WA1CYB/SDR_Gen2/AD9361-sheet-2-page7.kicad_sch

## KiCad design AD9361-sheet-2-page7.kicad_sch (2026-04-03)

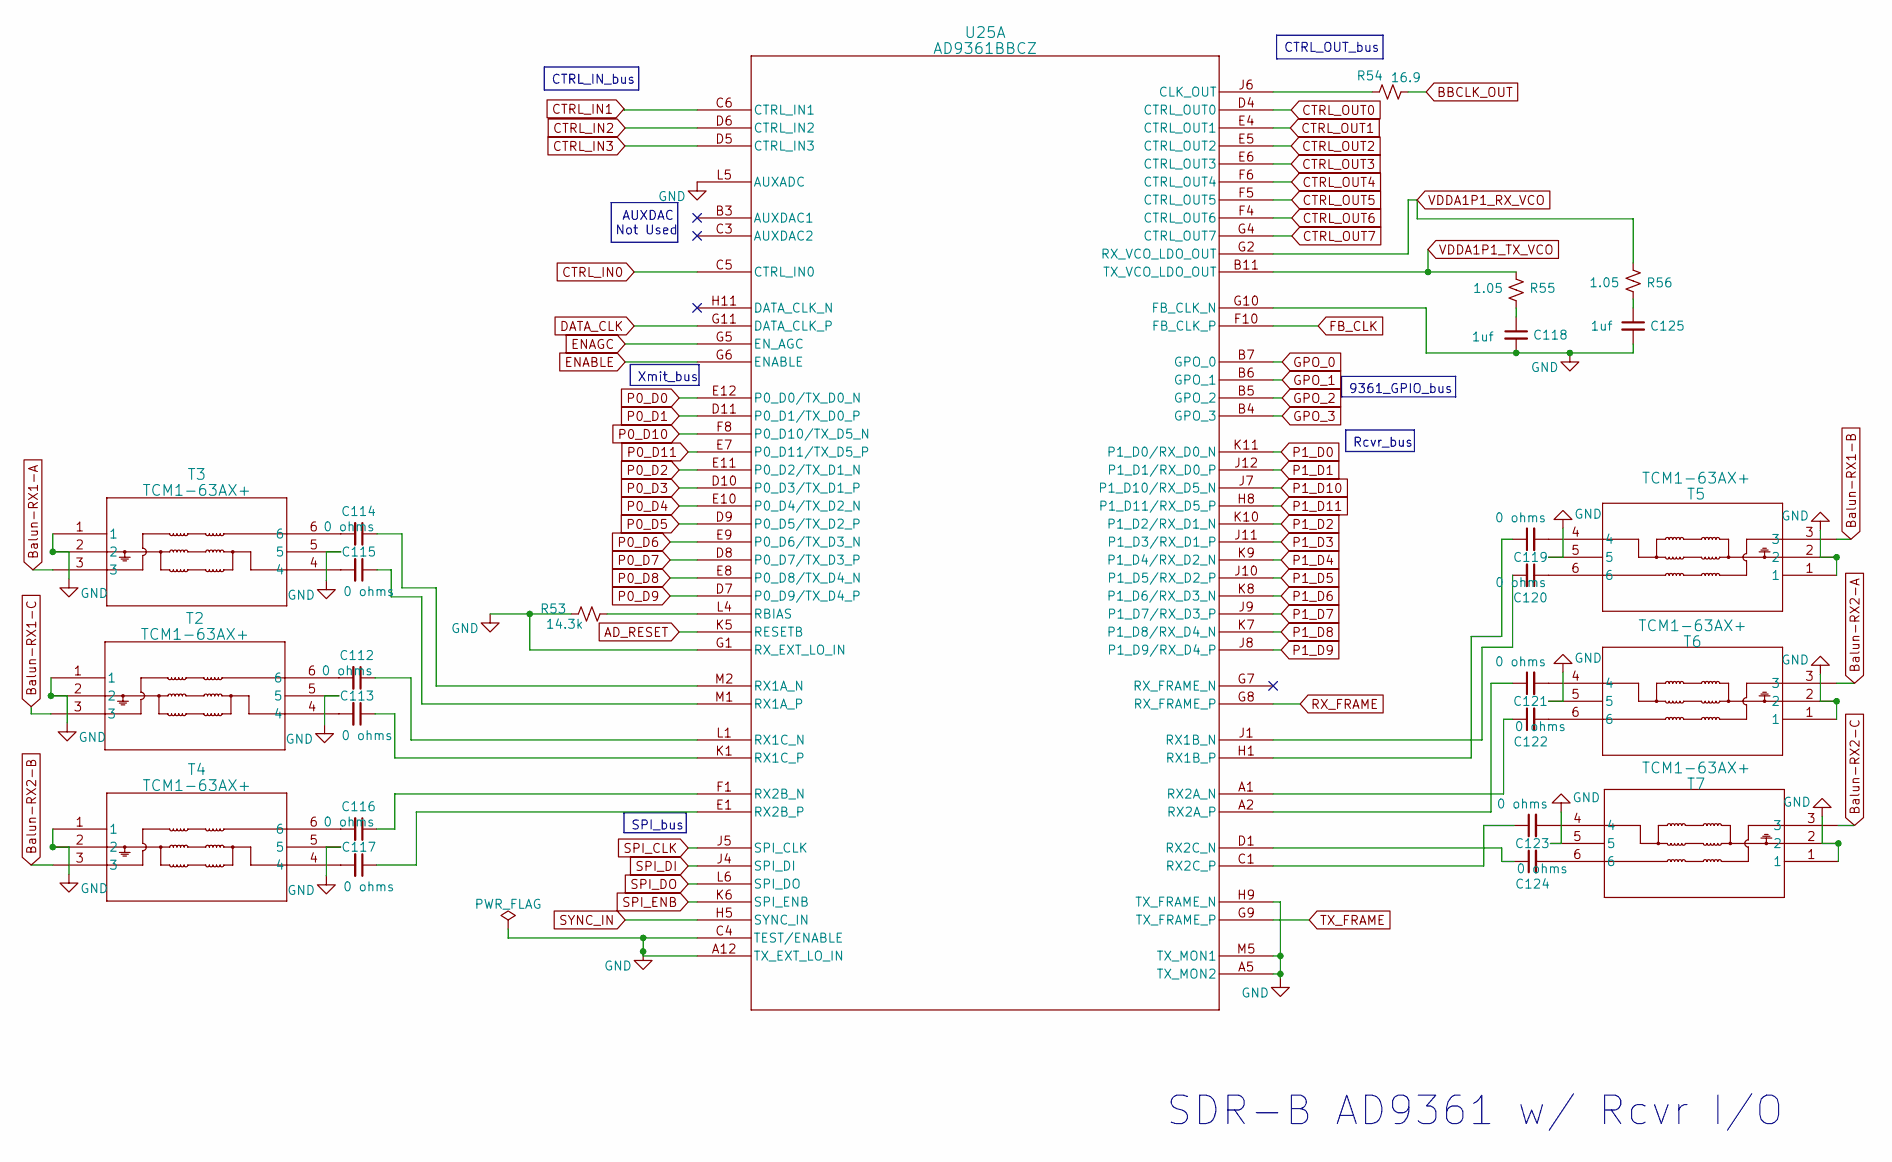
[picture p9: schematic AD9361-sheet-2-page7.kicad_sch]

Parts:
C112, C113, C114, C115, C116, C117, C119, C120, C121, C122, C123, C124: 0 ohms; C_0201_0603Metric
C118, C125: 1uf; C_0402_1005Metric
R53: 14.3k; R_0201_0603Metric
R54: 16.9; R_0201_0603Metric
R55, R56: 1.05; R_0201_0603Metric
T2, T3, T4, T5, T6, T7: TCM1-63AX+; DB1627_MNC
U25: AD9361BBCZ; BC_144_7_ADI

Connections:
AD_RESET: U25.K5 (RESETB)
BBCLK_OUT: R54.2
Balun-RX1-A: T3.3
Balun-RX1-B: T5.3
Balun-RX1-C: T2.3
Balun-RX2-A: T6.3
Balun-RX2-B: T4.3
Balun-RX2-C: T7.3
CTRL_IN0: U25.C5 (CTRL_IN0)
CTRL_IN1: U25.C6 (CTRL_IN1)
CTRL_IN2: U25.D6 (CTRL_IN2)
CTRL_IN3: U25.D5 (CTRL_IN3)
CTRL_OUT0: U25.D4 (CTRL_OUT0)
CTRL_OUT1: U25.E4 (CTRL_OUT1)
CTRL_OUT2: U25.E5 (CTRL_OUT2)
CTRL_OUT3: U25.E6 (CTRL_OUT3)
CTRL_OUT4: U25.F6 (CTRL_OUT4)
CTRL_OUT5: U25.F5 (CTRL_OUT5)
CTRL_OUT6: U25.F4 (CTRL_OUT6)
CTRL_OUT7: U25.G4 (CTRL_OUT7)
DATA_CLK: U25.G11 (DATA_CLK_P)
ENABLE: U25.G6 (ENABLE)
ENAGC: U25.G5 (EN_AGC)
FB_CLK: U25.F10 (FB_CLK_P)
GND: C118.2, C125.2, R53.1, T2.1, T2.2, T2.5, T3.1, T3.2, T3.5, T4.1, T4.2, T4.5, T5.1, T5.2, T5.5, T6.1, T6.2, T6.5, T7.1, T7.2, T7.5, U25.A5 (TX_MON2), U25.A12 (TX_EXT_LO_IN), U25.C4 (TEST/ENABLE), U25.G1 (RX_EXT_LO_IN), U25.G10 (FB_CLK_N), U25.H9 (TX_FRAME_N), U25.L5 (AUXADC), U25.M5 (TX_MON1)
GPO_0: U25.B7 (GPO_0)
GPO_1: U25.B6 (GPO_1)
GPO_2: U25.B5 (GPO_2)
GPO_3: U25.B4 (GPO_3)
unnamed: C112.1, U25.L1 (RX1C_N)
unnamed: C112.2, T2.6
unnamed: C113.1, U25.K1 (RX1C_P)
unnamed: C113.2, T2.4
unnamed: C114.1, U25.M2 (RX1A_N)
unnamed: C114.2, T3.6
unnamed: C115.1, U25.M1 (RX1A_P)
unnamed: C115.2, T3.4
unnamed: C116.1, U25.F1 (RX2B_N)
unnamed: C116.2, T4.6
unnamed: C117.1, U25.E1 (RX2B_P)
unnamed: C117.2, T4.4
unnamed: C118.1, R55.1
unnamed: C119.1, U25.H1 (RX1B_P)
unnamed: C119.2, T5.4
unnamed: C120.1, T5.6
unnamed: C120.2, U25.J1 (RX1B_N)
unnamed: C121.1, U25.A2 (RX2A_P)
unnamed: C121.2, T6.4
unnamed: C122.1, U25.A1 (RX2A_N)
unnamed: C122.2, T6.6
unnamed: C123.1, U25.C1 (RX2C_P)
unnamed: C123.2, T7.4
unnamed: C124.1, U25.D1 (RX2C_N)
unnamed: C124.2, T7.6
unnamed: C125.1, R56.1
unnamed: R53.2, U25.L4 (RBIAS)
unnamed: R54.1, U25.J6 (CLK_OUT)
P0_D0: U25.E12 (P0_D0/TX_D0_N)
P0_D1: U25.D11 (P0_D1/TX_D0_P)
P0_D2: U25.E11 (P0_D2/TX_D1_N)
P0_D3: U25.D10 (P0_D3/TX_D1_P)
P0_D4: U25.E10 (P0_D4/TX_D2_N)
P0_D5: U25.D9 (P0_D5/TX_D2_P)
P0_D6: U25.E9 (P0_D6/TX_D3_N)
P0_D7: U25.D8 (P0_D7/TX_D3_P)
P0_D8: U25.E8 (P0_D8/TX_D4_N)
P0_D9: U25.D7 (P0_D9/TX_D4_P)
P0_D10: U25.F8 (P0_D10/TX_D5_N)
P0_D11: U25.E7 (P0_D11/TX_D5_P)
P1_D0: U25.K11 (P1_D0/RX_D0_N)
P1_D1: U25.J12 (P1_D1/RX_D0_P)
P1_D2: U25.K10 (P1_D2/RX_D1_N)
P1_D3: U25.J11 (P1_D3/RX_D1_P)
P1_D4: U25.K9 (P1_D4/RX_D2_N)
P1_D5: U25.J10 (P1_D5/RX_D2_P)
P1_D6: U25.K8 (P1_D6/RX_D3_N)
P1_D7: U25.J9 (P1_D7/RX_D3_P)
P1_D8: U25.K7 (P1_D8/RX_D4_N)
P1_D9: U25.J8 (P1_D9/RX_D4_P)
P1_D10: U25.J7 (P1_D10/RX_D5_N)
P1_D11: U25.H8 (P1_D11/RX_D5_P)
RX_FRAME: U25.G8 (RX_FRAME_P)
SPI_CLK: U25.J5 (SPI_CLK)
SPI_DI: U25.J4 (SPI_DI)
SPI_DO: U25.L6 (SPI_DO)
SPI_ENB: U25.K6 (SPI_ENB)
SYNC_IN: U25.H5 (SYNC_IN)
TX_FRAME: U25.G9 (TX_FRAME_P)
VDDA1P1_RX_VCO: R56.2, U25.G2 (RX_VCO_LDO_OUT)
VDDA1P1_TX_VCO: R55.2, U25.B11 (TX_VCO_LDO_OUT)

Notes on the sheet:
AUXDAC Not Used
SDR-B AD9361 w/ Rcvr I/O
Rcvr_bus
9361_GPIO_bus
Xmit_bus
CTRL_OUT_bus
SPI_bus
CTRL_IN_bus
