WA1CYB/SDR_Gen2/AD9361-sheet-3-page8.kicad_sch

## KiCad design AD9361-sheet-3-page8.kicad_sch (2026-04-03)

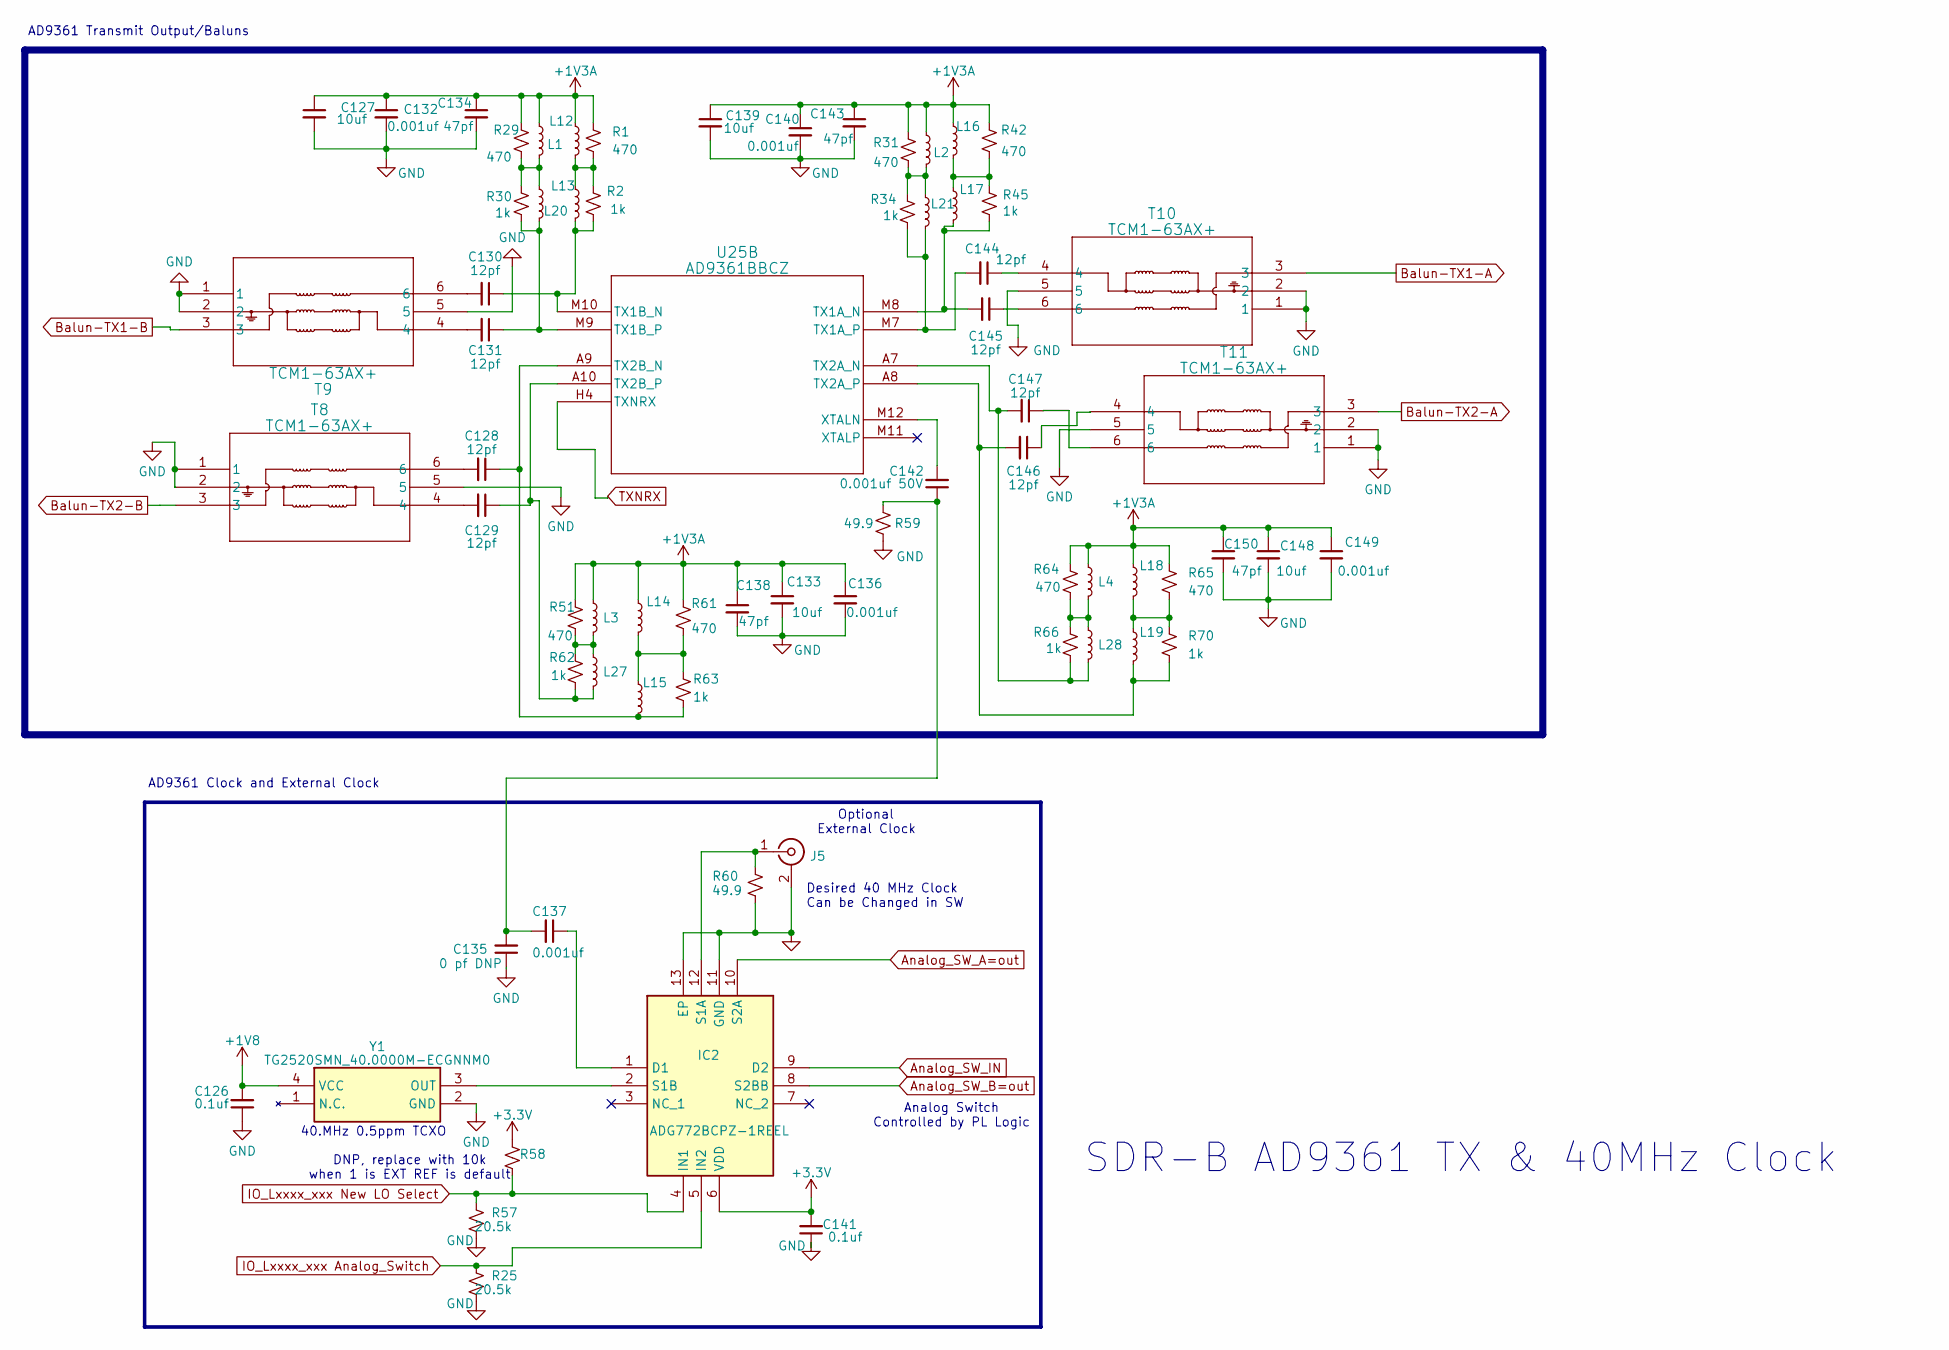
[picture p10: schematic AD9361-sheet-3-page8.kicad_sch]

Parts:
C126, C141: 0.1uf; C_0201_0603Metric
C127, C133, C139, C148: 10uf; C_0805_2012Metric
C128, C129, C130, C131, C144, C145, C146, C147: 12pf; C_0201_0603Metric
C132, C136, C137, C140, C149: 0.001uf; C_0201_0603Metric
C134, C138, C143, C150: 47pf; C_0603_1608Metric
C135: 0 pf DNP; C_0603_1608Metric
C142: 0.001uf 50V; C_0805_2012Metric
IC2: ADG772BCPZ-1REEL; QFN50P300X300X80-13N-D; Manufacturer_Part_Number ADG772BCPZ-1REEL; Mouser Part Number 584-ADG772BCPZ-1R
J5: Ext Clock; MMCX_Molex_73415-1471_Vertical
L1, L2, L3, L4, L12, L14, L16, L18: 330nh MLJ1005WR33JT000; INDC1005X55N
L13, L15, L17, L19, L20, L21, L27, L28: 33nh LQW15AN33NJ00D; LQW15CNR20J00B
R1, R29, R31, R42, R51, R61, R64, R65: 470; R_0402_1005Metric
R2, R30, R34, R45, R62, R63, R66, R70: 1k; R_0402_1005Metric
R25, R57: 20.5k; R_0201_0603Metric
R58: DNP; R_0603_1608Metric
R59, R60: 49.9; R_0201_0603Metric
T8, T9, T10, T11: TCM1-63AX+; DB1627_MNC
U25: AD9361BBCZ; BC_144_7_ADI
Y1: TG2520SMN_40.0000M-ECGNNM0; TG2520SMN400000MECGNNM0; Manufacturer_Part_Number TG2520SMN 40.0000M-ECGNNM0; Mouser Part Number 732-2520SMN40ECGNNM0

Connections:
+1V3A: C127.1, C132.1, C133.1, C134.1, C136.1, C138.1, C139.1, C140.1, C143.1, C148.1, C149.1, C150.1, L1.1, L2.1, L3.1, L4.1, L12.1, L14.1, L16.1, L18.1, R1.1, R29.1, R31.1, R42.1, R51.1, R61.1, R64.1, R65.1
+1V8: C126.2, Y1.4 (VCC)
+3.3V: C141.2, IC2.6 (VDD), R58.1
Analog_SW_A=out: IC2.10 (S2A)
Analog_SW_B=out: IC2.8 (S2BB)
Analog_SW_IN: IC2.9 (D2)
Balun-TX1-A: T10.3
Balun-TX1-B: T9.3
Balun-TX2-A: T11.3
Balun-TX2-B: T8.3
GND: C126.1, C127.2, C132.2, C133.2, C134.2, C135.1, C136.2, C138.2, C139.2, C140.2, C141.1, C143.2, C148.2, C149.2, C150.2, IC2.11 (GND), IC2.13 (EP), J5.2 (Ext), R25.2, R57.2, R59.2, R60.2, T8.1, T8.2, T8.5, T9.1, T9.2, T9.5, T10.1, T10.2, T10.5, T11.1, T11.2, T11.5, Y1.2 (GND)
IO_Lxxxx_xxx Analog_Switch: IC2.5 (IN2), R25.1
IO_Lxxxx_xxx New LO Select: IC2.4 (IN1), R57.1, R58.2
unnamed: C128.1, L15.2, R63.2, U25.A9 (TX2B_N)
unnamed: C128.2, T8.6
unnamed: C129.1, L27.2, R62.2, U25.A10 (TX2B_P)
unnamed: C129.2, T8.4
unnamed: C130.1, L13.2, R2.2, U25.M10 (TX1B_N)
unnamed: C130.2, T9.6
unnamed: C131.1, L20.2, R30.2, U25.M9 (TX1B_P)
unnamed: C131.2, T9.4
unnamed: C135.2, C137.2, C142.1, R59.1
unnamed: C137.1, IC2.1 (D1)
unnamed: C142.2, U25.M12 (XTALN)
unnamed: C144.1, T10.4
unnamed: C144.2, L21.2, R34.2, U25.M7 (TX1A_P)
unnamed: C145.1, T10.6
unnamed: C145.2, L17.2, R45.2, U25.M8 (TX1A_N)
unnamed: C146.1, T11.4
unnamed: C146.2, L19.2, R70.2, U25.A8 (TX2A_P)
unnamed: C147.1, T11.6
unnamed: C147.2, L28.2, R66.2, U25.A7 (TX2A_N)
unnamed: IC2.2 (S1B), Y1.3 (OUT)
unnamed: IC2.12 (S1A), J5.1 (In), R60.1
unnamed: L1.2, L20.1, R29.2, R30.1
unnamed: L2.2, L21.1, R31.2, R34.1
unnamed: L12.2, L13.1, R1.2, R2.1
unnamed: L14.2, L15.1, R61.2, R63.1
unnamed: L16.2, L17.1, R42.2, R45.1
unnamed: L18.2, L19.1, R65.2, R70.1
unnamed: L3.2, L27.1, R51.2, R62.1
unnamed: L4.2, L28.1, R64.2, R66.1
TXNRX: U25.H4 (TXNRX)

Notes on the sheet:
Analog Switch Controlled by PL Logic
Desired 40 MHz Clock Can be Changed in SW
SDR-B AD9361 TX & 40MHz Clock
Optional External Clock
AD9361 Clock and External Clock
40.MHz 0.5ppm TCXO
DNP, replace with 10k when 1 is EXT REF is default
AD9361 Transmit Output/Baluns
