WA1CYB/SDR_Gen2/AD9361-sheet-4-page8.kicad_sch

## KiCad design AD9361-sheet-4-page8.kicad_sch (2026-04-03)

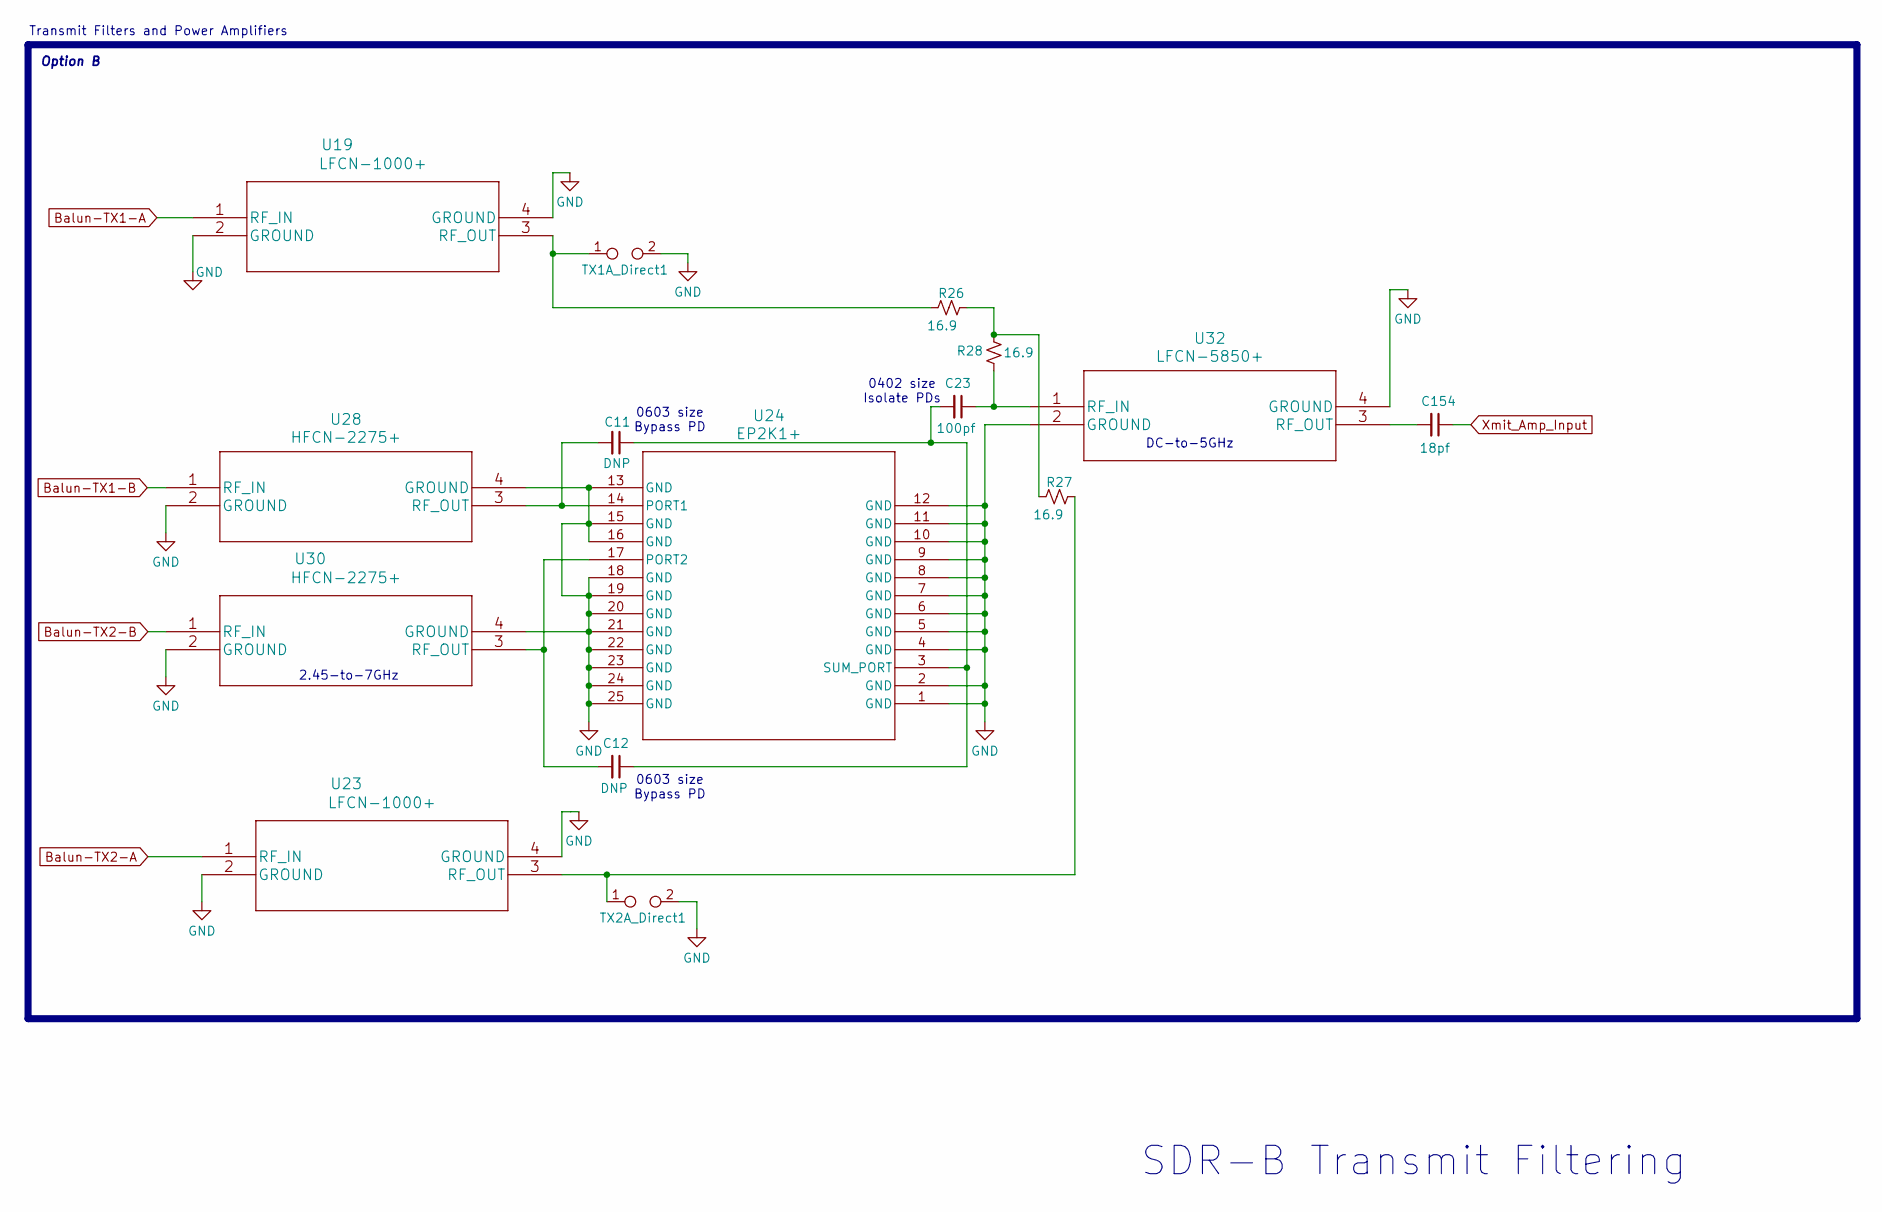
[picture p11: schematic AD9361-sheet-4-page8.kicad_sch]

Parts:
C11, C12: DNP; C_0603_1608Metric
C23: 100pf; C_0402_1005Metric
C154: 18pf; C_0201_0603Metric
R26, R27, R28: 16.9; R_0201_0603Metric
TX1A_Direct1, TX2A_Direct1: TestPoint_2Pads_Pitch2.54mm_Drill0.8mm
U19, U23: LFCN-1000+; Filter_Mini-Circuits_FV1206
U24: EP2K1+; DG1847_MNC-L
U28, U30: HFCN-2275+; Filter_Mini-Circuits_FV1206
U32: LFCN-5850+; Filter_Mini-Circuits_FV1206

Connections:
Balun-TX1-A: U19.1 (RF_IN)
Balun-TX1-B: U28.1 (RF_IN)
Balun-TX2-A: U23.1 (RF_IN)
Balun-TX2-B: U30.1 (RF_IN)
GND: TX1A_Direct1.2, TX2A_Direct1.2, U19.2 (GROUND), U19.4 (GROUND), U23.2 (GROUND), U23.4 (GROUND), U24.1 (GND), U24.2 (GND), U24.4 (GND), U24.5 (GND), U24.6 (GND), U24.7 (GND), U24.8 (GND), U24.9 (GND), U24.10 (GND), U24.11 (GND), U24.12 (GND), U24.13 (GND), U24.15 (GND), U24.16 (GND), U24.18 (GND), U24.19 (GND), U24.20 (GND), U24.21 (GND), U24.22 (GND), U24.23 (GND), U24.24 (GND), U24.25 (GND), U28.2 (GROUND), U28.4 (GROUND), U30.2 (GROUND), U30.4 (GROUND), U32.2 (GROUND), U32.4 (GROUND)
unnamed: C11.1, C12.1, C23.2, U24.3 (SUM_PORT)
unnamed: C11.2, U24.14 (PORT1), U28.3 (RF_OUT)
unnamed: C12.2, U24.17 (PORT2), U30.3 (RF_OUT)
unnamed: C23.1, R28.1, U32.1 (RF_IN)
unnamed: C154.2, U32.3 (RF_OUT)
unnamed: R26.1, R27.2, R28.2
unnamed: R26.2, TX1A_Direct1.1, U19.3 (RF_OUT)
unnamed: R27.1, TX2A_Direct1.1, U23.3 (RF_OUT)
Xmit_Amp_Input: C154.1

Notes on the sheet:
0603 size Bypass PD
0402 size Isolate PDs
SDR-B Transmit Filtering
DC-to-5GHz
2.45-to-7GHz
Transmit Filters and Power Amplifiers
Option B
