WA1CYB/SDR_Gen2/Filters-page2.kicad_sch

## KiCad design Filters-page2.kicad_sch (2026-04-03)

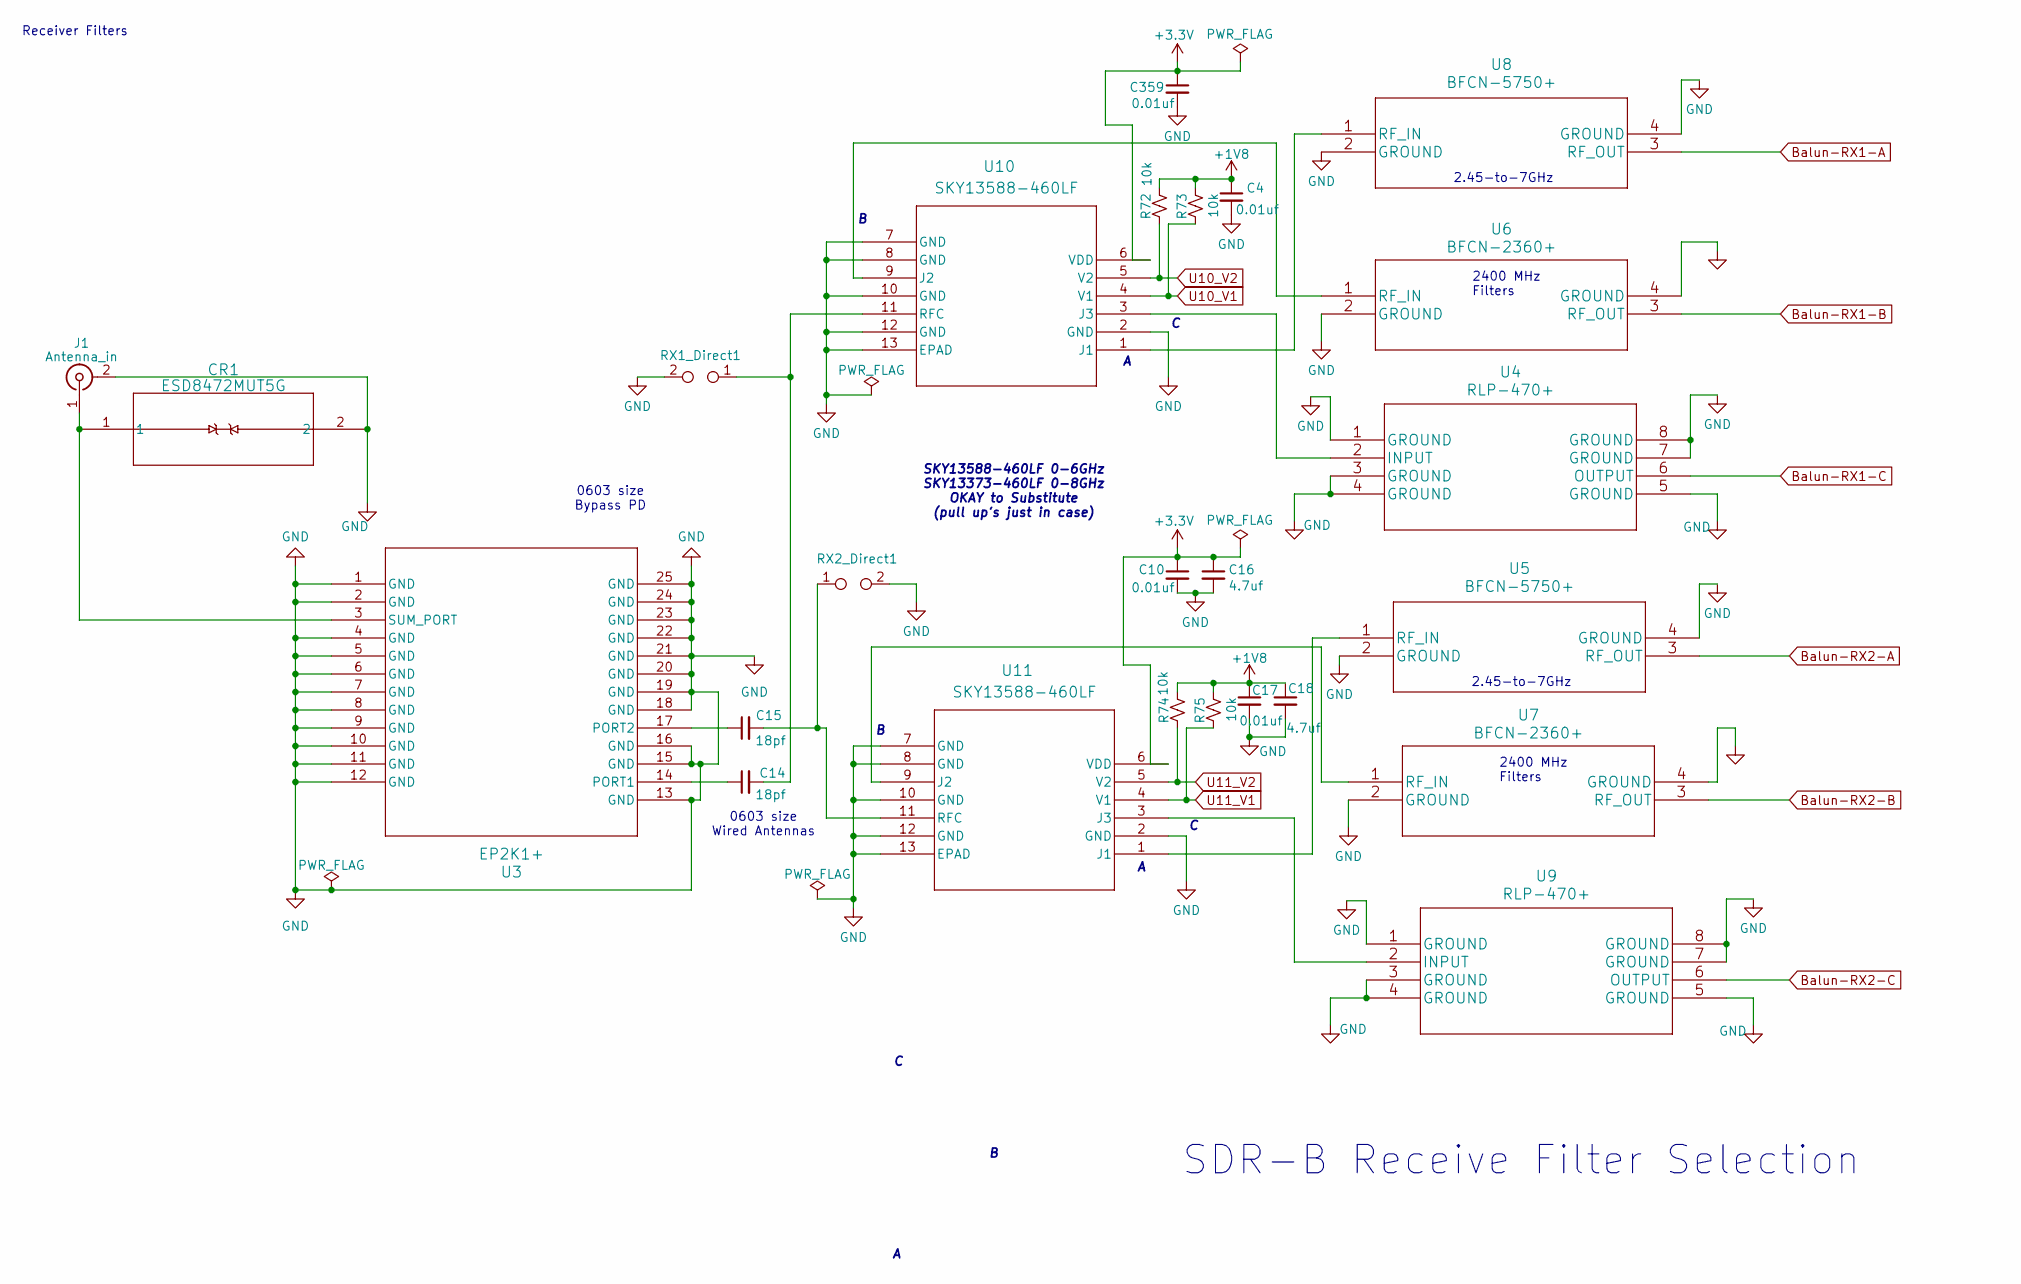
[picture p12: schematic Filters-page2.kicad_sch]

Parts:
C4, C10, C17, C359: 0.01uf; C_0201_0603Metric
C14, C15: 18pf; C_0402_1005Metric
C16, C18: 4.7uf; C_0402_1005Metric
CR1: ESD8472MUT5G; X3DFN2_ONS
J1: Antenna_in; MMCX_Molex_73415-1471_Vertical
R72, R73, R74, R75: 10k; R_0201_0603Metric
RX1_Direct1, RX2_Direct1: TestPoint_2Pads_Pitch2.54mm_Drill0.8mm
U3: EP2K1+; DG1847_MNC-L
U4, U9: RLP-470+; Mini-Circuits_GP731
U5, U8: BFCN-5750+; Filter_Mini-Circuits_FV1206-4
U6, U7: BFCN-2360+; Filter_Mini-Circuits_FV1206
U10, U11: SKY13588-460LF; QFN12_SKY-L

Connections:
+1V8: C4.1, C17.1, C18.1, R72.2, R73.2, R74.2, R75.2
+3.3V: C10.1, C16.1, C359.1, U10.6 (VDD), U11.6 (VDD)
Balun-RX1-A: U8.3 (RF_OUT)
Balun-RX1-B: U6.3 (RF_OUT)
Balun-RX1-C: U4.6 (OUTPUT)
Balun-RX2-A: U5.3 (RF_OUT)
Balun-RX2-B: U7.3 (RF_OUT)
Balun-RX2-C: U9.6 (OUTPUT)
GND: C4.2, C10.2, C16.2, C17.2, C18.2, C359.2, CR1.2, J1.2 (Ext), RX1_Direct1.2, RX2_Direct1.2, U3.1 (GND), U3.2 (GND), U3.4 (GND), U3.5 (GND), U3.6 (GND), U3.7 (GND), U3.8 (GND), U3.9 (GND), U3.10 (GND), U3.11 (GND), U3.12 (GND), U3.13 (GND), U3.15 (GND), U3.16 (GND), U3.18 (GND), U3.19 (GND), U3.20 (GND), U3.21 (GND), U3.22 (GND), U3.23 (GND), U3.24 (GND), U3.25 (GND), U4.1 (GROUND), U4.3 (GROUND), U4.4 (GROUND), U4.5 (GROUND), U4.7 (GROUND), U4.8 (GROUND), U5.2 (GROUND), U5.4 (GROUND), U6.2 (GROUND), U6.4 (GROUND), U7.2 (GROUND), U7.4 (GROUND), U8.2 (GROUND), U8.4 (GROUND), U9.1 (GROUND), U9.3 (GROUND), U9.4 (GROUND), U9.5 (GROUND), U9.7 (GROUND), U9.8 (GROUND), U10.2 (GND), U10.7 (GND), U10.8 (GND), U10.10 (GND), U10.12 (GND), U10.13 (EPAD), U11.2 (GND), U11.7 (GND), U11.8 (GND), U11.10 (GND), U11.12 (GND), U11.13 (EPAD)
unnamed: C14.1, U3.14 (PORT1)
unnamed: C14.2, RX1_Direct1.1, U10.11 (RFC)
unnamed: C15.1, U3.17 (PORT2)
unnamed: C15.2, RX2_Direct1.1, U11.11 (RFC)
unnamed: CR1.1, J1.1 (In), U3.3 (SUM_PORT)
unnamed: U8.1 (RF_IN), U10.1 (J1)
unnamed: U4.2 (INPUT), U10.3 (J3)
unnamed: U6.1 (RF_IN), U10.9 (J2)
unnamed: U5.1 (RF_IN), U11.1 (J1)
unnamed: U9.2 (INPUT), U11.3 (J3)
unnamed: U7.1 (RF_IN), U11.9 (J2)
U10_V1: R73.1, U10.4 (V1)
U10_V2: R72.1, U10.5 (V2)
U11_V1: R75.1, U11.4 (V1)
U11_V2: R74.1, U11.5 (V2)

Notes on the sheet:
0603 size Bypass PD
2400 MHz Filters
SKY13588-460LF 0-6GHz SKY13373-460LF 0-8GHz OKAY to Substitute (pull up's just in case)
SDR-B Receive Filter Selection
2.45-to-7GHz
Receiver Filters
0603 size Wired Antennas
