WA1CYB/SDR_Gen2/Initerface-page13.kicad_sch

## KiCad design Initerface-page13.kicad_sch (2026-04-03)

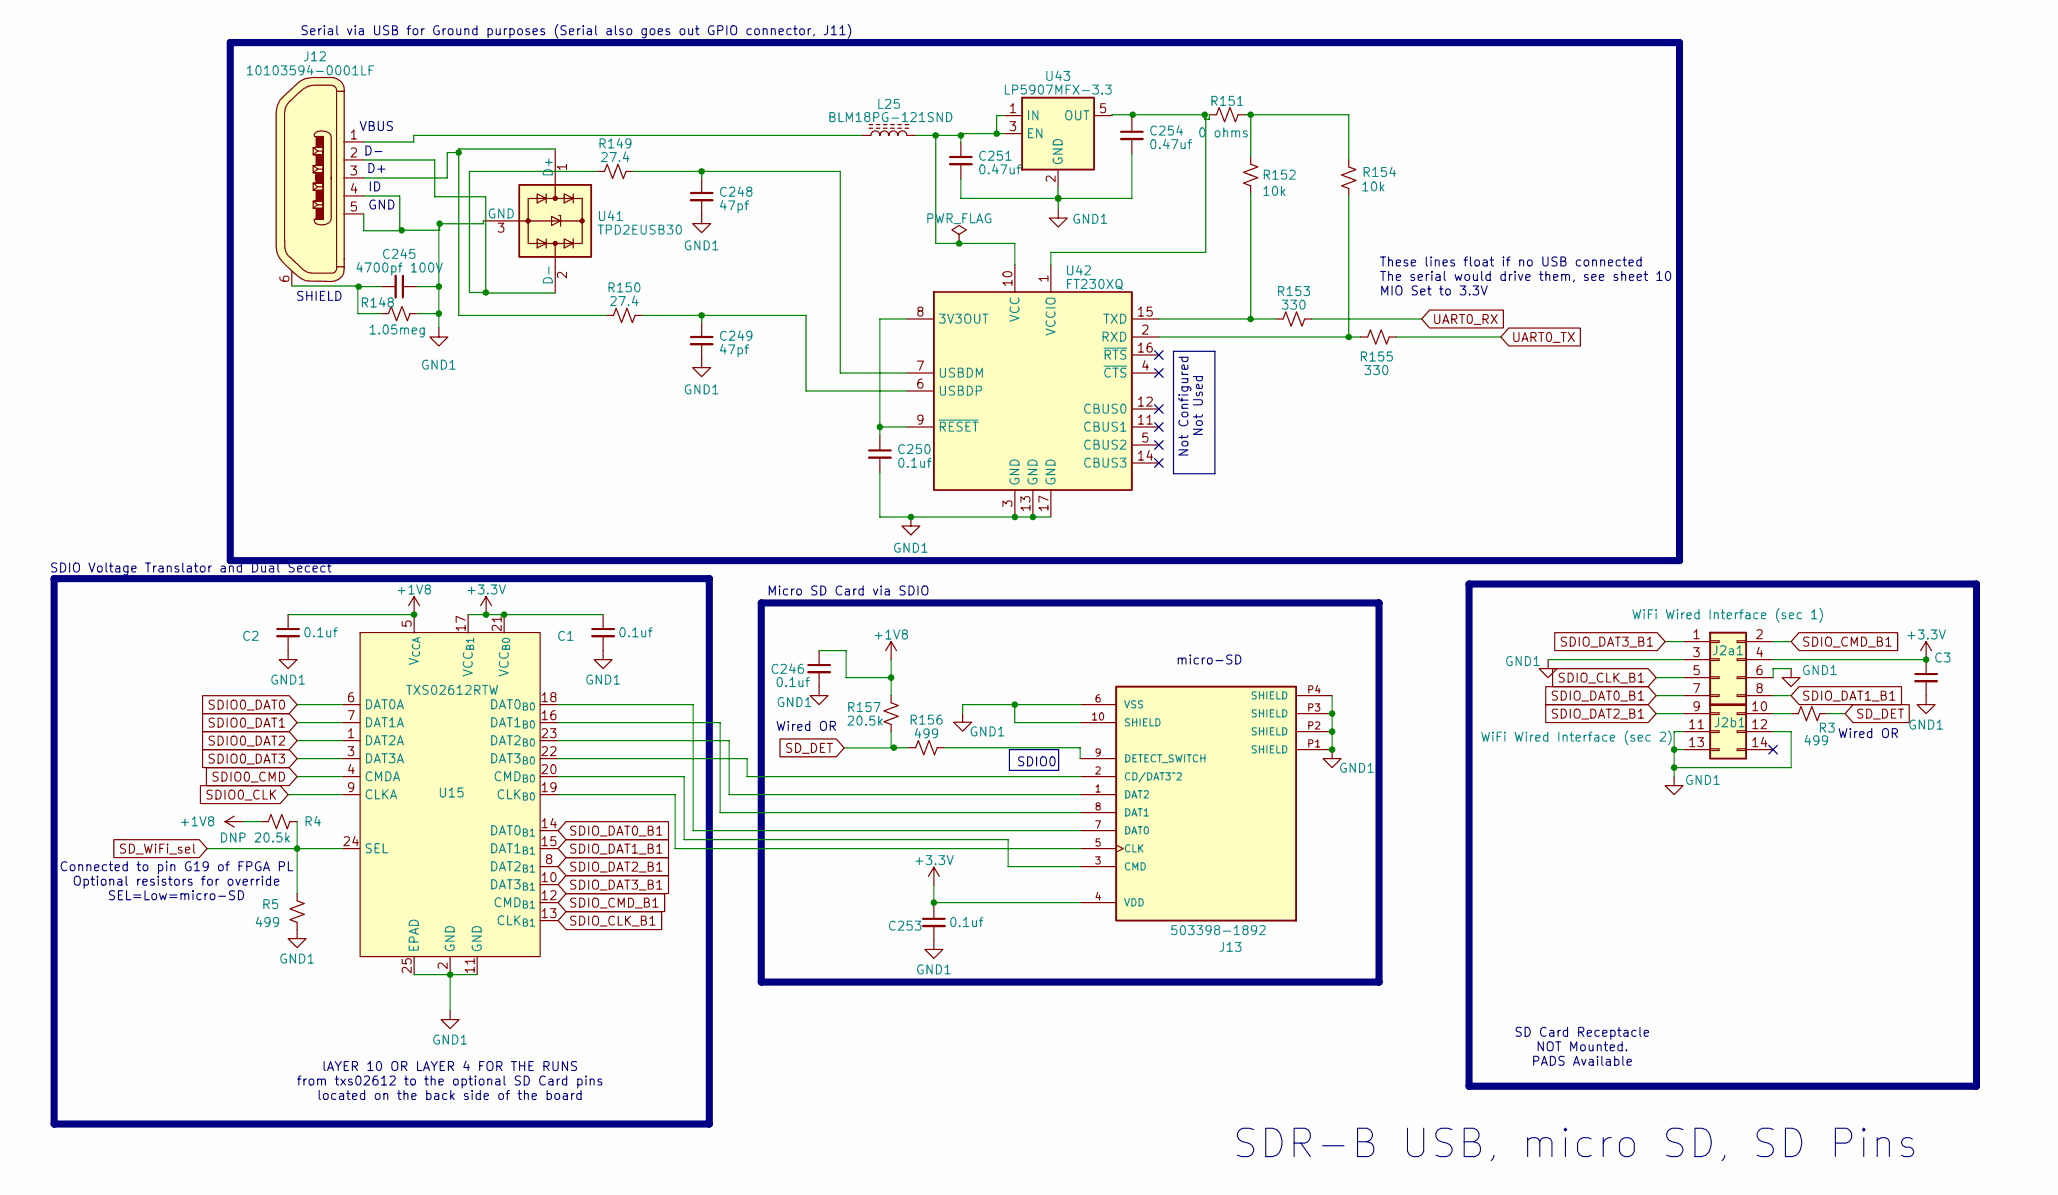
[picture p13: schematic Initerface-page13.kicad_sch]

Parts:
C1, C2, C3, C246, C250, C253: 0.1uf; C_0201_0603Metric
C245: 4700pf 100V; C_1206_3216Metric
C248, C249: 47pf; C_0201_0603Metric
C251, C254: 0.47uf; C_0201_0603Metric
J2a1: WiFi Wired Interface (sec 1); Custom_Wire_2x04_P2.00mm_Vertical
J2b1: WiFi Wired Interface (sec 2); Custom_Wired_2x03_P2.00mm_Vertical
J12: 10103594-0001LF; USB_Micro-B_Amphenol_10103594-0001LF_Horizontal; MPN 10103594-0001LF; Digi-Key_PN 609-4050-1-ND
J13: 503398-1892; MOLEX_503398-1892; PARTREV 0; DigiKey_Part_Number WM11190TR-ND
L25: BLM18PG-121SND; IND_BLM18_0603_MUR
R3, R5, R156: 499; R_0805_2012Metric
R4: DNP 20.5k; R_0805_2012Metric
R148: 1.05meg; R_0201_0603Metric
R149, R150: 27.4; R_0805_2012Metric
R151: 0 ohms; R_0201_0603Metric
R152, R154: 10k; R_0201_0603Metric
R153, R155: 330; R_0201_0603Metric
R157: 20.5k; R_0805_2012Metric
U15: TXS02612RTW; WQFN-24-1EP_4x4mm_P0.5mm_EP2.45x2.45mm_ThermalVias
U41: TPD2EUSB30; Texas_DRT-3
U42: FT230XQ; QFN-16-1EP_4x4mm_P0.65mm_EP2.1x2.1mm
U43: LP5907MFX-3.3; SOT-23-5

Connections:
+1V8: C2.1, C246.1, R4.2, R157.2, U15.5 (V_{CCA})
+3.3V: C1.1, C3.1, C253.1, J2a1.4, J13.4 (VDD), U15.17 (VCC_{B1}), U15.21 (VCC_{B0})
GND1: C1.2, C2.2, C3.2, C245.1, C246.2, C248.2, C249.2, C250.2, C251.2, C253.2, C254.2, J2a1.3, J2a1.6, J2b1.11, J2b1.12, J2b1.13, J12.4, J12.5, J13.6 (VSS), J13.10 (SHIELD), J13.P1 (SHIELD), J13.P2 (SHIELD), J13.P3 (SHIELD), J13.P4 (SHIELD), R5.2, R148.1, U15.2 (GND), U15.11 (GND), U15.25 (EPAD), U41.3 (GND), U42.3 (GND), U42.13 (GND), U42.17 (GND), U43.2 (GND)
unnamed: C245.2, J12.6, R148.2
unnamed: C248.1, R149.1, U42.7 (USBDM)
unnamed: C249.1, R150.1, U42.6 (USBDP)
unnamed: C250.1, U42.8 (3V3OUT), U42.9 (~RESET)
unnamed: C251.1, L25.2, U42.10 (VCC), U43.1 (IN), U43.3 (EN)
unnamed: C254.1, R151.1, U42.1 (VCCIO), U43.5 (OUT)
unnamed: J2b1.10, R3.1
unnamed: J12.1, L25.1
unnamed: J12.2, R149.2, U41.2 (D-)
unnamed: J12.3, R150.2, U41.1 (D+)
unnamed: J13.1 (DAT2), U15.23 (DAT2_{B0})
unnamed: J13.2 (CD/DAT3^2), U15.22 (DAT3_{B0})
unnamed: J13.3 (CMD), U15.20 (CMD_{B0})
unnamed: J13.5 (CLK), U15.19 (CLK_{B0})
unnamed: J13.7 (DAT0), U15.18 (DAT0_{B0})
unnamed: J13.8 (DAT1), U15.16 (DAT1_{B0})
unnamed: J13.9 (DETECT_SWITCH), R156.1
unnamed: R151.2, R152.1, R154.1
unnamed: R152.2, R153.2, U42.15 (TXD)
unnamed: R154.2, R155.2, U42.2 (RXD)
SDIO0_CLK: U15.9 (CLKA)
SDIO0_CMD: U15.4 (CMDA)
SDIO0_DAT0: U15.6 (DAT0A)
SDIO0_DAT1: U15.7 (DAT1A)
SDIO0_DAT2: U15.1 (DAT2A)
SDIO0_DAT3: U15.3 (DAT3A)
SDIO_CLK_B1: J2a1.5, U15.13 (CLK_{B1})
SDIO_CMD_B1: J2a1.2, U15.12 (CMD_{B1})
SDIO_DAT0_B1: J2a1.7, U15.14 (DAT0_{B1})
SDIO_DAT1_B1: J2a1.8, U15.15 (DAT1_{B1})
SDIO_DAT2_B1: J2b1.9, U15.8 (DAT2_{B1})
SDIO_DAT3_B1: J2a1.1, U15.10 (DAT3_{B1})
SD_DET: R3.2, R156.2, R157.1
SD_WiFi_sel: R4.1, R5.1, U15.24 (SEL)
UART0_RX: R153.1
UART0_TX: R155.1

Notes on the sheet:
micro-SD
SDIO Voltage Translator and Dual Secect
These lines float if no USB connected The serial would drive them, see sheet 10 MIO Set to 3.3V
Wired OR
SDR-B USB, micro SD, SD Pins
VBUS
SD Card Receptacle NOT Mounted. PADS Available
SHIELD
Not Configured Not Used
Micro SD Card via SDIO
Serial via USB for Ground purposes (Serial also goes out GPIO connector, J11)
lAYER 10 OR LAYER 4 FOR THE RUNS from txs02612 to the optional SD Card pins located on the back side of the board
Connected to pin G19 of FPGA PL Optional resistors for override SEL=Low=micro-SD
GND
SDIO0
