WA1CYB/SDR_Gen2/Misc.kicad_sch

## KiCad design Misc.kicad_sch (2026-04-03)

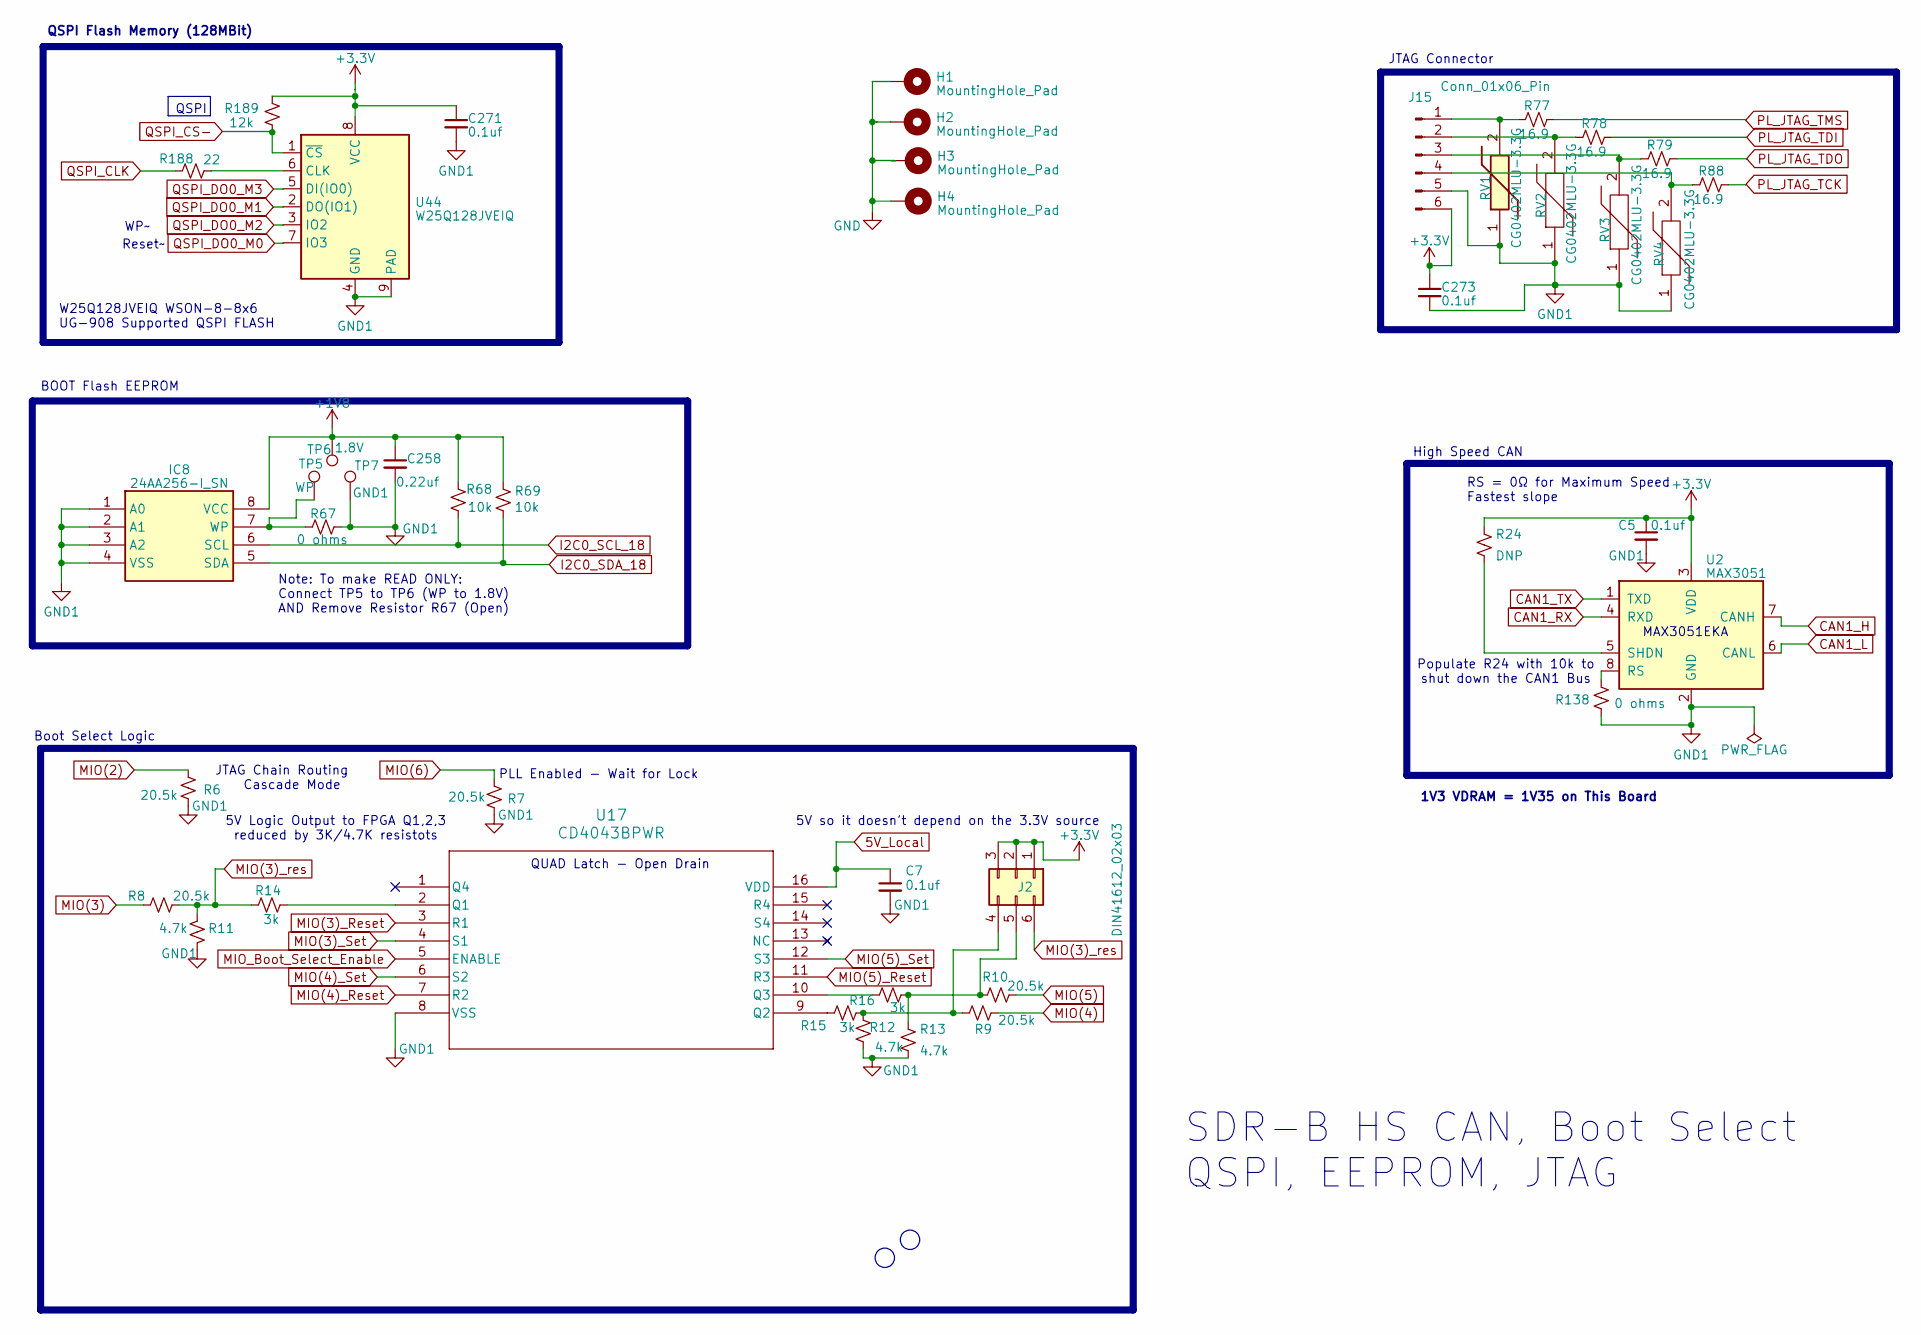
[picture p14: schematic Misc.kicad_sch]

Parts:
C5, C7, C271, C273: 0.1uf; C_0201_0603Metric
C258: 0.22uf; C_0201_0603Metric
H1, H2, H3, H4: MountingHole_Pad; MountingHole_3.2mm_M3_Pad_Via
IC8: 24AA256-I_SN; SOIC127P600X175-8N; Manufacturer_Part_Number 24AA256-I/SN; Mouser Part Number 579-24AA256-I/SN
J2: DIN41612_02x03; Hirose_DF11-6DP-2DSA_2x03_P2.00mm_Vertical
J15: Conn_01x06_Pin; PinSocket_1x06_P2.54mm_Vertical
R6, R7, R8, R9, R10: 20.5k; R_0201_0603Metric
R11, R12, R13: 4.7k; R_0201_0603Metric
R14, R15, R16: 3k; R_0201_0603Metric
R24: DNP; R_0201_0603Metric
R67, R138: 0 ohms; R_0201_0603Metric
R68, R69: 10k; R_0201_0603Metric
R77, R78, R79, R88: 16.9; R_0201_0603Metric
R188: 22; R_0201_0603Metric
R189: 12k; R_0201_0603Metric
RV1, RV2, RV3, RV4: CG0402MLU-3.3G; VARC1005X41N; Manufacturer_Part_Number CG0402MLU-3.3G; Mouser Part Number 652-CG0402MLU-3.3G
TP5: WP; TestPoint_THTPad_1.5x1.5mm_Drill0.7mm
TP6: 1.8V; TestPoint_THTPad_1.5x1.5mm_Drill0.7mm
TP7: GND1; TestPoint_THTPad_1.5x1.5mm_Drill0.7mm
U2: MAX3051; MAX3051EKA
U17: CD4043BPWR; CD4043_SOP65P640X120-16N
U44: W25Q128JVEIQ; WSON_128JVEIQ_WIN

Connections:
5V_Local: C7.1, U17.16 (VDD)
+1V8: C258.1, IC8.8 (VCC), R68.1, R69.1, TP6.1
+3.3V: C5.1, C271.1, C273.1, J2.1, J2.2, J2.3, J15.6, R24.2, R189.2, U2.3 (VDD), U44.8 (VCC)
CAN1_H: U2.7 (CANH)
CAN1_L: U2.6 (CANL)
CAN1_RX: U2.4 (RXD)
CAN1_TX: U2.1 (TXD)
GND: H1.1, H2.1, H3.1, H4.1
GND1: C5.2, C7.2, C258.2, C271.2, C273.2, IC8.1 (A0), IC8.2 (A1), IC8.3 (A2), IC8.4 (VSS), J15.5, R6.1, R7.1, R11.1, R12.1, R13.1, R67.2, R138.1, RV1.1, RV2.1, RV3.1, RV4.1, TP7.1, U2.2 (GND), U17.8 (VSS), U44.4 (GND), U44.9 (PAD)
I2C0_SCL_18: IC8.6 (SCL), R68.2
I2C0_SDA_18: IC8.5 (SDA), R69.2
MIO(2): R6.2
MIO(3): R8.1
MIO(3)_Reset: U17.3 (R1)
MIO(3)_Set: U17.4 (S1)
MIO(3)_res: J2.6, R8.2, R11.2, R14.2
MIO(4): R9.1
MIO(4)_Reset: U17.7 (R2)
MIO(4)_Set: U17.6 (S2)
MIO(5): R10.1
MIO(5)_Reset: U17.11 (R3)
MIO(5)_Set: U17.12 (S3)
MIO(6): R7.2
MIO_Boot_Select_Enable: U17.5 (ENABLE)
unnamed: IC8.7 (WP), R67.1, TP5.1
unnamed: J2.4, R9.2, R12.2, R15.1
unnamed: J2.5, R10.2, R13.2, R16.1
unnamed: J15.1, R77.1, RV1.2
unnamed: J15.2, R78.1, RV2.2
unnamed: J15.3, R79.1, RV3.2
unnamed: J15.4, R88.1, RV4.2
unnamed: R14.1, U17.2 (Q1)
unnamed: R15.2, U17.9 (Q2)
unnamed: R16.2, U17.10 (Q3)
unnamed: R24.1, U2.5 (SHDN)
unnamed: R138.2, U2.8 (RS)
unnamed: R188.2, U44.6 (CLK)
PL_JTAG_TCK: R88.2
PL_JTAG_TDI: R78.2
PL_JTAG_TDO: R79.2
PL_JTAG_TMS: R77.2
QSPI_CLK: R188.1
QSPI_CS-: R189.1, U44.1 (~CS)
QSPI_DO0_M0: U44.7 (IO3)
QSPI_DO0_M1: U44.2 (DO(IO1))
QSPI_DO0_M2: U44.3 (IO2)
QSPI_DO0_M3: U44.5 (DI(IO0))

Notes on the sheet:
SDR-B HS CAN, Boot Select QSPI, EEPROM, JTAG
Populate R24 with 10k to shut down the CAN1 Bus
RS = 0Ω for Maximum Speed Fastest slope
1V3 VDRAM = 1V35 on This Board
Boot Select Logic
WP~
High Speed CAN
5V Logic Output to FPGA Q1,2,3 reduced by 3K/4.7K resistots
5V so it doesn't depend on the 3.3V source
JTAG Chain Routing Cascade Mode
QSPI Flash Memory (128MBit)
W25Q128JVEIQ WSON-8-8x6 UG-908 Supported QSPI FLASH
JTAG Connector
BOOT Flash EEPROM
MAX3051EKA
PLL Enabled - Wait for Lock
Note: To make READ ONLY: Connect TP5 to TP6 (WP to 1.8V) AND Remove Resistor R67 (Open)
QUAD Latch - Open Drain
Reset~
QSPI
