WA1CYB/SDR_Gen2/Transmit Amplifier.kicad_sch

## KiCad design Transmit Amplifier.kicad_sch (2026-04-03)

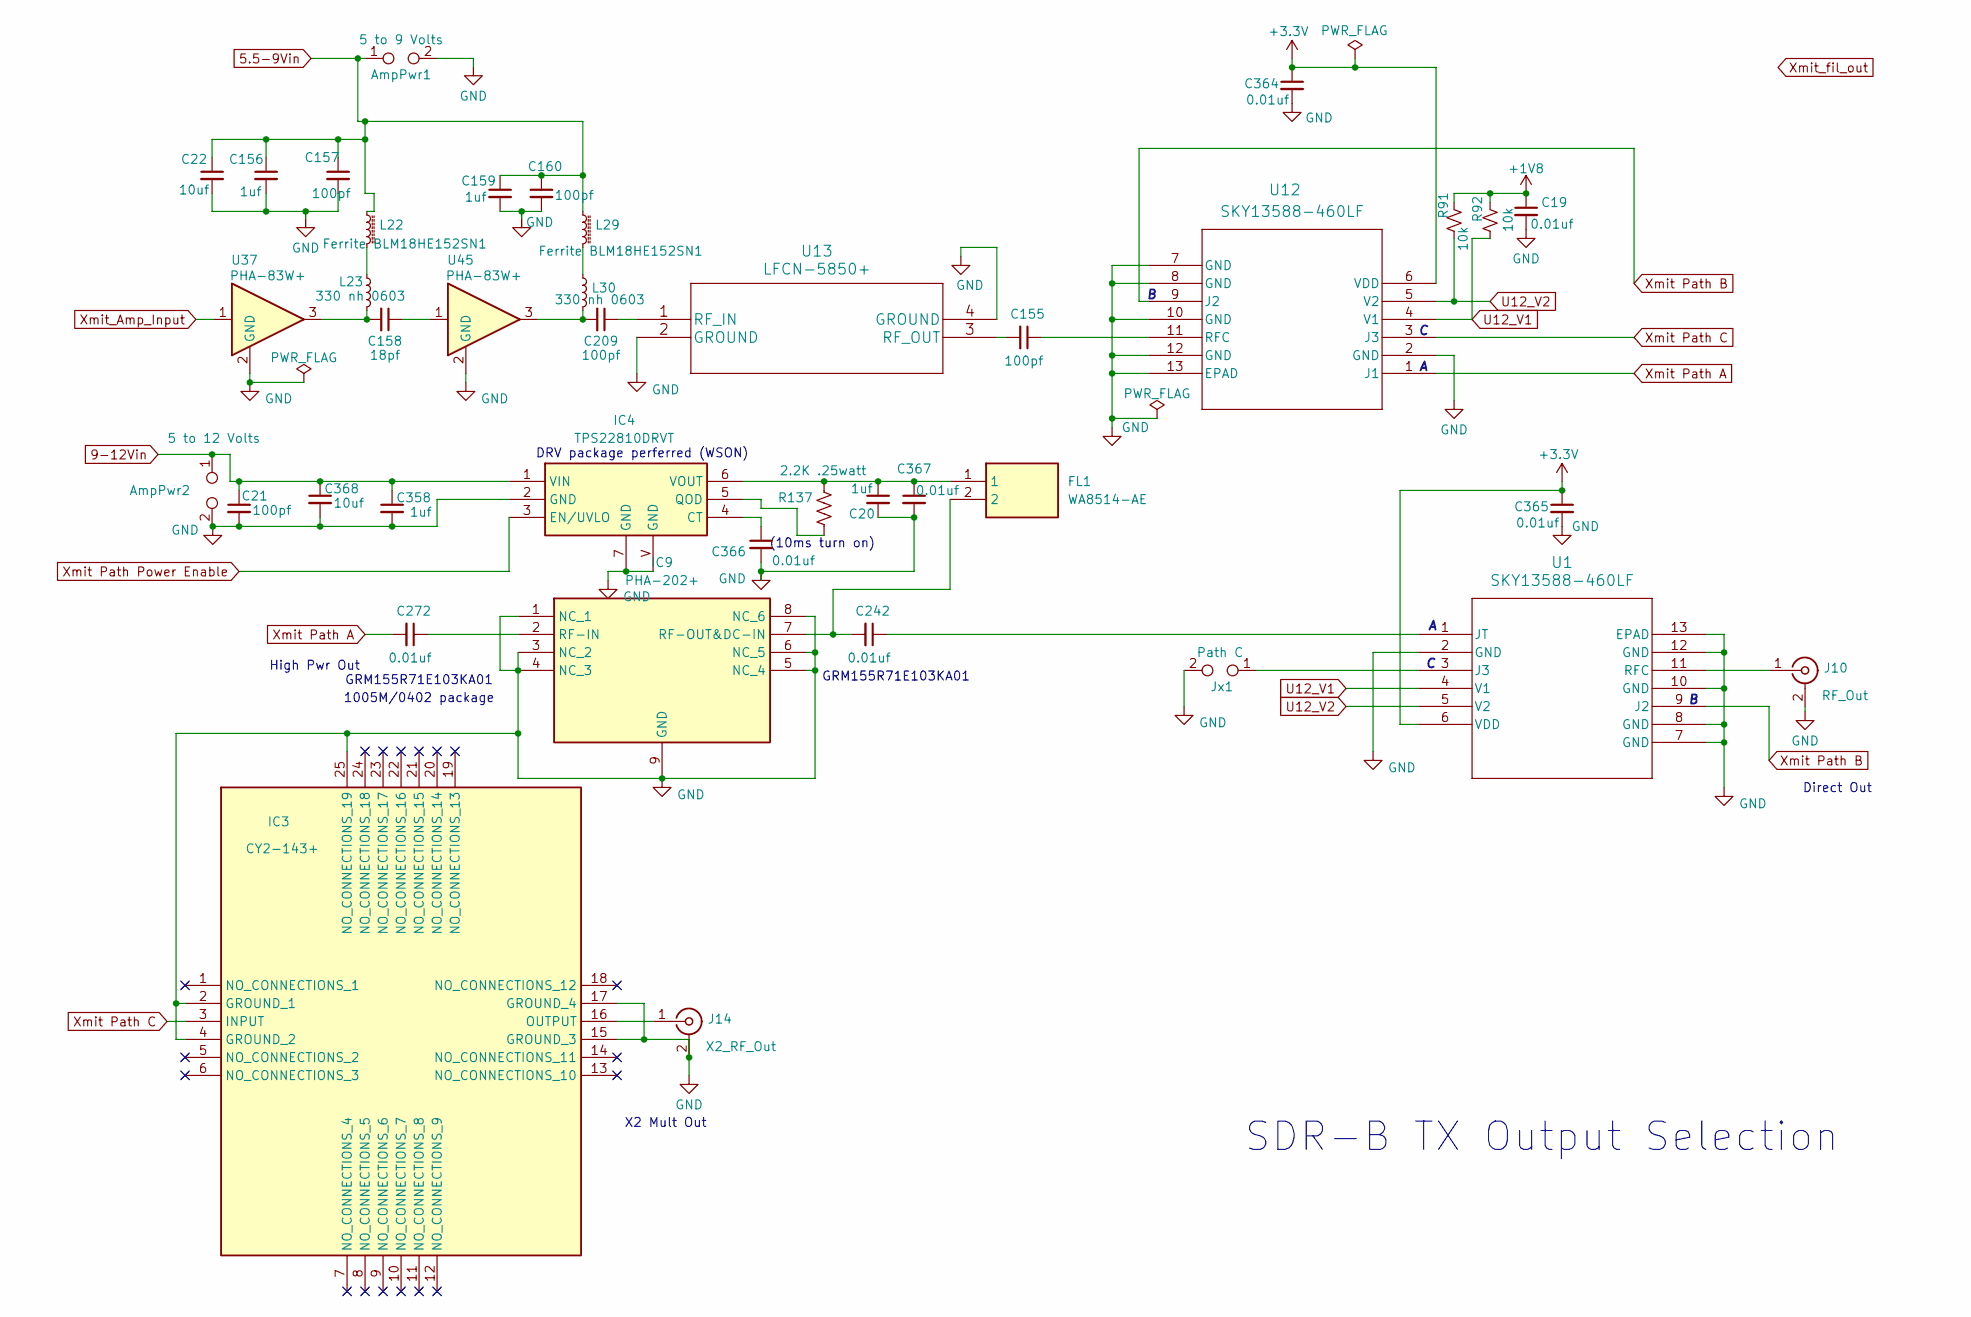
[picture p15: schematic Transmit Amplifier.kicad_sch]

Parts:
AmpPwr1: 5 to 9 Volts; TestPoint_2Pads_Pitch2.54mm_Drill0.8mm
AmpPwr2: 5 to 12 Volts; TestPoint_2Pads_Pitch2.54mm_Drill0.8mm
C19, C364, C365, C366, C367: 0.01uf; C_0201_0603Metric
C20, C156, C159, C358: 1uf; C_0402_1005Metric
C21, C157, C160, C209: 100pf; C_0201_0603Metric
C22, C368: 10uf; C_0805_2012Metric
C155: 100pf; C_0402_1005Metric
C158: 18pf; C_0201_0603Metric
C242, C272: 0.01uf; C_0402_1005Metric
FL1: WA8514-AE; WA8514AE; Manufacturer_Part_Number WA8514-AE
IC3: CY2-143+; QFN50P400X400X100-25N; Mouser Part Number 139-CY2-143+
IC4: TPS22810DRVT; DRV0006A; Manufacturer_Part_Number TPS22810TDBVRQ1; Mouser Part Number 595-TPS22810TDBVRQ1
IC9: PHA-202+; SON127P600X490X100-9N-D; Manufacturer_Part_Number PHA-202+; Mouser Part Number 139-PHA-202
J10: RF_Out; MMCX_Molex_73415-1471_Vertical
J14: X2_RF_Out; MMCX_Molex_73415-1471_Vertical
Jx1: Path C; TestPoint_2Pads_Pitch2.54mm_Drill0.8mm
L22, L29: Ferrite BLM18HE152SN1; IND_BLM18_0603_MUR
L23, L30: 330 nh 0603; LQM18PH1R0MFRL
R91, R92: 10k; R_0201_0603Metric
R137: 2.2K .25watt; R_1206_3216Metric
U1: SKY13588-460LF; QFN12_SKY
U12: SKY13588-460LF; QFN12_SKY-L
U13: LFCN-5850+; Filter_Mini-Circuits_FV1206
U37, U45: PHA-83W+; SOT-89-3

Connections:
5.5-9Vin: AmpPwr1.1, C22.1, C156.1, C157.1, C159.1, C160.1, L22.1, L29.1
9-12Vin: AmpPwr2.1, C21.1, C358.1, C368.1, IC4.1 (VIN)
+1V8: C19.1, R91.2, R92.2
+3.3V: C364.1, C365.1, U1.6 (VDD), U12.6 (VDD)
GND: AmpPwr1.2, AmpPwr2.2, C19.2, C20.2, C21.2, C22.2, C156.2, C157.2, C159.2, C160.2, C358.2, C364.2, C365.2, C366.2, C367.2, C368.2, IC3.2 (GROUND_1), IC3.4 (GROUND_2), IC3.15 (GROUND_3), IC3.17 (GROUND_4), IC3.25 (NO_CONNECTIONS_19), IC4.2 (GND), IC4.7 (GND), IC4.V (GND), IC9.1 (NC_1), IC9.3 (NC_2), IC9.4 (NC_3), IC9.5 (NC_4), IC9.6 (NC_5), IC9.8 (NC_6), IC9.9 (GND), J10.2 (Ext), J14.2 (Ext), Jx1.2, U1.2 (GND), U1.7 (GND), U1.8 (GND), U1.10 (GND), U1.12 (GND), U1.13 (EPAD), U12.2 (GND), U12.7 (GND), U12.8 (GND), U12.10 (GND), U12.12 (GND), U12.13 (EPAD), U13.2 (GROUND), U13.4 (GROUND), U37.2 (GND), U45.2 (GND)
unnamed: C20.1, C367.1, FL1.1, IC4.6 (VOUT), R137.1
unnamed: C155.1, U12.11 (RFC)
unnamed: C155.2, U13.3 (RF_OUT)
unnamed: C158.1, U45.1
unnamed: C158.2, L23.2, U37.3
unnamed: C209.1, U13.1 (RF_IN)
unnamed: C209.2, L30.2, U45.3
unnamed: C242.1, U1.1 (JT)
unnamed: C242.2, FL1.2, IC9.7 (RF-OUT&DC-IN)
unnamed: C272.1, IC9.2 (RF-IN)
unnamed: C366.1, IC4.4 (CT)
unnamed: IC3.16 (OUTPUT), J14.1 (In)
unnamed: IC4.5 (QOD), R137.2
unnamed: J10.1 (In), U1.11 (RFC)
unnamed: Jx1.1, U1.3 (J3)
unnamed: L22.2, L23.1
unnamed: L29.2, L30.1
U12_V1: R92.1, U1.4 (V1), U12.4 (V1)
U12_V2: R91.1, U1.5 (V2), U12.5 (V2)
Xmit Path A: C272.2, U12.1 (J1)
Xmit Path B: U1.9 (J2), U12.9 (J2)
Xmit Path C: IC3.3 (INPUT), U12.3 (J3)
Xmit Path Power Enable: IC4.3 (EN/UVLO)
Xmit_Amp_Input: U37.1

Notes on the sheet:
DRV package perferred (WSON)
X2 Mult Out
GRM155R71E103KA01
High Pwr Out
SDR-B TX Output Selection
Direct Out
(10ms turn on)
1005M/0402 package
