WA1CYB/SDR_Gen2/Zynq-XC7Z020-sheet-1-page 9.kicad_sch

## KiCad design Zynq-XC7Z020-sheet-1-page 9.kicad_sch (2026-04-03)

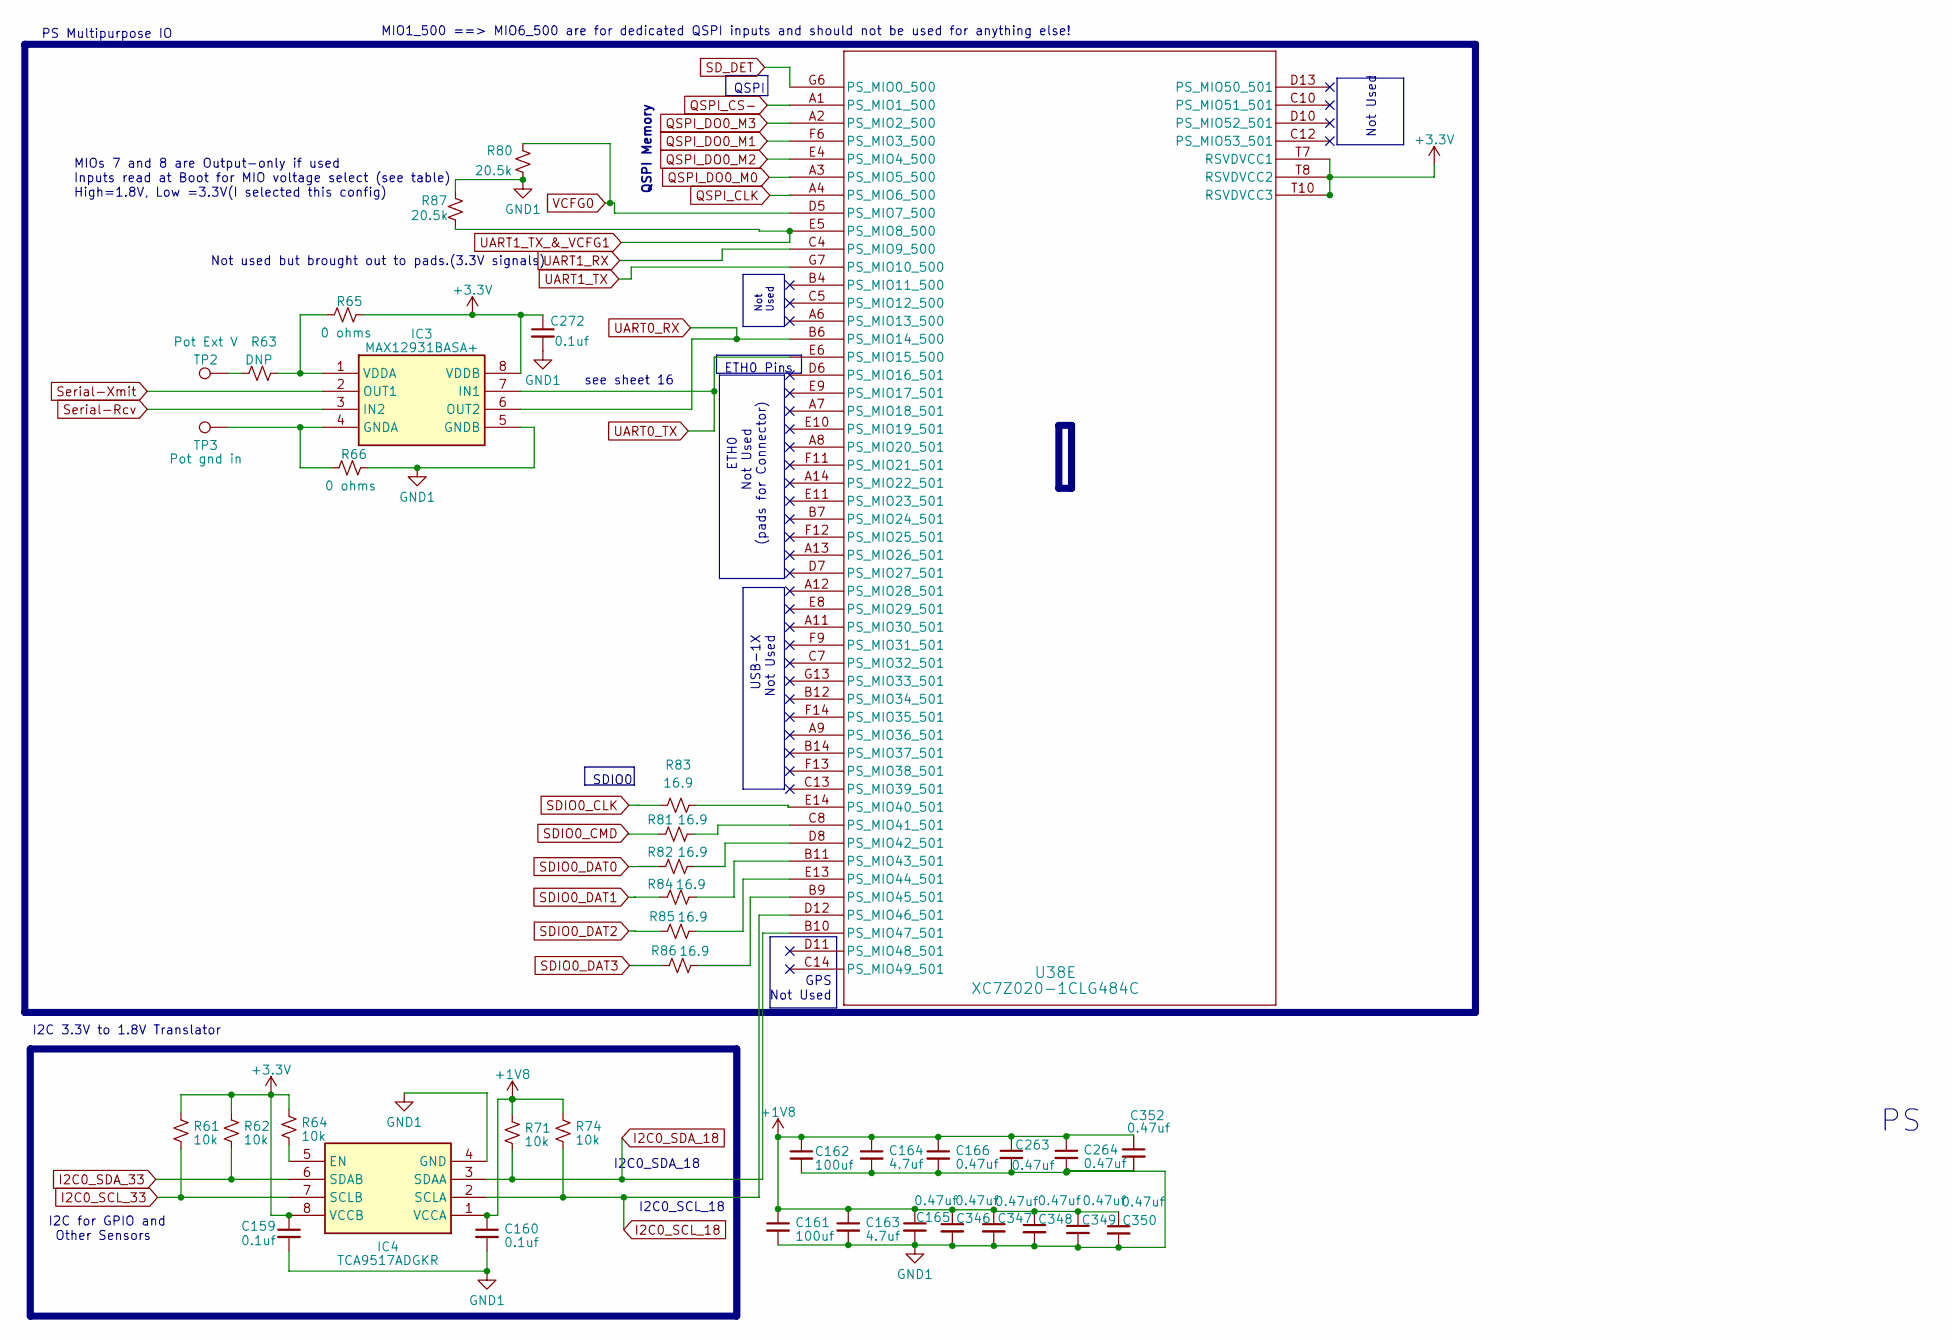
[picture p16: schematic Zynq-XC7Z020-sheet-1-page 9.kicad_sch]

Parts:
C159, C160, C272: 0.1uf; C_0201_0603Metric
C161, C162: 100uf; C_1206_3216Metric
C163, C164: 4.7uf; C_0402_1005Metric
C165, C166: 0.47uf; C_0402_1005Metric
C263, C264, C346, C347, C348, C349, C350, C352: 0.47uf; C_0201_0603Metric
IC3: MAX12931BASA+; SOIC127P600X175-8N; Manufacturer_Part_Number MAX12931BASA+; Mouser Part Number 700-MAX12931BASA+
IC4: TCA9517ADGKR; SOP65P490X110-8N; Manufacturer_Part_Number TCA9517ADGKR; Mouser Part Number 595-TCA9517ADGKR
R61, R62, R64, R71, R74: 10k; R_0201_0603Metric
R63: DNP; R_0201_0603Metric
R65, R66: 0 ohms; R_0201_0603Metric
R80, R87: 20.5k; R_0201_0603Metric
R81, R82, R83, R84, R85, R86: 16.9; R_0201_0603Metric
TP2: Pot Ext V; TestPoint_Loop_D2.50mm_Drill1.0mm
TP3: Pot gnd in; TestPoint_Loop_D2.50mm_Drill1.0mm
U38: XC7Z020-1CLG484C; Xilinx_CLG484_CLG485

Connections:
+1V8: C160.1, C161.1, C162.1, C163.1, C164.1, C165.1, C166.1, C263.1, C264.1, C346.1, C347.1, C348.1, C349.1, C350.1, C352.1, IC4.1 (VCCA), R71.1, R74.1
+3.3V: C159.1, C272.1, IC3.8 (VDDB), IC4.8 (VCCB), R61.1, R62.1, R64.1, R65.2, U38.T7 (RSVDVCC1), U38.T8 (RSVDVCC2), U38.T10 (RSVDVCC3)
GND1: C159.2, C160.2, C161.2, C162.2, C163.2, C164.2, C165.2, C166.2, C263.2, C264.2, C272.2, C346.2, C347.2, C348.2, C349.2, C350.2, C352.2, IC3.5 (GNDB), IC4.4 (GND), R66.2, R80.1, R87.2
I2C0_SCL_18: IC4.2 (SCLA), R74.2, U38.D12 (PS_MIO46_501)
I2C0_SCL_33: IC4.7 (SCLB), R61.2
I2C0_SDA_18: IC4.3 (SDAA), R71.2, U38.B10 (PS_MIO47_501)
I2C0_SDA_33: IC4.6 (SDAB), R62.2
unnamed: IC3.1 (VDDA), R63.2, R65.1
unnamed: IC3.4 (GNDA), R66.1, TP3.1
unnamed: IC4.5 (EN), R64.2
unnamed: R63.1, TP2.1
unnamed: R81.1, U38.C8 (PS_MIO41_501)
unnamed: R82.1, U38.D8 (PS_MIO42_501)
unnamed: R83.1, U38.E14 (PS_MIO40_501)
unnamed: R84.1, U38.B11 (PS_MIO43_501)
unnamed: R85.1, U38.E13 (PS_MIO44_501)
unnamed: R86.1, U38.B9 (PS_MIO45_501)
QSPI_CLK: U38.A4 (PS_MIO6_500)
QSPI_CS-: U38.A1 (PS_MIO1_500)
QSPI_DO0_M0: U38.A3 (PS_MIO5_500)
QSPI_DO0_M1: U38.F6 (PS_MIO3_500)
QSPI_DO0_M2: U38.E4 (PS_MIO4_500)
QSPI_DO0_M3: U38.A2 (PS_MIO2_500)
SDIO0_CLK: R83.2
SDIO0_CMD: R81.2
SDIO0_DAT0: R82.2
SDIO0_DAT1: R84.2
SDIO0_DAT2: R85.2
SDIO0_DAT3: R86.2
SD_DET: U38.G6 (PS_MIO0_500)
Serial-Rcv: IC3.3 (IN2)
Serial-Xmit: IC3.2 (OUT1)
UART0_RX: IC3.6 (OUT2), U38.B6 (PS_MIO14_500)
UART0_TX: IC3.7 (IN1), U38.E6 (PS_MIO15_500)
UART1_RX: U38.C4 (PS_MIO9_500)
UART1_TX: U38.G7 (PS_MIO10_500)
UART1_TX_&_VCFG1: R87.1, U38.E5 (PS_MIO8_500)
VCFG0: R80.2, U38.D5 (PS_MIO7_500)

Notes on the sheet:
ETH0 Pins
QSPI
SDIO0
see sheet 16
Not Used
MIO1_500 ==> MIO6_500 are for dedicated QSPI inputs and should not be used for anything else!
QSPI Memory
ETH0 Not Used (pads for Connector)
USB-1X Not Used
Not Used
MIOs 7 and 8 are Output-only if used Inputs read at Boot for MIO voltage select (see table) High=1.8V, Low =3.3V(I selected this config)
I2C0_SDA_18
Not used but brought out to pads.(3.3V signals)
I2C 3.3V to 1.8V Translator
PS Multipurpose IO
I2C for GPIO and Other Sensors
GPS Not Used
I2C0_SCL_18
