WA1CYB/SDR_Gen2/Zynq-XC7Z020-sheet-1-page 10.kicad_sch

## KiCad design Zynq-XC7Z020-sheet-1-page 10.kicad_sch (2026-04-03)

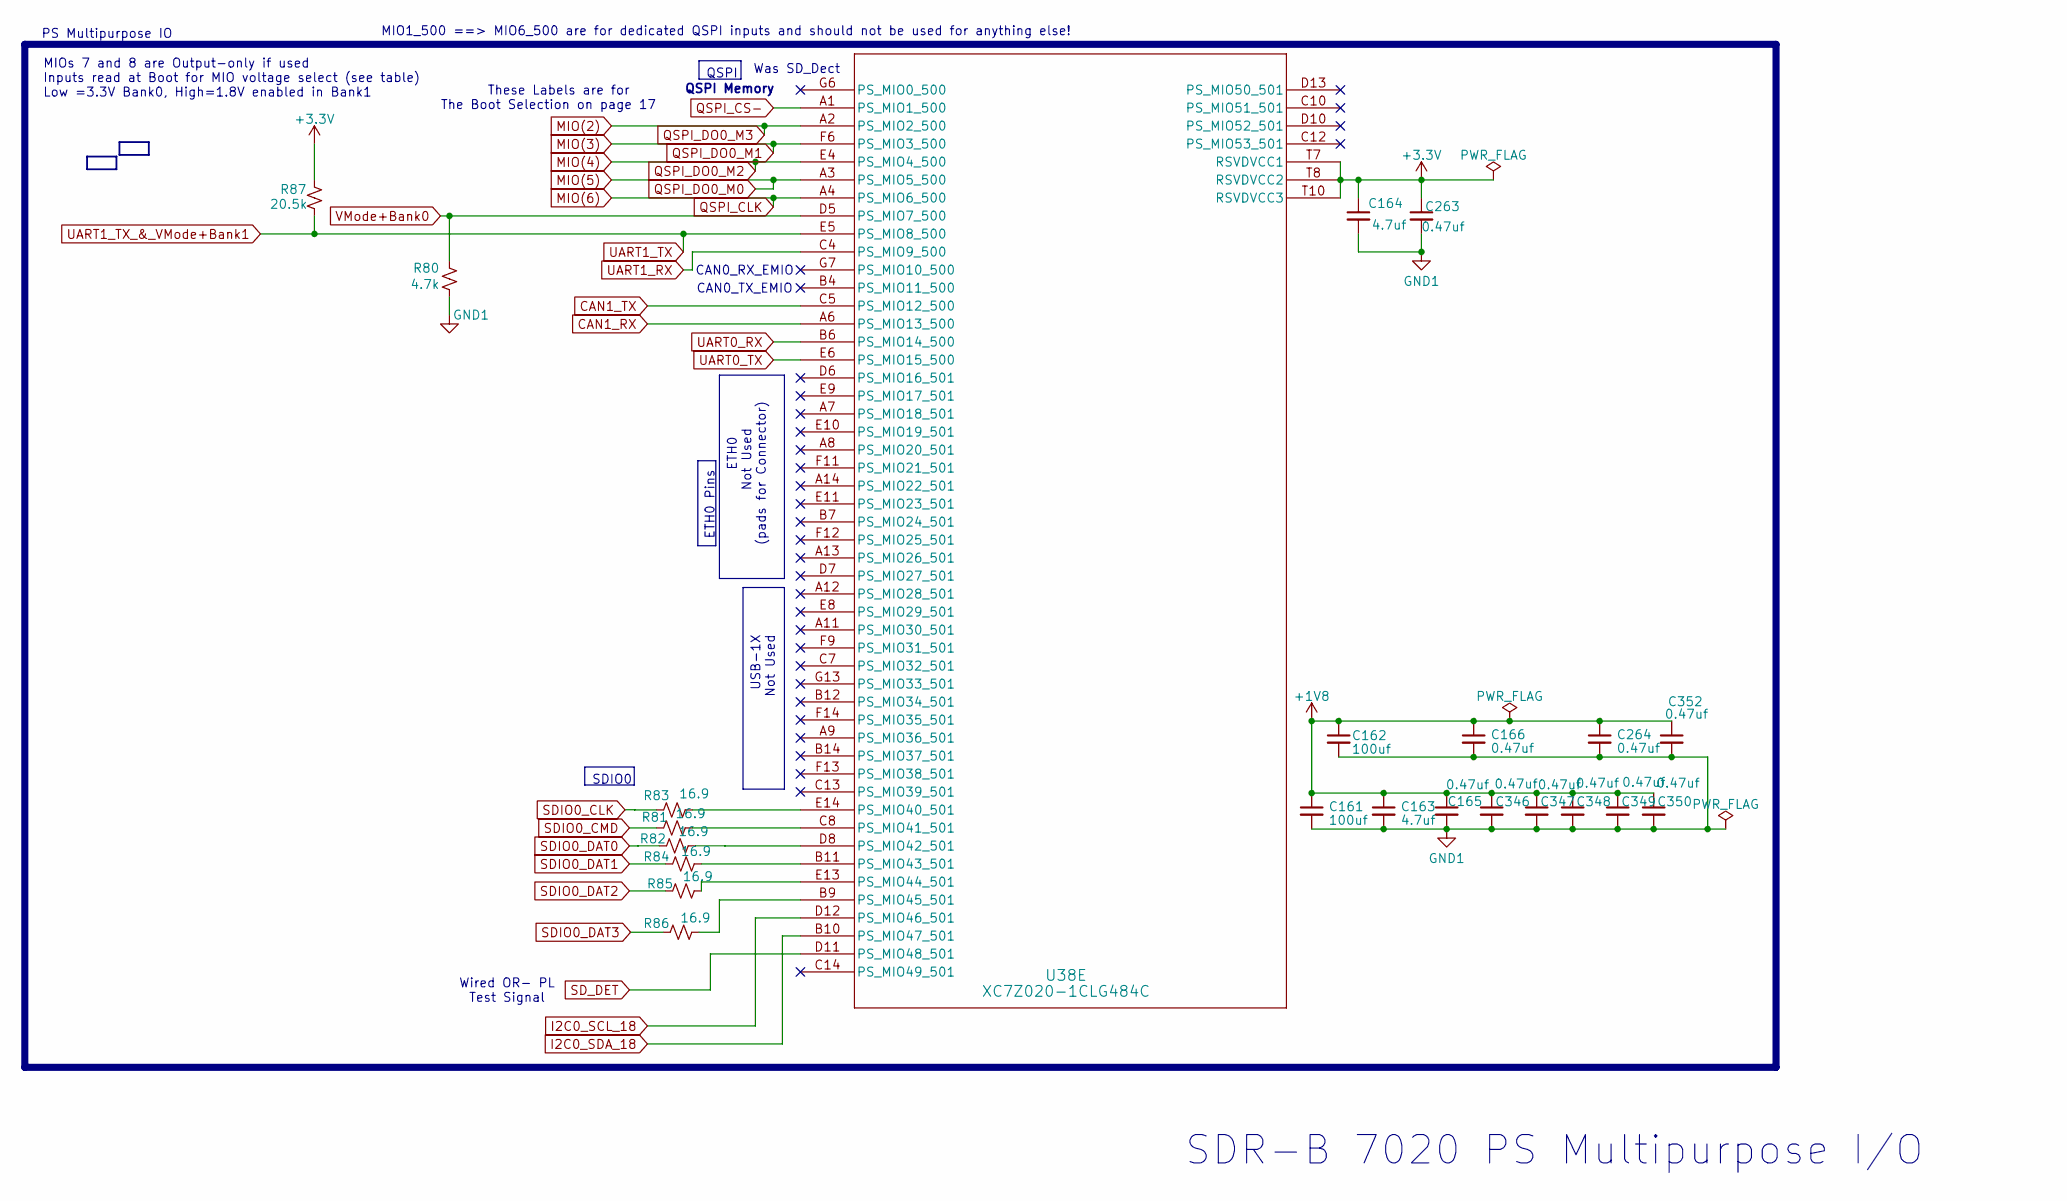
[picture p17: schematic Zynq-XC7Z020-sheet-1-page 10.kicad_sch]

Parts:
C161, C162: 100uf; C_1206_3216Metric
C163, C164: 4.7uf; C_0402_1005Metric
C165, C166: 0.47uf; C_0402_1005Metric
C263, C264, C346, C347, C348, C349, C350, C352: 0.47uf; C_0201_0603Metric
R80: 4.7k; R_0201_0603Metric
R81, R82, R83, R84, R85, R86: 16.9; R_0201_0603Metric
R87: 20.5k; R_0201_0603Metric
U38: XC7Z020-1CLG484C; Xilinx_CLG484_CLG485

Connections:
+1V8: C161.1, C162.1, C163.1, C165.1, C166.1, C264.1, C346.1, C347.1, C348.1, C349.1, C350.1, C352.1
+3.3V: C164.1, C263.1, R87.2, U38.T7 (RSVDVCC1), U38.T8 (RSVDVCC2), U38.T10 (RSVDVCC3)
CAN1_RX: U38.A6 (PS_MIO13_500)
CAN1_TX: U38.C5 (PS_MIO12_500)
GND1: C161.2, C162.2, C163.2, C164.2, C165.2, C166.2, C263.2, C264.2, C346.2, C347.2, C348.2, C349.2, C350.2, C352.2, R80.1
I2C0_SCL_18: U38.D12 (PS_MIO46_501)
I2C0_SDA_18: U38.B10 (PS_MIO47_501)
MIO(2): U38.A2 (PS_MIO2_500)
MIO(3): U38.F6 (PS_MIO3_500)
MIO(4): U38.E4 (PS_MIO4_500)
MIO(5): U38.A3 (PS_MIO5_500)
MIO(6): U38.A4 (PS_MIO6_500)
unnamed: R81.1, U38.C8 (PS_MIO41_501)
unnamed: R82.1, U38.D8 (PS_MIO42_501)
unnamed: R83.1, U38.E14 (PS_MIO40_501)
unnamed: R84.1, U38.B11 (PS_MIO43_501)
unnamed: R85.1, U38.E13 (PS_MIO44_501)
unnamed: R86.1, U38.B9 (PS_MIO45_501)
QSPI_CS-: U38.A1 (PS_MIO1_500)
SDIO0_CLK: R83.2
SDIO0_CMD: R81.2
SDIO0_DAT0: R82.2
SDIO0_DAT1: R84.2
SDIO0_DAT2: R85.2
SDIO0_DAT3: R86.2
SD_DET: U38.D11 (PS_MIO48_501)
UART0_RX: U38.B6 (PS_MIO14_500)
UART0_TX: U38.E6 (PS_MIO15_500)
UART1_RX: U38.C4 (PS_MIO9_500)
UART1_TX: R87.1, U38.E5 (PS_MIO8_500)
VMode+Bank0: R80.2, U38.D5 (PS_MIO7_500)

Notes on the sheet:
Was SD_Dect
SDR-B 7020 PS Multipurpose I/O
MIO1_500 ==> MIO6_500 are for dedicated QSPI inputs and should not be used for anything else!
Wired OR- PL Test Signal
QSPI Memory
ETH0 Not Used (pads for Connector)
USB-1X Not Used
MIOs 7 and 8 are Output-only if used Inputs read at Boot for MIO voltage select (see table) Low =3.3V Bank0, High=1.8V enabled in Bank1
These Labels are for The Boot Selection on page 17
CAN0_TX_EMIO
PS Multipurpose IO
CAN0_RX_EMIO
ETH0 Pins
QSPI
SDIO0
