WA1CYB/SDR_Gen2/Zynq-XC7Z020-sheet-2-page10.kicad_sch

## KiCad design Zynq-XC7Z020-sheet-2-page10.kicad_sch (2026-04-03)

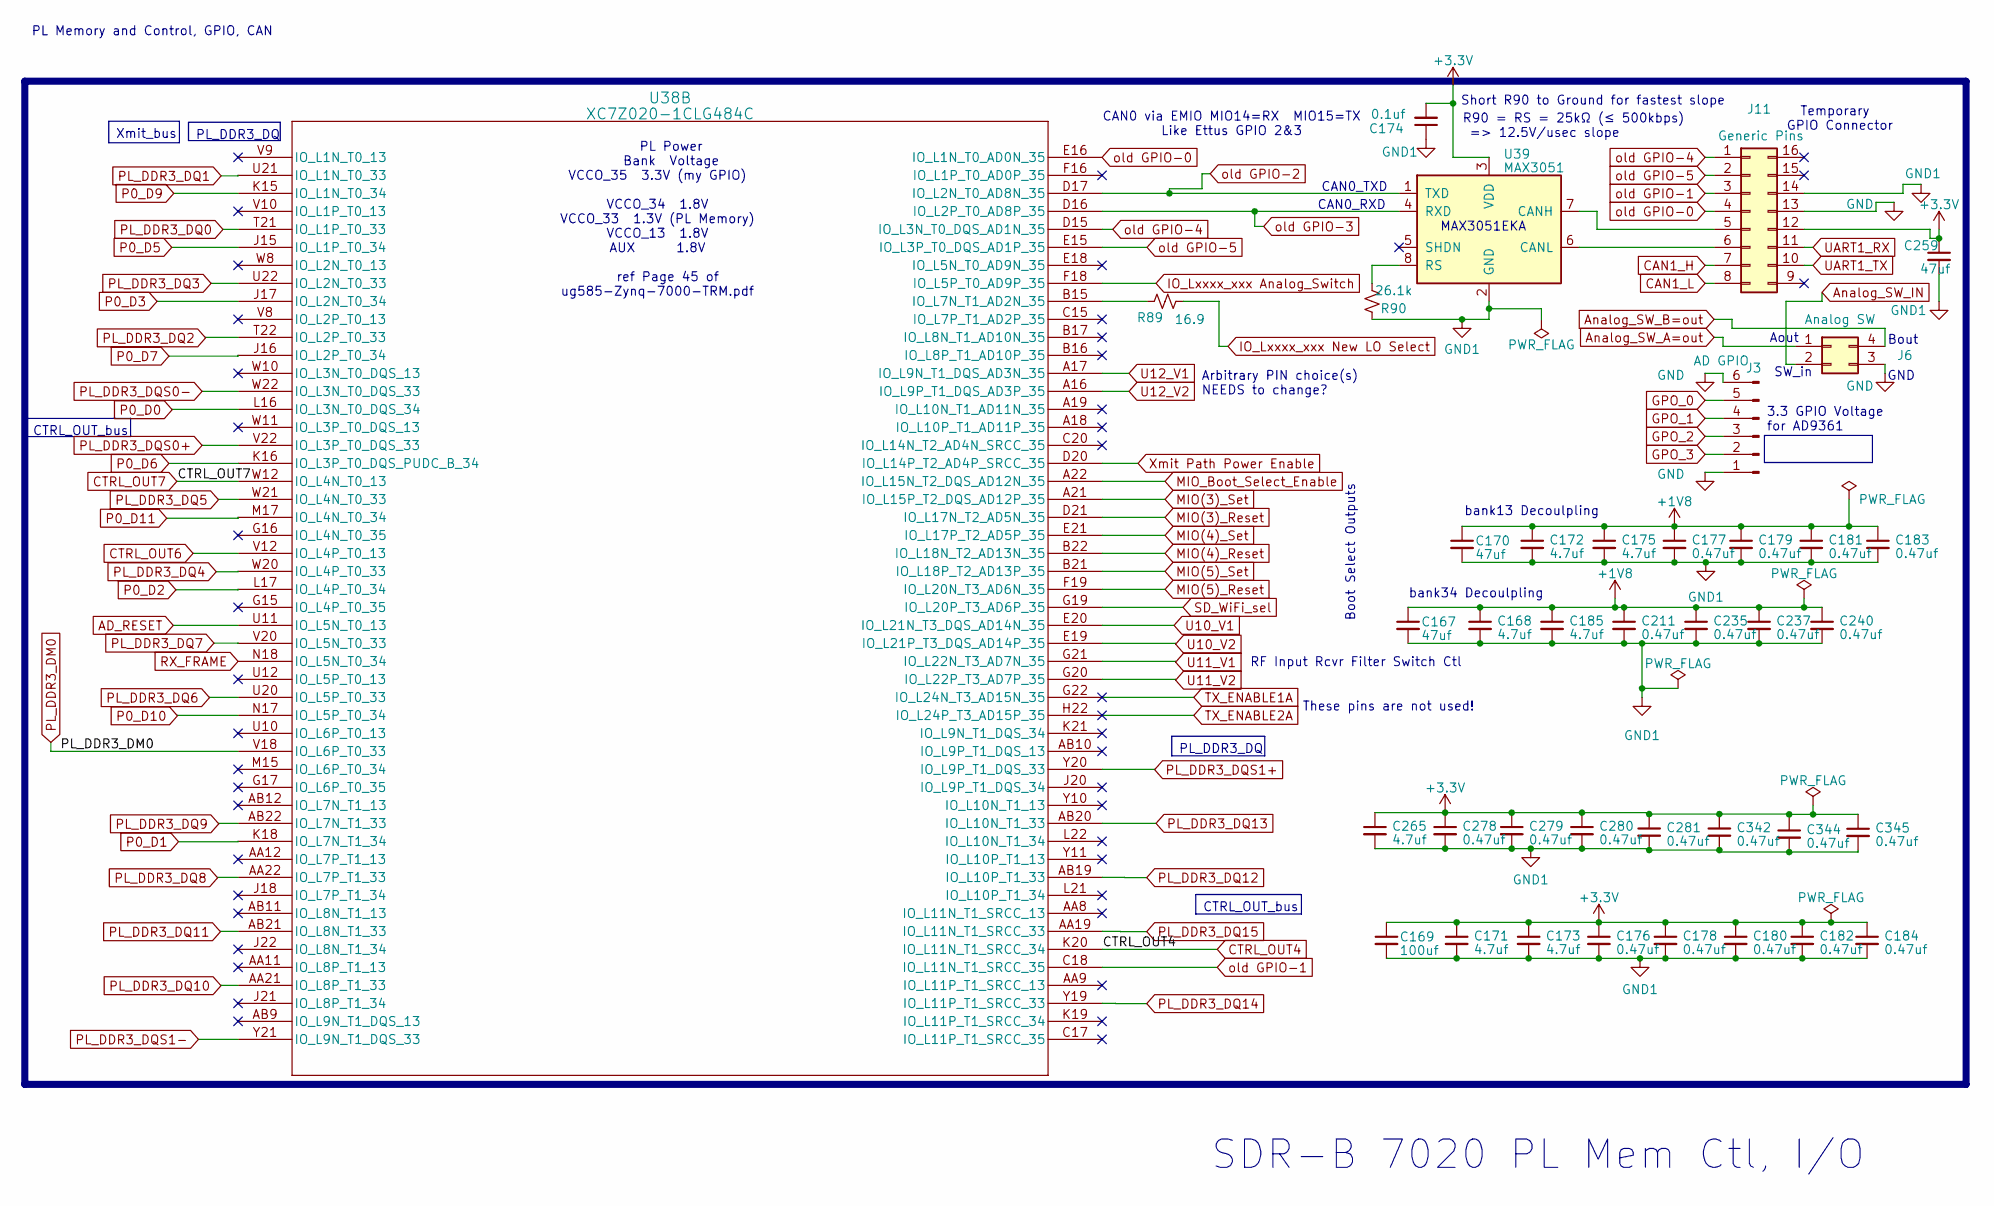
[picture p18: schematic Zynq-XC7Z020-sheet-2-page10.kicad_sch]

Parts:
C167, C170, C259: 47uf; C_1206_3216Metric
C168, C171, C172, C173, C175, C185, C265: 4.7uf; C_0402_1005Metric
C169: 100uf; C_1206_3216Metric
C174: 0.1uf; C_0201_0603Metric
C176, C177, C178, C179, C180, C181, C182, C183, C184, C211, C235, C237, C240, C278, C279, C280, C281, C342, C344, C345: 0.47uf; C_0201_0603Metric
J3: AD GPIO; PinSocket_1x06_P1.27mm_Vertical
J6: Analog SW; PinSocket_2x02_P1.27mm_Vertical
J11: Generic Pins; Hirose_DF11-16DP-2DSA_2x08_P2.00mm_Vertical
R89: 16.9; R_0201_0603Metric
R90: 26.1k; R_0603_1608Metric
U38: XC7Z020-1CLG484C; Xilinx_CLG484_CLG485
U39: MAX3051; MAX3051EKA

Connections:
+1V8: C167.1, C168.1, C170.1, C172.1, C175.1, C177.1, C179.1, C181.1, C183.1, C185.1, C211.1, C235.1, C237.1, C240.1
+3.3V: C169.1, C171.1, C173.1, C174.2, C176.1, C178.1, C180.1, C182.1, C184.1, C259.1, C265.1, C278.1, C279.1, C280.1, C281.1, C342.1, C344.1, C345.1, J11.12, U39.3 (VDD)
AD_RESET: U38.U11 (IO_L5N_T0_13)
Analog_SW_A=out: J6.1
Analog_SW_B=out: J6.4
Analog_SW_IN: J6.2
CAN1_H: J11.7
CAN1_L: J11.8
CTRL_OUT4: U38.K20 (IO_L11N_T1_SRCC_34)
CTRL_OUT6: U38.V12 (IO_L4P_T0_13)
CTRL_OUT7: U38.W12 (IO_L4N_T0_13)
GND: J3.1, J3.6, J6.3, J11.13
GND1: C167.2, C168.2, C169.2, C170.2, C171.2, C172.2, C173.2, C174.1, C175.2, C176.2, C177.2, C178.2, C179.2, C180.2, C181.2, C182.2, C183.2, C184.2, C185.2, C211.2, C235.2, C237.2, C240.2, C259.2, C265.2, C278.2, C279.2, C280.2, C281.2, C342.2, C344.2, C345.2, J11.14, R90.2, U39.2 (GND)
GPO_0: J3.5
GPO_1: J3.4
GPO_2: J3.3
GPO_3: J3.2
IO_Lxxxx_xxx Analog_Switch: U38.F18 (IO_L5P_T0_AD9P_35)
IO_Lxxxx_xxx New LO Select: R89.2
MIO(3)_Reset: U38.D21 (IO_L17N_T2_AD5N_35)
MIO(3)_Set: U38.A21 (IO_L15P_T2_DQS_AD12P_35)
MIO(4)_Reset: U38.B22 (IO_L18N_T2_AD13N_35)
MIO(4)_Set: U38.E21 (IO_L17P_T2_AD5P_35)
MIO(5)_Reset: U38.F19 (IO_L20N_T3_AD6N_35)
MIO(5)_Set: U38.B21 (IO_L18P_T2_AD13P_35)
MIO_Boot_Select_Enable: U38.A22 (IO_L15N_T2_DQS_AD12N_35)
unnamed: J11.5, U39.7 (CANH)
unnamed: J11.6, U39.6 (CANL)
unnamed: R89.1, U38.B15 (IO_L7N_T1_AD2N_35)
unnamed: R90.1, U39.8 (RS)
P0_D0: U38.L16 (IO_L3N_T0_DQS_34)
P0_D1: U38.K18 (IO_L7N_T1_34)
P0_D2: U38.L17 (IO_L4P_T0_34)
P0_D3: U38.J17 (IO_L2N_T0_34)
P0_D5: U38.J15 (IO_L1P_T0_34)
P0_D6: U38.K16 (IO_L3P_T0_DQS_PUDC_B_34)
P0_D7: U38.J16 (IO_L2P_T0_34)
P0_D9: U38.K15 (IO_L1N_T0_34)
P0_D10: U38.N17 (IO_L5P_T0_34)
P0_D11: U38.M17 (IO_L4N_T0_34)
PL_DDR3_DM0: U38.V18 (IO_L6P_T0_33)
PL_DDR3_DQ0: U38.T21 (IO_L1P_T0_33)
PL_DDR3_DQ1: U38.U21 (IO_L1N_T0_33)
PL_DDR3_DQ2: U38.T22 (IO_L2P_T0_33)
PL_DDR3_DQ3: U38.U22 (IO_L2N_T0_33)
PL_DDR3_DQ4: U38.W20 (IO_L4P_T0_33)
PL_DDR3_DQ5: U38.W21 (IO_L4N_T0_33)
PL_DDR3_DQ6: U38.U20 (IO_L5P_T0_33)
PL_DDR3_DQ7: U38.V20 (IO_L5N_T0_33)
PL_DDR3_DQ8: U38.AA22 (IO_L7P_T1_33)
PL_DDR3_DQ9: U38.AB22 (IO_L7N_T1_33)
PL_DDR3_DQ10: U38.AA21 (IO_L8P_T1_33)
PL_DDR3_DQ11: U38.AB21 (IO_L8N_T1_33)
PL_DDR3_DQ12: U38.AB19 (IO_L10P_T1_33)
PL_DDR3_DQ13: U38.AB20 (IO_L10N_T1_33)
PL_DDR3_DQ14: U38.Y19 (IO_L11P_T1_SRCC_33)
PL_DDR3_DQ15: U38.AA19 (IO_L11N_T1_SRCC_33)
PL_DDR3_DQS0+: U38.V22 (IO_L3P_T0_DQS_33)
PL_DDR3_DQS0-: U38.W22 (IO_L3N_T0_DQS_33)
PL_DDR3_DQS1+: U38.Y20 (IO_L9P_T1_DQS_33)
PL_DDR3_DQS1-: U38.Y21 (IO_L9N_T1_DQS_33)
RX_FRAME: U38.N18 (IO_L5N_T0_34)
SD_WiFi_sel: U38.G19 (IO_L20P_T3_AD6P_35)
TX_ENABLE1A: U38.G22 (IO_L24N_T3_AD15N_35)
TX_ENABLE2A: U38.H22 (IO_L24P_T3_AD15P_35)
U10_V1: U38.E20 (IO_L21N_T3_DQS_AD14N_35)
U10_V2: U38.E19 (IO_L21P_T3_DQS_AD14P_35)
U11_V1: U38.G21 (IO_L22N_T3_AD7N_35)
U11_V2: U38.G20 (IO_L22P_T3_AD7P_35)
U12_V1: U38.A17 (IO_L9N_T1_DQS_AD3N_35)
U12_V2: U38.A16 (IO_L9P_T1_DQS_AD3P_35)
UART1_RX: J11.11
UART1_TX: J11.10
Xmit Path Power Enable: U38.D20 (IO_L14P_T2_AD4P_SRCC_35)
old GPIO-0: J11.4, U38.E16 (IO_L1N_T0_AD0N_35)
old GPIO-1: J11.3, U38.C18 (IO_L11N_T1_SRCC_35)
old GPIO-2: U38.D17 (IO_L2N_T0_AD8N_35), U39.1 (TXD)
old GPIO-3: U38.D16 (IO_L2P_T0_AD8P_35), U39.4 (RXD)
old GPIO-4: J11.1, U38.D15 (IO_L3N_T0_DQS_AD1N_35)
old GPIO-5: J11.2, U38.E15 (IO_L3P_T0_DQS_AD1P_35)

Notes on the sheet:
MAX3051EKA
CAN0_RXD
SDR-B 7020 PL Mem Ctl, I/O
Boot Select Outputs
CAN0_TXD
GND
3.3 GPIO Voltage for AD9361
Bout
PL Memory and Control, GPIO, CAN
bank13 Decoulpling
R90 = RS = 25kΩ (≤ 500kbps) => 12.5V/usec slope
These pins are not used!
RF Input Rcvr Filter Switch Ctl
SW_in
bank34 Decoulpling
Arbitrary PIN choice(s) NEEDS to change?
PL Power Bank Voltage VCCO_35 3.3V (my GPIO) VCCO_34 1.8V VCCO_33 1.3V (PL Memory) VCCO_13 1.8V AUX 1.8V ref Page 45 of ug585-Zynq-7000-TRM.pdf
CAN0 via EMIO MIO14=RX MIO15=TX Like Ettus GPIO 2&3
Aout
Temporary GPIO Connector
Short R90 to Ground for fastest slope
PL_DDR3_DQ
CTRL_OUT_bus
Xmit_bus
