WA1CYB/SDR_Gen2/Zynq-XC7Z020-sheet-3-page11.kicad_sch

## KiCad design Zynq-XC7Z020-sheet-3-page11.kicad_sch (2026-04-03)

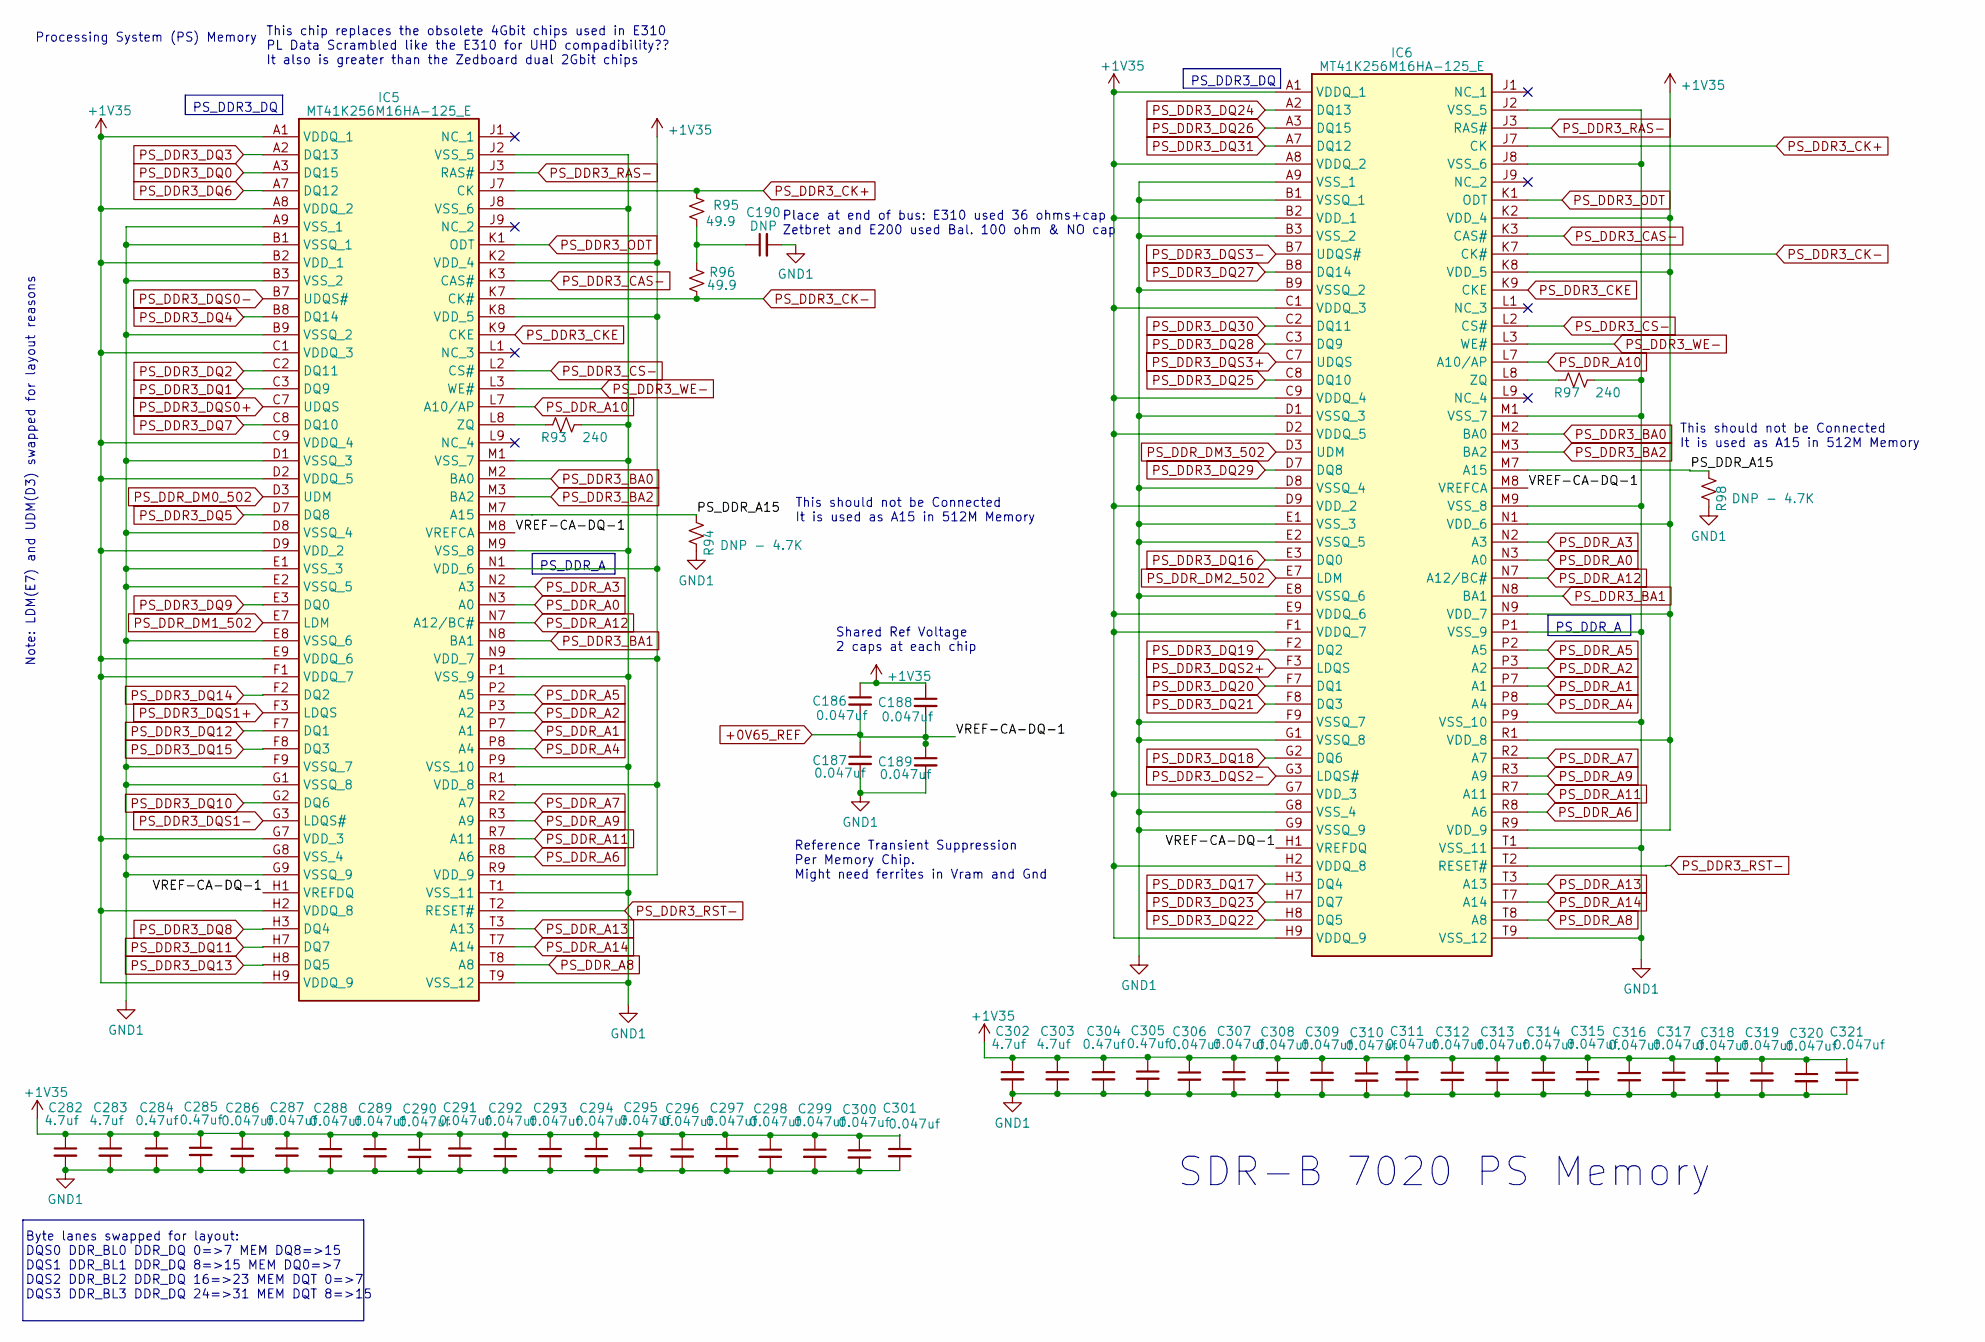
[picture p19: schematic Zynq-XC7Z020-sheet-3-page11.kicad_sch]

Parts:
C186, C187, C188, C189, C286, C287, C288, C289, C290, C291, C292, C293, C294, C295, C296, C297, C298, C299, C300, C301, C306, C307, C308, C309, C310, C311, C312, C313, C314, C315, C316, C317, C318, C319, C320, C321: 0.047uf; C_0201_0603Metric
C190: DNP; C_0201_0603Metric
C282, C283, C302, C303: 4.7uf; C_0402_1005Metric
C284, C285, C304, C305: 0.47uf; C_0201_0603Metric
IC5, IC6: MT41K256M16HA-125_E; BGA96C80P9X16_900X1400X120; Manufacturer_Part_Number MT41K512M16HA-125:A; Mouser Part Number 340-286628-TRAY
R93, R97: 240; R_0201_0603Metric
R94, R98: DNP - 4.7K; R_0201_0603Metric
R95, R96: 49.9; R_0201_0603Metric

Connections:
+0V65_REF: C186.2, C187.1, C188.2, C189.1, IC5.H1 (VREFDQ), IC5.M8 (VREFCA), IC6.H1 (VREFDQ), IC6.M8 (VREFCA)
+1V35: C186.1, C188.1, C282.1, C283.1, C284.1, C285.1, C286.1, C287.1, C288.1, C289.1, C290.1, C291.1, C292.1, C293.1, C294.1, C295.1, C296.1, C297.1, C298.1, C299.1, C300.1, C301.1, C302.1, C303.1, C304.1, C305.1, C306.1, C307.1, C308.1, C309.1, C310.1, C311.1, C312.1, C313.1, C314.1, C315.1, C316.1, C317.1, C318.1, C319.1, C320.1, C321.1, IC5.A1 (VDDQ_1), IC5.A8 (VDDQ_2), IC5.B2 (VDD_1), IC5.C1 (VDDQ_3), IC5.C9 (VDDQ_4), IC5.D2 (VDDQ_5), IC5.D9 (VDD_2), IC5.E9 (VDDQ_6), IC5.F1 (VDDQ_7), IC5.G7 (VDD_3), IC5.H2 (VDDQ_8), IC5.H9 (VDDQ_9), IC5.K2 (VDD_4), IC5.K8 (VDD_5), IC5.N1 (VDD_6), IC5.N9 (VDD_7), IC5.R1 (VDD_8), IC5.R9 (VDD_9), IC6.A1 (VDDQ_1), IC6.A8 (VDDQ_2), IC6.B2 (VDD_1), IC6.C1 (VDDQ_3), IC6.C9 (VDDQ_4), IC6.D2 (VDDQ_5), IC6.D9 (VDD_2), IC6.E9 (VDDQ_6), IC6.F1 (VDDQ_7), IC6.G7 (VDD_3), IC6.H2 (VDDQ_8), IC6.H9 (VDDQ_9), IC6.K2 (VDD_4), IC6.K8 (VDD_5), IC6.N1 (VDD_6), IC6.N9 (VDD_7), IC6.R1 (VDD_8), IC6.R9 (VDD_9)
GND1: C187.2, C189.2, C190.2, C282.2, C283.2, C284.2, C285.2, C286.2, C287.2, C288.2, C289.2, C290.2, C291.2, C292.2, C293.2, C294.2, C295.2, C296.2, C297.2, C298.2, C299.2, C300.2, C301.2, C302.2, C303.2, C304.2, C305.2, C306.2, C307.2, C308.2, C309.2, C310.2, C311.2, C312.2, C313.2, C314.2, C315.2, C316.2, C317.2, C318.2, C319.2, C320.2, C321.2, IC5.A9 (VSS_1), IC5.B1 (VSSQ_1), IC5.B3 (VSS_2), IC5.B9 (VSSQ_2), IC5.D1 (VSSQ_3), IC5.D8 (VSSQ_4), IC5.E1 (VSS_3), IC5.E2 (VSSQ_5), IC5.E8 (VSSQ_6), IC5.F9 (VSSQ_7), IC5.G1 (VSSQ_8), IC5.G8 (VSS_4), IC5.G9 (VSSQ_9), IC5.J2 (VSS_5), IC5.J8 (VSS_6), IC5.M1 (VSS_7), IC5.M9 (VSS_8), IC5.P1 (VSS_9), IC5.P9 (VSS_10), IC5.T1 (VSS_11), IC5.T9 (VSS_12), IC6.A9 (VSS_1), IC6.B1 (VSSQ_1), IC6.B3 (VSS_2), IC6.B9 (VSSQ_2), IC6.D1 (VSSQ_3), IC6.D8 (VSSQ_4), IC6.E1 (VSS_3), IC6.E2 (VSSQ_5), IC6.E8 (VSSQ_6), IC6.F9 (VSSQ_7), IC6.G1 (VSSQ_8), IC6.G8 (VSS_4), IC6.G9 (VSSQ_9), IC6.J2 (VSS_5), IC6.J8 (VSS_6), IC6.M1 (VSS_7), IC6.M9 (VSS_8), IC6.P1 (VSS_9), IC6.P9 (VSS_10), IC6.T1 (VSS_11), IC6.T9 (VSS_12), R93.2, R94.1, R97.2, R98.1
unnamed: C190.1, R95.2, R96.1
unnamed: IC5.L8 (ZQ), R93.1
unnamed: IC6.L8 (ZQ), R97.1
PS_DDR3_BA0: IC5.M2 (BA0), IC6.M2 (BA0)
PS_DDR3_BA1: IC5.N8 (BA1), IC6.N8 (BA1)
PS_DDR3_BA2: IC5.M3 (BA2), IC6.M3 (BA2)
PS_DDR3_CAS-: IC5.K3 (CAS#), IC6.K3 (CAS#)
PS_DDR3_CK+: IC5.J7 (CK), IC6.J7 (CK), R95.1
PS_DDR3_CK-: IC5.K7 (CK#), IC6.K7 (CK#), R96.2
PS_DDR3_CKE: IC5.K9 (CKE), IC6.K9 (CKE)
PS_DDR3_CS-: IC5.L2 (CS#), IC6.L2 (CS#)
PS_DDR3_DQ0: IC5.A3 (DQ15)
PS_DDR3_DQ1: IC5.C3 (DQ9)
PS_DDR3_DQ2: IC5.C2 (DQ11)
PS_DDR3_DQ3: IC5.A2 (DQ13)
PS_DDR3_DQ4: IC5.B8 (DQ14)
PS_DDR3_DQ5: IC5.D7 (DQ8)
PS_DDR3_DQ6: IC5.A7 (DQ12)
PS_DDR3_DQ7: IC5.C8 (DQ10)
PS_DDR3_DQ8: IC5.H3 (DQ4)
PS_DDR3_DQ9: IC5.E3 (DQ0)
PS_DDR3_DQ10: IC5.G2 (DQ6)
PS_DDR3_DQ11: IC5.H7 (DQ7)
PS_DDR3_DQ12: IC5.F7 (DQ1)
PS_DDR3_DQ13: IC5.H8 (DQ5)
PS_DDR3_DQ14: IC5.F2 (DQ2)
PS_DDR3_DQ15: IC5.F8 (DQ3)
PS_DDR3_DQ16: IC6.E3 (DQ0)
PS_DDR3_DQ17: IC6.H3 (DQ4)
PS_DDR3_DQ18: IC6.G2 (DQ6)
PS_DDR3_DQ19: IC6.F2 (DQ2)
PS_DDR3_DQ20: IC6.F7 (DQ1)
PS_DDR3_DQ21: IC6.F8 (DQ3)
PS_DDR3_DQ22: IC6.H8 (DQ5)
PS_DDR3_DQ23: IC6.H7 (DQ7)
PS_DDR3_DQ24: IC6.A2 (DQ13)
PS_DDR3_DQ25: IC6.C8 (DQ10)
PS_DDR3_DQ26: IC6.A3 (DQ15)
PS_DDR3_DQ27: IC6.B8 (DQ14)
PS_DDR3_DQ28: IC6.C3 (DQ9)
PS_DDR3_DQ29: IC6.D7 (DQ8)
PS_DDR3_DQ30: IC6.C2 (DQ11)
PS_DDR3_DQ31: IC6.A7 (DQ12)
PS_DDR3_DQS0+: IC5.C7 (UDQS)
PS_DDR3_DQS0-: IC5.B7 (UDQS#)
PS_DDR3_DQS1+: IC5.F3 (LDQS)
PS_DDR3_DQS1-: IC5.G3 (LDQS#)
PS_DDR3_DQS2+: IC6.F3 (LDQS)
PS_DDR3_DQS2-: IC6.G3 (LDQS#)
PS_DDR3_DQS3+: IC6.C7 (UDQS)
PS_DDR3_DQS3-: IC6.B7 (UDQS#)
PS_DDR3_ODT: IC5.K1 (ODT), IC6.K1 (ODT)
PS_DDR3_RAS-: IC5.J3 (RAS#), IC6.J3 (RAS#)
PS_DDR3_RST-: IC5.T2 (RESET#), IC6.T2 (RESET#)
PS_DDR3_WE-: IC5.L3 (WE#), IC6.L3 (WE#)
PS_DDR_A0: IC5.N3 (A0), IC6.N3 (A0)
PS_DDR_A1: IC5.P7 (A1), IC6.P7 (A1)
PS_DDR_A2: IC5.P3 (A2), IC6.P3 (A2)
PS_DDR_A3: IC5.N2 (A3), IC6.N2 (A3)
PS_DDR_A4: IC5.P8 (A4), IC6.P8 (A4)
PS_DDR_A5: IC5.P2 (A5), IC6.P2 (A5)
PS_DDR_A6: IC5.R8 (A6), IC6.R8 (A6)
PS_DDR_A7: IC5.R2 (A7), IC6.R2 (A7)
PS_DDR_A8: IC5.T8 (A8), IC6.T8 (A8)
PS_DDR_A9: IC5.R3 (A9), IC6.R3 (A9)
PS_DDR_A10: IC5.L7 (A10/AP), IC6.L7 (A10/AP)
PS_DDR_A11: IC5.R7 (A11), IC6.R7 (A11)
PS_DDR_A12: IC5.N7 (A12/BC#), IC6.N7 (A12/BC#)
PS_DDR_A13: IC5.T3 (A13), IC6.T3 (A13)
PS_DDR_A14: IC5.T7 (A14), IC6.T7 (A14)
PS_DDR_A15: IC5.M7 (A15), IC6.M7 (A15), R94.2, R98.2
PS_DDR_DM0_502: IC5.D3 (UDM)
PS_DDR_DM1_502: IC5.E7 (LDM)
PS_DDR_DM2_502: IC6.E7 (LDM)
PS_DDR_DM3_502: IC6.D3 (UDM)

Notes on the sheet:
Byte lanes swapped for layout: DQS0 DDR_BL0 DDR_DQ 0=>7 MEM DQ8=>15 DQS1 DDR_BL1 DDR_DQ 8=>15 MEM DQ0=>7 DQS2 DDR_BL2 DDR_DQ 16=>23 MEM DQT 0=>7 DQS3 DDR_BL3 DDR_DQ 24=>31 MEM DQT 8=>15
This should not be Connected It is used as A15 in 512M Memory
SDR-B 7020 PS Memory
Shared Ref Voltage 2 caps at each chip
Processing System (PS) Memory
Reference Transient Suppression Per Memory Chip. Might need ferrites in Vram and Gnd
Place at end of bus: E310 used 36 ohms+cap Zetbret and E200 used Bal. 100 ohm & NO cap
This chip replaces the obsolete 4Gbit chips used in E310 PL Data Scrambled like the E310 for UHD compadibility?? It also is greater than the Zedboard dual 2Gbit chips
Note: LDM(E7) and UDM(D3) swapped for layout reasons
PS_DDR3_DQ
PS_DDR_A
