WA1CYB/SDR_Gen2/Zynq-XC7Z020-sheet-4-page12.kicad_sch

## KiCad design Zynq-XC7Z020-sheet-4-page12.kicad_sch (2026-04-03)

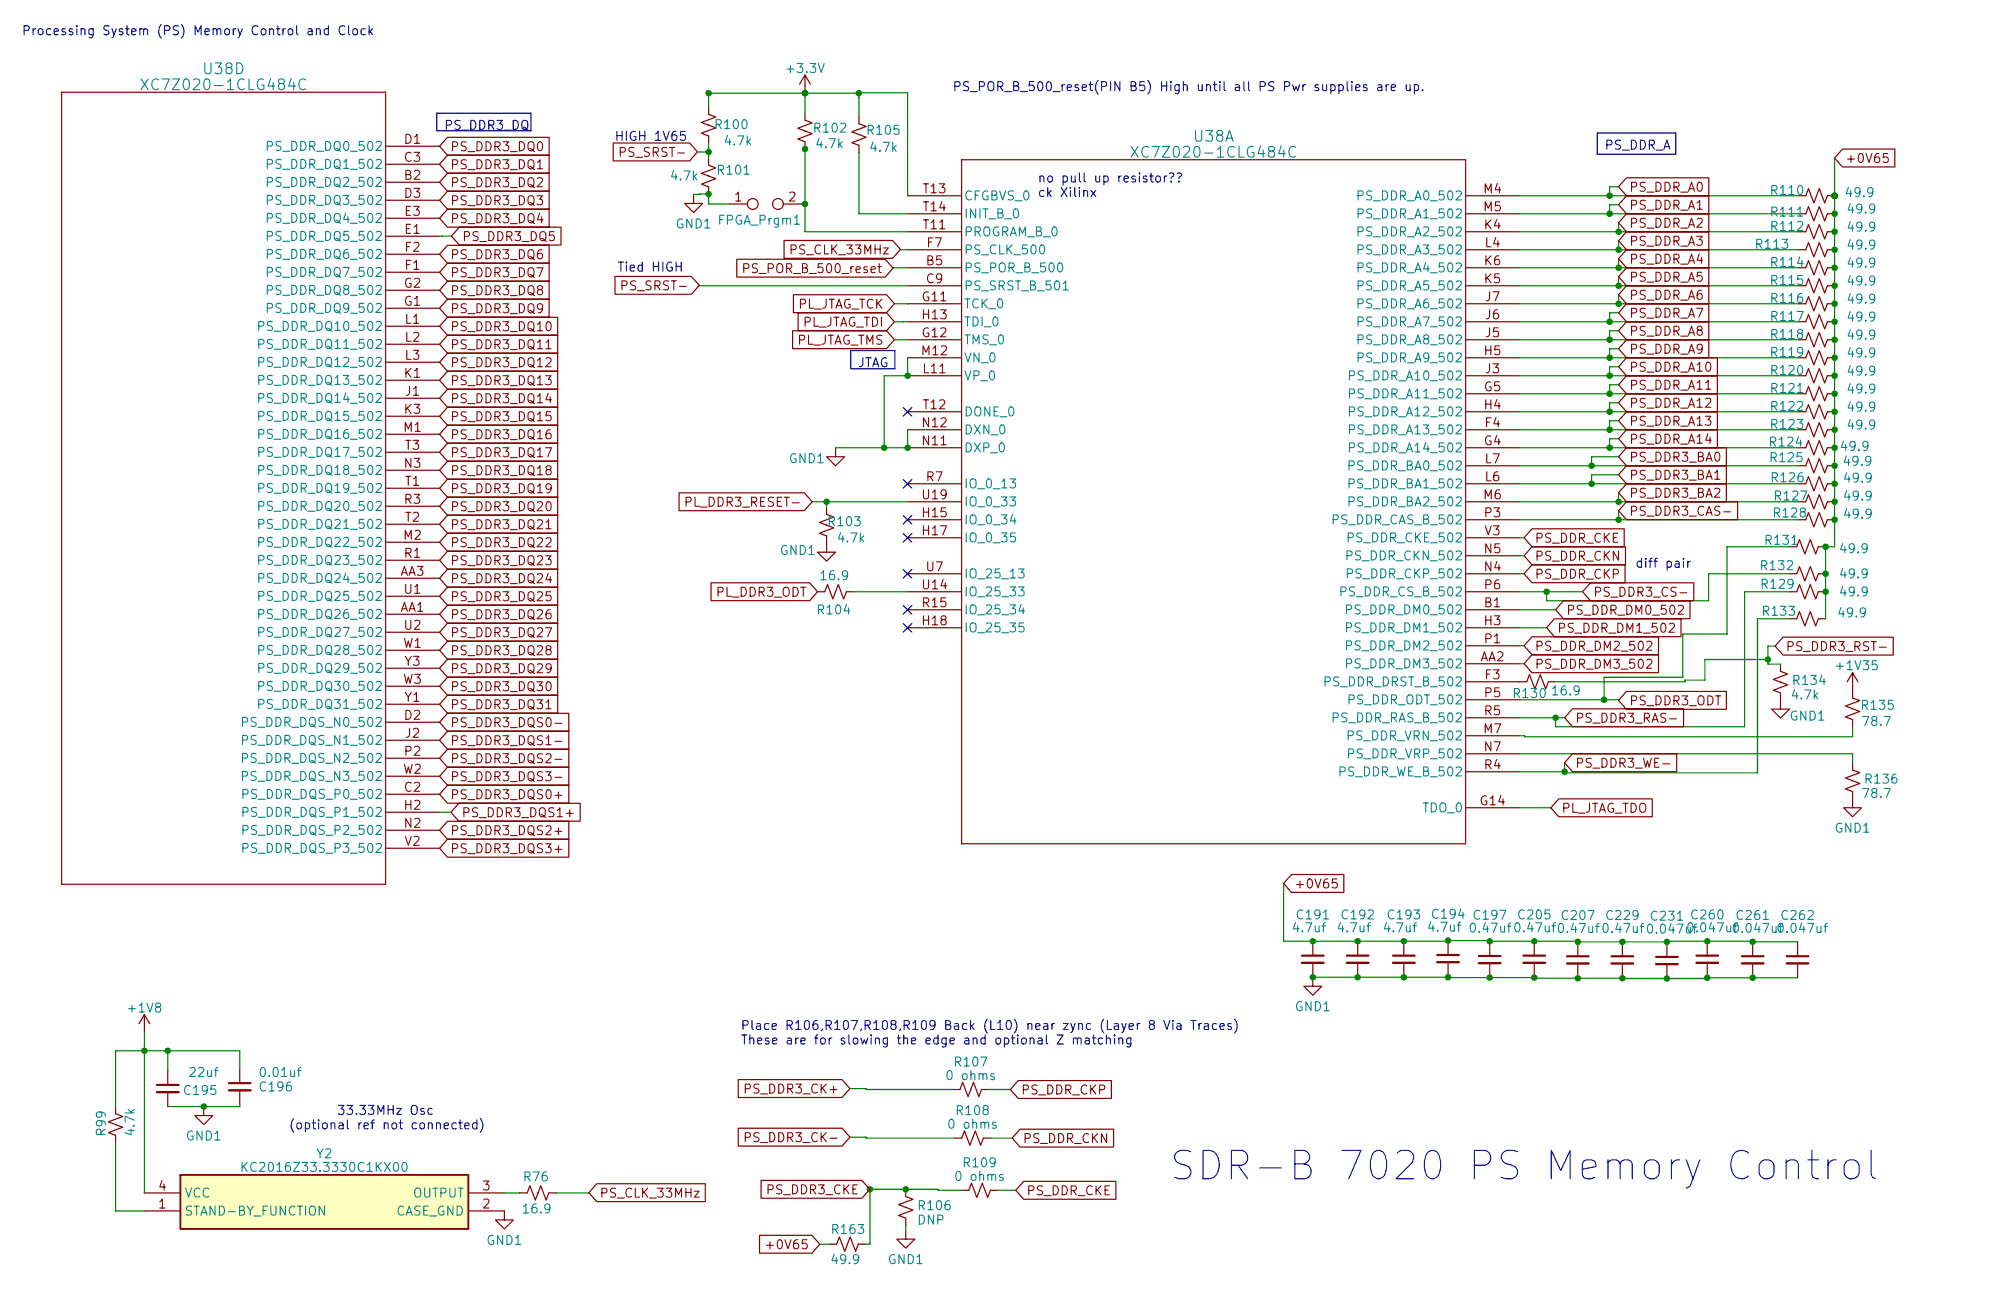
[picture p20: schematic Zynq-XC7Z020-sheet-4-page12.kicad_sch]

Parts:
C191, C192, C193, C194: 4.7uf; C_0402_1005Metric
C195: 22uf; C_0805_2012Metric
C196: 0.01uf; C_0201_0603Metric
C197, C205, C207, C229: 0.47uf; C_0201_0603Metric
C231, C260, C261, C262: 0.047uf; C_0201_0603Metric
FPGA_Prgm1: TestPoint_2Pads_Pitch2.54mm_Drill0.8mm
R76, R104, R130: 16.9; R_0201_0603Metric
R99, R100, R101, R102, R103, R105, R134: 4.7k; R_0201_0603Metric
R106: DNP; R_0201_0603Metric
R107, R108, R109: 0 ohms; R_0201_0603Metric
R110, R111, R112, R113, R114, R115, R116, R117, R118, R119, R120, R121, R122, R123, R124, R125, R126, R127, R128, R129, R131, R132, R133, R163: 49.9; R_0201_0603Metric
R135, R136: 78.7; R_0201_0603Metric
U38: XC7Z020-1CLG484C; Xilinx_CLG484_CLG485
Y2: KC2016Z33.3330C1KX00; KC2016Z333330C1KX00; Manufacturer_Part_Number KC2016Z33.3330C1KX00; Mouser Part Number 581-KC2016Z333C1KX00

Connections:
+0V65: C191.1, C192.1, C193.1, C194.1, C197.1, C205.1, C207.1, C229.1, C231.1, C260.1, C261.1, C262.1, R110.2, R111.2, R112.2, R113.2, R114.2, R115.2, R116.2, R117.2, R118.2, R119.2, R120.2, R121.2, R122.2, R123.2, R124.2, R125.2, R126.2, R127.2, R128.2, R129.2, R131.2, R132.2, R133.2, R163.2
+1V8: C195.1, C196.1, R99.2, Y2.4 (VCC)
+1V35: R135.1
+3.3V: R100.1, R102.1, R105.1, U38.T13 (CFGBVS_0)
GND1: C191.2, C192.2, C193.2, C194.2, C195.2, C196.2, C197.2, C205.2, C207.2, C229.2, C231.2, C260.2, C261.2, C262.2, FPGA_Prgm1.1, R101.2, R103.2, R106.2, R134.2, R136.2, U38.L11 (VP_0), U38.M12 (VN_0), U38.N11 (DXP_0), U38.N12 (DXN_0), Y2.2 (CASE_GND)
unnamed: FPGA_Prgm1.2, R102.2, U38.T11 (PROGRAM_B_0)
unnamed: R76.2, Y2.3 (OUTPUT)
unnamed: R99.1, Y2.1 (STAND-BY_FUNCTION)
unnamed: R104.1, U38.U14 (IO_25_33)
unnamed: R105.2, U38.T14 (INIT_B_0)
unnamed: R130.1, U38.F3 (PS_DDR_DRST_B_502)
unnamed: R135.2, U38.M7 (PS_DDR_VRN_502)
unnamed: R136.1, U38.N7 (PS_DDR_VRP_502)
PL_DDR3_ODT: R104.2
PL_DDR3_RESET-: R103.1, U38.U19 (IO_0_33)
PL_JTAG_TCK: U38.G11 (TCK_0)
PL_JTAG_TDI: U38.H13 (TDI_0)
PL_JTAG_TDO: U38.G14 (TDO_0)
PL_JTAG_TMS: U38.G12 (TMS_0)
PS_CLK_33MHz: R76.1, U38.F7 (PS_CLK_500)
PS_DDR3_BA0: R125.1, U38.L7 (PS_DDR_BA0_502)
PS_DDR3_BA1: R126.1, U38.L6 (PS_DDR_BA1_502)
PS_DDR3_BA2: R127.1, U38.M6 (PS_DDR_BA2_502)
PS_DDR3_CAS-: R128.1, U38.P3 (PS_DDR_CAS_B_502)
PS_DDR3_CK+: R107.2
PS_DDR3_CK-: R108.2
PS_DDR3_CKE: R106.1, R109.2, R163.1
PS_DDR3_CS-: R132.1, U38.P6 (PS_DDR_CS_B_502)
PS_DDR3_DQ0: U38.D1 (PS_DDR_DQ0_502)
PS_DDR3_DQ1: U38.C3 (PS_DDR_DQ1_502)
PS_DDR3_DQ2: U38.B2 (PS_DDR_DQ2_502)
PS_DDR3_DQ3: U38.D3 (PS_DDR_DQ3_502)
PS_DDR3_DQ4: U38.E3 (PS_DDR_DQ4_502)
PS_DDR3_DQ5: U38.E1 (PS_DDR_DQ5_502)
PS_DDR3_DQ6: U38.F2 (PS_DDR_DQ6_502)
PS_DDR3_DQ7: U38.F1 (PS_DDR_DQ7_502)
PS_DDR3_DQ8: U38.G2 (PS_DDR_DQ8_502)
PS_DDR3_DQ9: U38.G1 (PS_DDR_DQ9_502)
PS_DDR3_DQ10: U38.L1 (PS_DDR_DQ10_502)
PS_DDR3_DQ11: U38.L2 (PS_DDR_DQ11_502)
PS_DDR3_DQ12: U38.L3 (PS_DDR_DQ12_502)
PS_DDR3_DQ13: U38.K1 (PS_DDR_DQ13_502)
PS_DDR3_DQ14: U38.J1 (PS_DDR_DQ14_502)
PS_DDR3_DQ15: U38.K3 (PS_DDR_DQ15_502)
PS_DDR3_DQ16: U38.M1 (PS_DDR_DQ16_502)
PS_DDR3_DQ17: U38.T3 (PS_DDR_DQ17_502)
PS_DDR3_DQ18: U38.N3 (PS_DDR_DQ18_502)
PS_DDR3_DQ19: U38.T1 (PS_DDR_DQ19_502)
PS_DDR3_DQ20: U38.R3 (PS_DDR_DQ20_502)
PS_DDR3_DQ21: U38.T2 (PS_DDR_DQ21_502)
PS_DDR3_DQ22: U38.M2 (PS_DDR_DQ22_502)
PS_DDR3_DQ23: U38.R1 (PS_DDR_DQ23_502)
PS_DDR3_DQ24: U38.AA3 (PS_DDR_DQ24_502)
PS_DDR3_DQ25: U38.U1 (PS_DDR_DQ25_502)
PS_DDR3_DQ26: U38.AA1 (PS_DDR_DQ26_502)
PS_DDR3_DQ27: U38.U2 (PS_DDR_DQ27_502)
PS_DDR3_DQ28: U38.W1 (PS_DDR_DQ28_502)
PS_DDR3_DQ29: U38.Y3 (PS_DDR_DQ29_502)
PS_DDR3_DQ30: U38.W3 (PS_DDR_DQ30_502)
PS_DDR3_DQ31: U38.Y1 (PS_DDR_DQ31_502)
PS_DDR3_DQS0+: U38.C2 (PS_DDR_DQS_P0_502)
PS_DDR3_DQS0-: U38.D2 (PS_DDR_DQS_N0_502)
PS_DDR3_DQS1+: U38.H2 (PS_DDR_DQS_P1_502)
PS_DDR3_DQS1-: U38.J2 (PS_DDR_DQS_N1_502)
PS_DDR3_DQS2+: U38.N2 (PS_DDR_DQS_P2_502)
PS_DDR3_DQS2-: U38.P2 (PS_DDR_DQS_N2_502)
PS_DDR3_DQS3+: U38.V2 (PS_DDR_DQS_P3_502)
PS_DDR3_DQS3-: U38.W2 (PS_DDR_DQS_N3_502)
PS_DDR3_ODT: R131.1, U38.P5 (PS_DDR_ODT_502)
PS_DDR3_RAS-: R129.1, U38.R5 (PS_DDR_RAS_B_502)
PS_DDR3_RST-: R130.2, R134.1
PS_DDR3_WE-: R133.1, U38.R4 (PS_DDR_WE_B_502)
PS_DDR_A0: R110.1, U38.M4 (PS_DDR_A0_502)
PS_DDR_A1: R111.1, U38.M5 (PS_DDR_A1_502)
PS_DDR_A2: R112.1, U38.K4 (PS_DDR_A2_502)
PS_DDR_A3: R113.1, U38.L4 (PS_DDR_A3_502)
PS_DDR_A4: R114.1, U38.K6 (PS_DDR_A4_502)
PS_DDR_A5: R115.1, U38.K5 (PS_DDR_A5_502)
PS_DDR_A6: R116.1, U38.J7 (PS_DDR_A6_502)
PS_DDR_A7: R117.1, U38.J6 (PS_DDR_A7_502)
PS_DDR_A8: R118.1, U38.J5 (PS_DDR_A8_502)
PS_DDR_A9: R119.1, U38.H5 (PS_DDR_A9_502)
PS_DDR_A10: R120.1, U38.J3 (PS_DDR_A10_502)
PS_DDR_A11: R121.1, U38.G5 (PS_DDR_A11_502)
PS_DDR_A12: R122.1, U38.H4 (PS_DDR_A12_502)
PS_DDR_A13: R123.1, U38.F4 (PS_DDR_A13_502)
PS_DDR_A14: R124.1, U38.G4 (PS_DDR_A14_502)
PS_DDR_CKE: R109.1, U38.V3 (PS_DDR_CKE_502)
PS_DDR_CKN: R108.1, U38.N5 (PS_DDR_CKN_502)
PS_DDR_CKP: R107.1, U38.N4 (PS_DDR_CKP_502)
PS_DDR_DM0_502: U38.B1 (PS_DDR_DM0_502)
PS_DDR_DM1_502: U38.H3 (PS_DDR_DM1_502)
PS_DDR_DM2_502: U38.P1 (PS_DDR_DM2_502)
PS_DDR_DM3_502: U38.AA2 (PS_DDR_DM3_502)
PS_POR_B_500_reset: U38.B5 (PS_POR_B_500)
PS_SRST-: R100.2, R101.1, U38.C9 (PS_SRST_B_501)

Notes on the sheet:
Place R106,R107,R108,R109 Back (L10) near zync (Layer 8 Via Traces) These are for slowing the edge and optional Z matching
Tied HIGH
PS_POR_B_500_reset(PIN B5) High until all PS Pwr supplies are up.
diff pair
33.33MHz Osc (optional ref not connected)
Processing System (PS) Memory Control and Clock
SDR-B 7020 PS Memory Control
HIGH 1V65
no pull up resistor?? ck Xilinx
PS_DDR3_DQ
PS_DDR_A
JTAG
