WA1CYB/SDR_Gen2/Zynq-XC7Z020-sheet-5-page17.kicad_sch

## KiCad design Zynq-XC7Z020-sheet-5-page17.kicad_sch (2026-04-03)

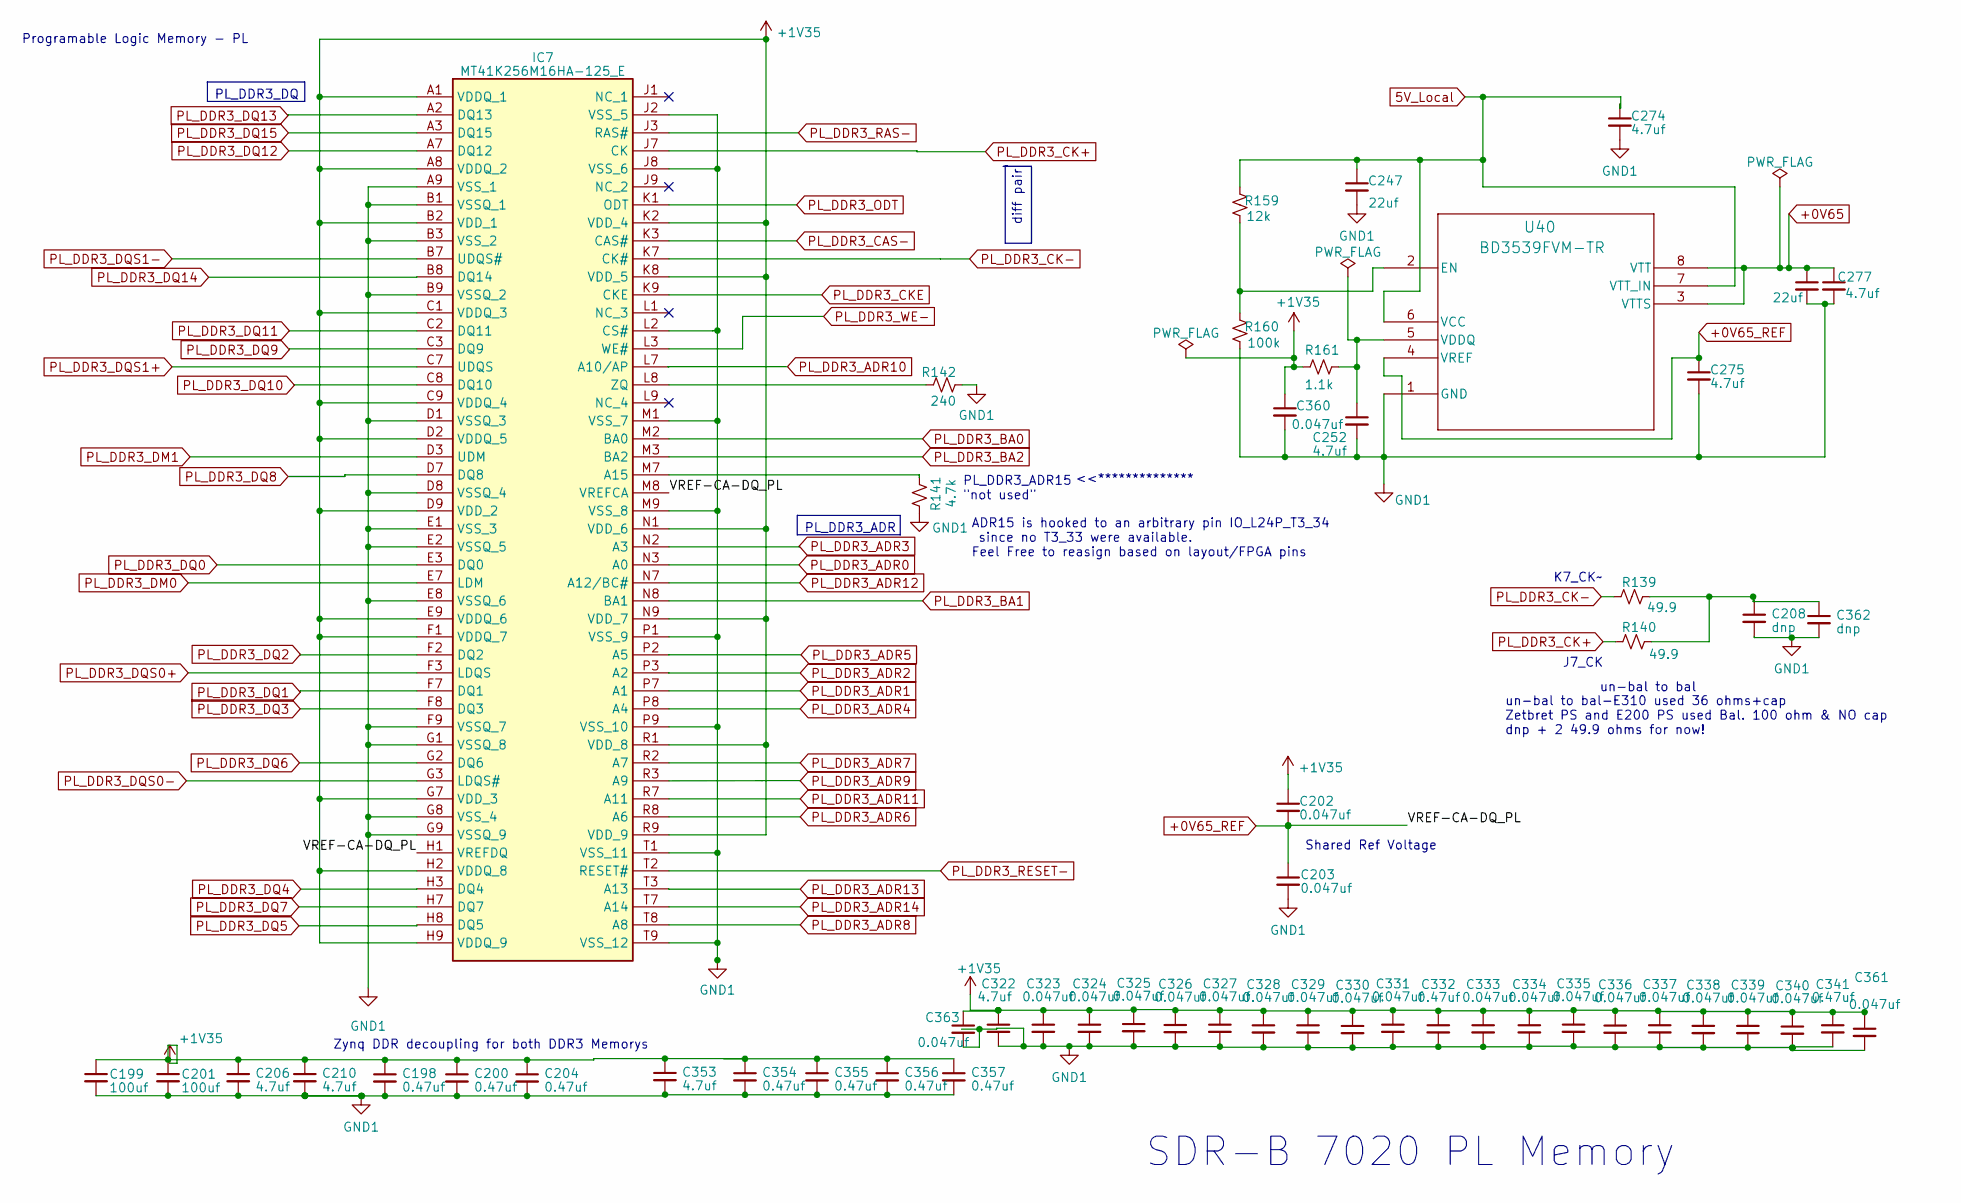
[picture p21: schematic Zynq-XC7Z020-sheet-5-page17.kicad_sch]

Parts:
C198, C200, C204, C332, C341, C354, C355, C356, C357: 0.47uf; C_0201_0603Metric
C199, C201: 100uf; C_1206_3216Metric
C202, C203, C323, C324, C325, C326, C327, C328, C329, C330, C331, C333, C334, C335, C336, C337, C338, C339, C340, C360, C361, C363: 0.047uf; C_0201_0603Metric
C206, C210, C252, C274, C275, C277, C322, C353: 4.7uf; C_0402_1005Metric
C208, C362: dnp; C_0201_0603Metric
C247, C276: 22uf; C_1206_3216Metric
IC7: MT41K256M16HA-125_E; BGA96C80P9X16_900X1400X120; Manufacturer_Part_Number MT41K512M16HA-125:A; Mouser Part Number 340-286628-TRAY
R139, R140: 49.9; R_0201_0603Metric
R141: 4.7k; R_0201_0603Metric
R142: 240; R_0201_0603Metric
R159: 12k; R_0201_0603Metric
R160: 100k; R_0201_0603Metric
R161: 1.1k; R_0201_0603Metric
U40: BD3539FVM-TR; MSOP8_ROM

Connections:
5V_Local: C247.1, C274.1, R159.1, U40.6 (VCC), U40.7 (VTT_IN)
+0V65: C276.1, C277.1, U40.3 (VTTS), U40.8 (VTT)
+0V65_REF: C202.2, C203.1, C275.1, IC7.H1 (VREFDQ), IC7.M8 (VREFCA), U40.4 (VREF)
+1V35: C198.1, C199.1, C200.1, C201.1, C202.1, C204.1, C206.1, C210.1, C322.1, C323.1, C324.1, C325.1, C326.1, C327.1, C328.1, C329.1, C330.1, C331.1, C332.1, C333.1, C334.1, C335.1, C336.1, C337.1, C338.1, C339.1, C340.1, C341.1, C353.1, C354.1, C355.1, C356.1, C357.1, C360.1, C361.1, C363.1, IC7.A1 (VDDQ_1), IC7.A8 (VDDQ_2), IC7.B2 (VDD_1), IC7.C1 (VDDQ_3), IC7.C9 (VDDQ_4), IC7.D2 (VDDQ_5), IC7.D9 (VDD_2), IC7.E9 (VDDQ_6), IC7.F1 (VDDQ_7), IC7.G7 (VDD_3), IC7.H2 (VDDQ_8), IC7.H9 (VDDQ_9), IC7.K2 (VDD_4), IC7.K8 (VDD_5), IC7.N1 (VDD_6), IC7.N9 (VDD_7), IC7.R1 (VDD_8), IC7.R9 (VDD_9), R161.1
GND1: C198.2, C199.2, C200.2, C201.2, C203.2, C204.2, C206.2, C208.2, C210.2, C247.2, C252.2, C274.2, C275.2, C276.2, C277.2, C322.2, C323.2, C324.2, C325.2, C326.2, C327.2, C328.2, C329.2, C330.2, C331.2, C332.2, C333.2, C334.2, C335.2, C336.2, C337.2, C338.2, C339.2, C340.2, C341.2, C353.2, C354.2, C355.2, C356.2, C357.2, C360.2, C361.2, C362.2, C363.2, IC7.A9 (VSS_1), IC7.B1 (VSSQ_1), IC7.B3 (VSS_2), IC7.B9 (VSSQ_2), IC7.D1 (VSSQ_3), IC7.D8 (VSSQ_4), IC7.E1 (VSS_3), IC7.E2 (VSSQ_5), IC7.E8 (VSSQ_6), IC7.F9 (VSSQ_7), IC7.G1 (VSSQ_8), IC7.G8 (VSS_4), IC7.G9 (VSSQ_9), IC7.J2 (VSS_5), IC7.J8 (VSS_6), IC7.L2 (CS#), IC7.M1 (VSS_7), IC7.M9 (VSS_8), IC7.P1 (VSS_9), IC7.P9 (VSS_10), IC7.T1 (VSS_11), IC7.T9 (VSS_12), R141.1, R142.2, R160.2, U40.1 (GND)
unnamed: C208.1, C362.1, R139.1, R140.1
unnamed: C252.1, R161.2, U40.5 (VDDQ)
unnamed: IC7.L8 (ZQ), R142.1
unnamed: IC7.M7 (A15), R141.2
unnamed: R159.2, R160.1, U40.2 (EN)
PL_DDR3_ADR0: IC7.N3 (A0)
PL_DDR3_ADR1: IC7.P7 (A1)
PL_DDR3_ADR2: IC7.P3 (A2)
PL_DDR3_ADR3: IC7.N2 (A3)
PL_DDR3_ADR4: IC7.P8 (A4)
PL_DDR3_ADR5: IC7.P2 (A5)
PL_DDR3_ADR6: IC7.R8 (A6)
PL_DDR3_ADR7: IC7.R2 (A7)
PL_DDR3_ADR8: IC7.T8 (A8)
PL_DDR3_ADR9: IC7.R3 (A9)
PL_DDR3_ADR10: IC7.L7 (A10/AP)
PL_DDR3_ADR11: IC7.R7 (A11)
PL_DDR3_ADR12: IC7.N7 (A12/BC#)
PL_DDR3_ADR13: IC7.T3 (A13)
PL_DDR3_ADR14: IC7.T7 (A14)
PL_DDR3_BA0: IC7.M2 (BA0)
PL_DDR3_BA1: IC7.N8 (BA1)
PL_DDR3_BA2: IC7.M3 (BA2)
PL_DDR3_CAS-: IC7.K3 (CAS#)
PL_DDR3_CK+: IC7.J7 (CK), R140.2
PL_DDR3_CK-: IC7.K7 (CK#), R139.2
PL_DDR3_CKE: IC7.K9 (CKE)
PL_DDR3_DM0: IC7.E7 (LDM)
PL_DDR3_DM1: IC7.D3 (UDM)
PL_DDR3_DQ0: IC7.E3 (DQ0)
PL_DDR3_DQ1: IC7.F7 (DQ1)
PL_DDR3_DQ2: IC7.F2 (DQ2)
PL_DDR3_DQ3: IC7.F8 (DQ3)
PL_DDR3_DQ4: IC7.H3 (DQ4)
PL_DDR3_DQ5: IC7.H8 (DQ5)
PL_DDR3_DQ6: IC7.G2 (DQ6)
PL_DDR3_DQ7: IC7.H7 (DQ7)
PL_DDR3_DQ8: IC7.D7 (DQ8)
PL_DDR3_DQ9: IC7.C3 (DQ9)
PL_DDR3_DQ10: IC7.C8 (DQ10)
PL_DDR3_DQ11: IC7.C2 (DQ11)
PL_DDR3_DQ12: IC7.A7 (DQ12)
PL_DDR3_DQ13: IC7.A2 (DQ13)
PL_DDR3_DQ14: IC7.B8 (DQ14)
PL_DDR3_DQ15: IC7.A3 (DQ15)
PL_DDR3_DQS0+: IC7.F3 (LDQS)
PL_DDR3_DQS0-: IC7.G3 (LDQS#)
PL_DDR3_DQS1+: IC7.C7 (UDQS)
PL_DDR3_DQS1-: IC7.B7 (UDQS#)
PL_DDR3_ODT: IC7.K1 (ODT)
PL_DDR3_RAS-: IC7.J3 (RAS#)
PL_DDR3_RESET-: IC7.T2 (RESET#)
PL_DDR3_WE-: IC7.L3 (WE#)

Notes on the sheet:
Zynq DDR decoupling for both DDR3 Memorys
Shared Ref Voltage
diff pair
un-bal to bal
un-bal to bal-E310 used 36 ohms+cap Zetbret PS and E200 PS used Bal. 100 ohm & NO cap dnp + 2 49.9 ohms for now!
K7_CK~
<<**************
ADR15 is hooked to an arbitrary pin IO_L24P_T3_34 since no T3_33 were available. Feel Free to reasign based on layout/FPGA pins
PL_DDR3_ADR15 "not used"
J7_CK
SDR-B 7020 PL Memory
Programable Logic Memory - PL
PL_DDR3_DQ
PL_DDR3_ADR
