WA1CYB/SDR_Gen2/Zynq-XC7Z020-sheet-6-page17.kicad_sch

## KiCad design Zynq-XC7Z020-sheet-6-page17.kicad_sch (2026-04-03)

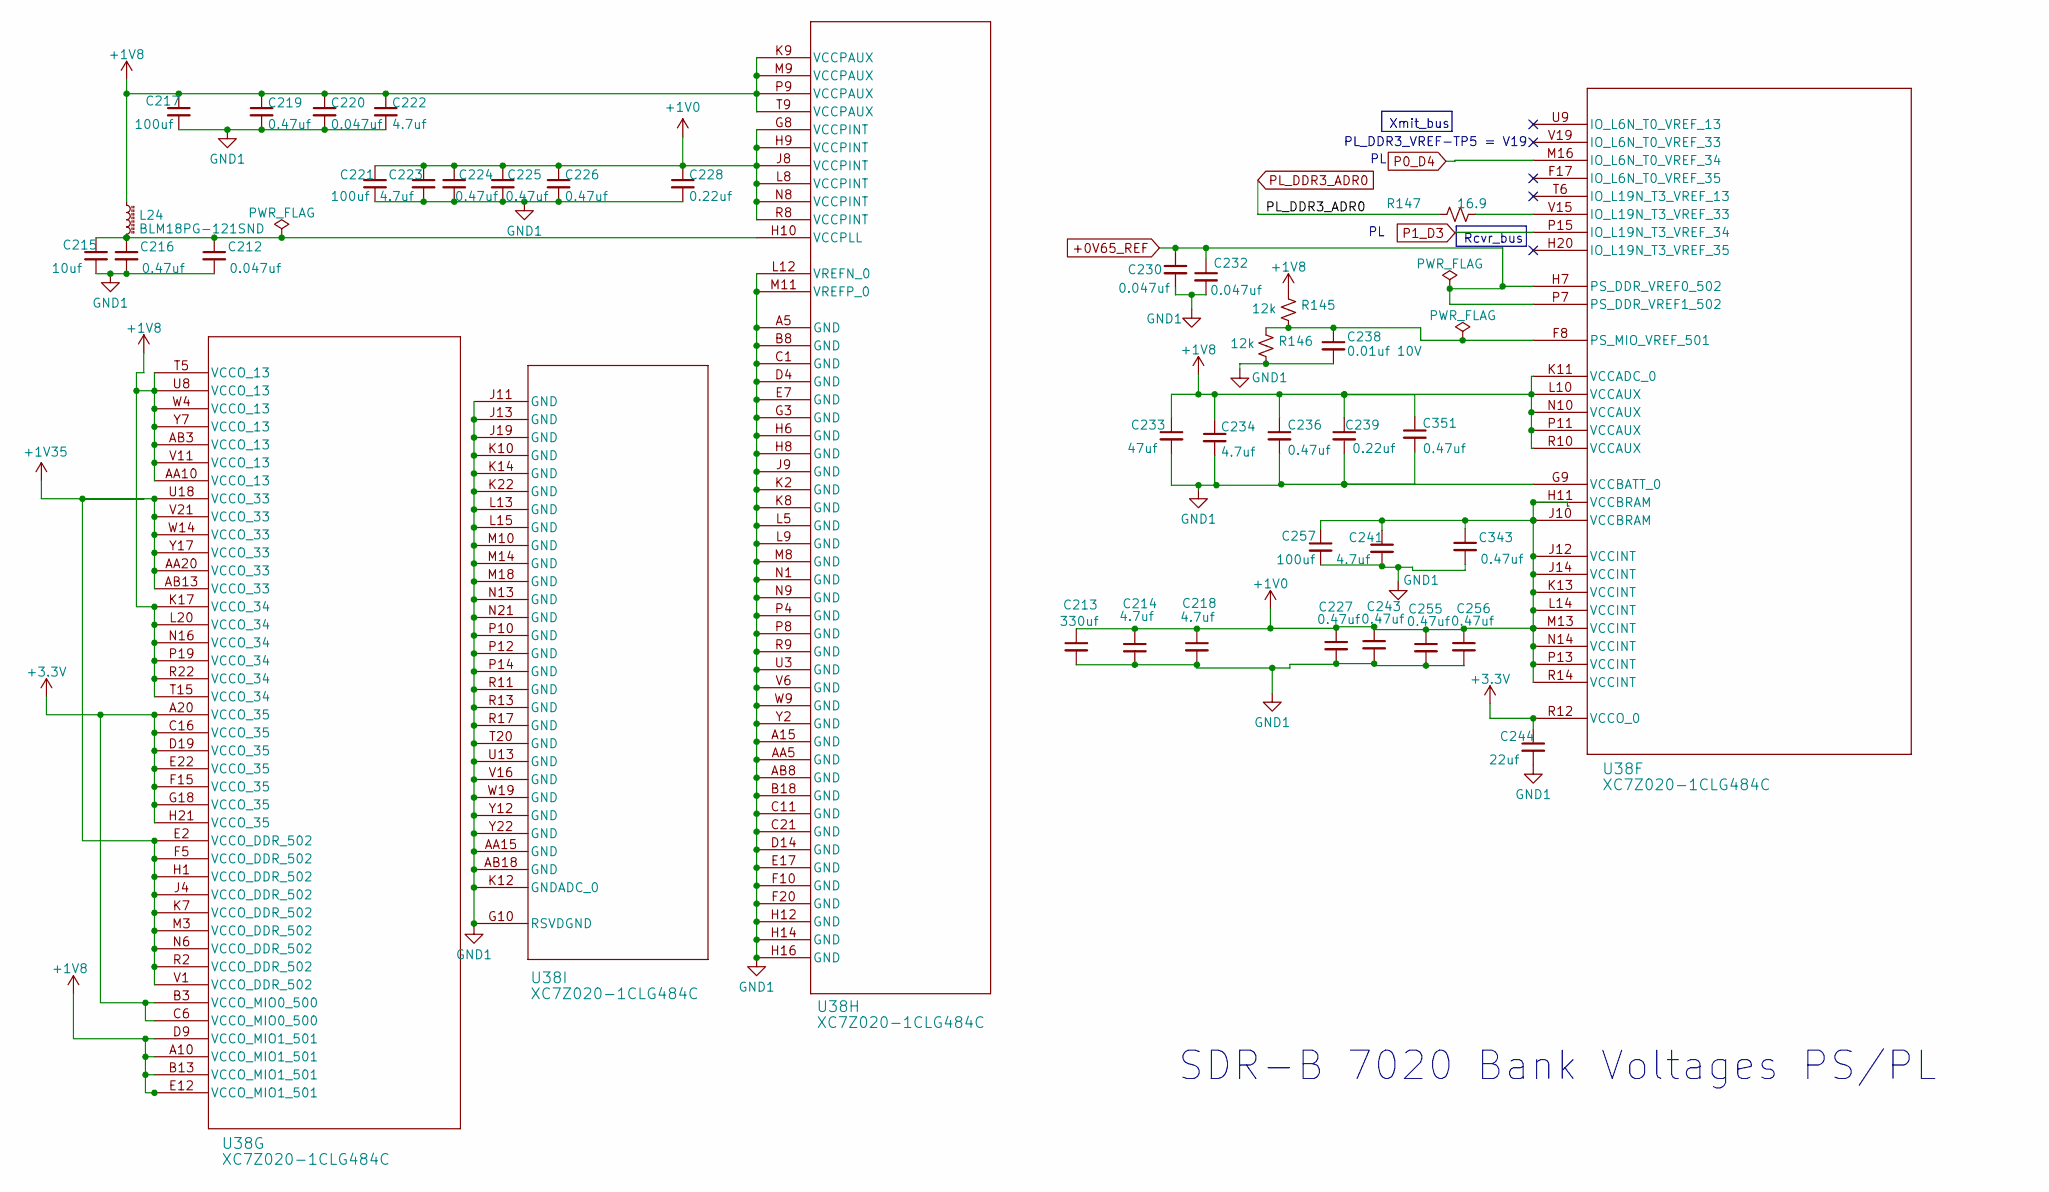
[picture p22: schematic Zynq-XC7Z020-sheet-6-page17.kicad_sch]

Parts:
C212, C220, C230, C232: 0.047uf; C_0201_0603Metric
C213: 330uf; C_1206_3216Metric
C214, C218, C222, C223, C234, C241: 4.7uf; C_0402_1005Metric
C215: 10uf; C_0402_1005Metric
C216, C219, C224, C225, C226, C227, C236, C243, C255, C256, C343, C351: 0.47uf; C_0201_0603Metric
C217, C221, C257: 100uf; C_1206_3216Metric
C228: 0.22uf; C_0402_1005Metric
C233: 47uf; C_1206_3216Metric
C238: 0.01uf 10V; C_0201_0603Metric
C239: 0.22uf; C_0201_0603Metric
C244: 22uf; C_1206_3216Metric
L24: BLM18PG-121SND; IND_BLM18_0603_MUR
R145, R146: 12k; R_0201_0603Metric
R147: 16.9; R_0201_0603Metric
U38: XC7Z020-1CLG484C; Xilinx_CLG484_CLG485

Connections:
+0V65_REF: C230.1, C232.1, U38.H7 (PS_DDR_VREF0_502), U38.P7 (PS_DDR_VREF1_502)
+1V0: C213.1, C214.1, C218.1, C221.1, C223.1, C224.1, C225.1, C226.1, C227.1, C228.1, C241.1, C243.1, C255.1, C256.1, C257.1, C343.1, U38.G8 (VCCPINT), U38.H9 (VCCPINT), U38.H11 (VCCBRAM), U38.J8 (VCCPINT), U38.J10 (VCCBRAM), U38.J12 (VCCINT), U38.J14 (VCCINT), U38.K13 (VCCINT), U38.L8 (VCCPINT), U38.L14 (VCCINT), U38.M13 (VCCINT), U38.N8 (VCCPINT), U38.N14 (VCCINT), U38.P13 (VCCINT), U38.R8 (VCCPINT), U38.R14 (VCCINT)
+1V8: C217.1, C219.1, C220.1, C222.1, C233.1, C234.1, C236.1, C239.1, C351.1, L24.1, R145.2, U38.A10 (VCCO_MIO1_501), U38.AA10 (VCCO_13), U38.AB3 (VCCO_13), U38.B13 (VCCO_MIO1_501), U38.D9 (VCCO_MIO1_501), U38.E12 (VCCO_MIO1_501), U38.K9 (VCCPAUX), U38.K11 (VCCADC_0), U38.K17 (VCCO_34), U38.L10 (VCCAUX), U38.L20 (VCCO_34), U38.M9 (VCCPAUX), U38.N10 (VCCAUX), U38.N16 (VCCO_34), U38.P9 (VCCPAUX), U38.P11 (VCCAUX), U38.P19 (VCCO_34), U38.R10 (VCCAUX), U38.R22 (VCCO_34), U38.T5 (VCCO_13), U38.T9 (VCCPAUX), U38.T15 (VCCO_34), U38.U8 (VCCO_13), U38.V11 (VCCO_13), U38.W4 (VCCO_13), U38.Y7 (VCCO_13)
+1V35: U38.AA20 (VCCO_33), U38.AB13 (VCCO_33), U38.E2 (VCCO_DDR_502), U38.F5 (VCCO_DDR_502), U38.H1 (VCCO_DDR_502), U38.J4 (VCCO_DDR_502), U38.K7 (VCCO_DDR_502), U38.M3 (VCCO_DDR_502), U38.N6 (VCCO_DDR_502), U38.R2 (VCCO_DDR_502), U38.U18 (VCCO_33), U38.V1 (VCCO_DDR_502), U38.V21 (VCCO_33), U38.W14 (VCCO_33), U38.Y17 (VCCO_33)
+3.3V: C244.1, U38.A20 (VCCO_35), U38.B3 (VCCO_MIO0_500), U38.C6 (VCCO_MIO0_500), U38.C16 (VCCO_35), U38.D19 (VCCO_35), U38.E22 (VCCO_35), U38.F15 (VCCO_35), U38.G18 (VCCO_35), U38.H21 (VCCO_35), U38.R12 (VCCO_0)
GND1: C212.2, C213.2, C214.2, C215.2, C216.2, C217.2, C218.2, C219.2, C220.2, C221.2, C222.2, C223.2, C224.2, C225.2, C226.2, C227.2, C228.2, C230.2, C232.2, C233.2, C234.2, C236.2, C238.2, C239.2, C241.2, C243.2, C244.2, C255.2, C256.2, C257.2, C343.2, C351.2, R146.1, U38.A5 (GND), U38.A15 (GND), U38.AA5 (GND), U38.AA15 (GND), U38.AB8 (GND), U38.AB18 (GND), U38.B8 (GND), U38.B18 (GND), U38.C1 (GND), U38.C11 (GND), U38.C21 (GND), U38.D4 (GND), U38.D14 (GND), U38.E7 (GND), U38.E17 (GND), U38.F10 (GND), U38.F20 (GND), U38.G3 (GND), U38.G9 (VCCBATT_0), U38.G10 (RSVDGND), U38.H6 (GND), U38.H8 (GND), U38.H12 (GND), U38.H14 (GND), U38.H16 (GND), U38.J9 (GND), U38.J11 (GND), U38.J13 (GND), U38.J19 (GND), U38.K2 (GND), U38.K8 (GND), U38.K10 (GND), U38.K12 (GNDADC_0), U38.K14 (GND), U38.K22 (GND), U38.L5 (GND), U38.L9 (GND), U38.L12 (VREFN_0), U38.L13 (GND), U38.L15 (GND), U38.M8 (GND), U38.M10 (GND), U38.M11 (VREFP_0), U38.M14 (GND), U38.M18 (GND), U38.N1 (GND), U38.N9 (GND), U38.N13 (GND), U38.N21 (GND), U38.P4 (GND), U38.P8 (GND), U38.P10 (GND), U38.P12 (GND), U38.P14 (GND), U38.R9 (GND), U38.R11 (GND), U38.R13 (GND), U38.R17 (GND), U38.T20 (GND), U38.U3 (GND), U38.U13 (GND), U38.V6 (GND), U38.V16 (GND), U38.W9 (GND), U38.W19 (GND), U38.Y2 (GND), U38.Y12 (GND), U38.Y22 (GND)
unnamed: C212.1, C215.1, C216.1, L24.2, U38.H10 (VCCPLL)
unnamed: C238.1, R145.1, R146.2, U38.F8 (PS_MIO_VREF_501)
unnamed: R147.1, U38.V15 (IO_L19N_T3_VREF_33)
P0_D4: U38.M16 (IO_L6N_T0_VREF_34)
P1_D3: U38.P15 (IO_L19N_T3_VREF_34)
PL_DDR3_ADR0: R147.2

Notes on the sheet:
SDR-B 7020 Bank Voltages PS/PL
PL_DDR3_VREF-TP5 = V19
Xmit_bus
Rcvr_bus
