WA1CYB/SDR_Gen2/Zynq-XC7Z020-sheet-7-page21.kicad_sch

## KiCad design Zynq-XC7Z020-sheet-7-page21.kicad_sch (2026-04-03)

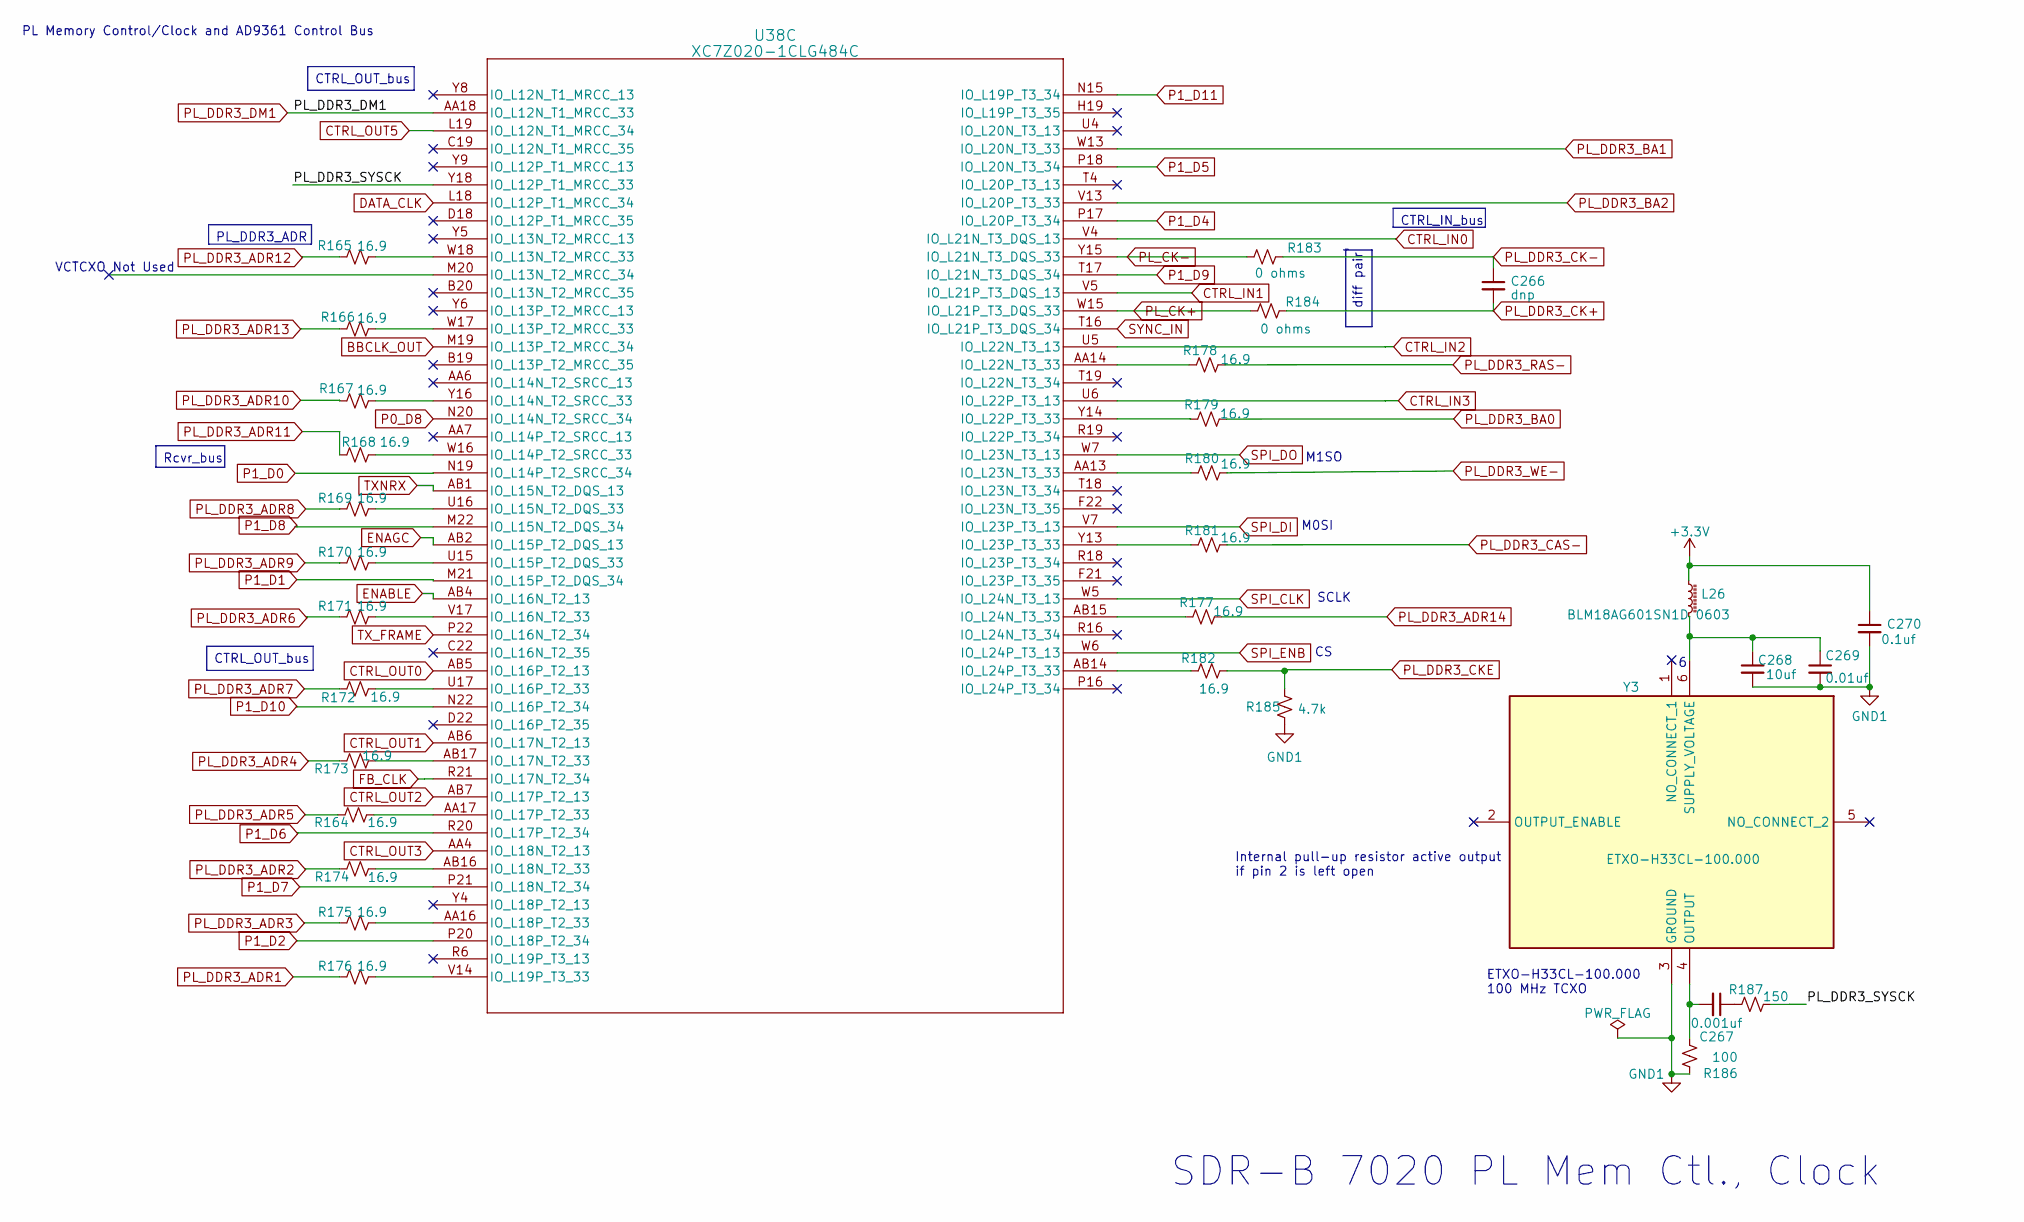
[picture p23: schematic Zynq-XC7Z020-sheet-7-page21.kicad_sch]

Parts:
C266: dnp; C_0201_0603Metric
C267: 0.001uf; C_0201_0603Metric
C268: 10uf; C_0402_1005Metric
C269: 0.01uf; C_0201_0603Metric
C270: 0.1uf; C_0201_0603Metric
L26: BLM18AG601SN1D 0603; IND_BLM18_0603_MUR
R164, R165, R166, R167, R168, R169, R170, R171, R172, R173, R174, R175, R176, R177, R178, R179, R180, R181, R182: 16.9; R_0201_0603Metric
R183, R184: 0 ohms; R_0201_0603Metric
R185: 4.7k; R_0201_0603Metric
R186: 100; R_0805_2012Metric
R187: 150; R_0805_2012Metric
U38: XC7Z020-1CLG484C; Xilinx_CLG484_CLG485
Y3: ETXO-H33CL-100.000; ETXOH33CL100000; Manufacturer_Part_Number ETXO-H33CL-100.000; Mouser Part Number 520-ETXOH33CL100.000

Connections:
+3.3V: C270.1, L26.1
BBCLK_OUT: U38.M19 (IO_L13P_T2_MRCC_34)
CTRL_IN0: U38.V4 (IO_L21N_T3_DQS_13)
CTRL_IN1: U38.V5 (IO_L21P_T3_DQS_13)
CTRL_IN2: U38.U5 (IO_L22N_T3_13)
CTRL_IN3: U38.U6 (IO_L22P_T3_13)
CTRL_OUT0: U38.AB5 (IO_L16P_T2_13)
CTRL_OUT1: U38.AB6 (IO_L17N_T2_13)
CTRL_OUT2: U38.AB7 (IO_L17P_T2_13)
CTRL_OUT3: U38.AA4 (IO_L18N_T2_13)
CTRL_OUT5: U38.L19 (IO_L12N_T1_MRCC_34)
DATA_CLK: U38.L18 (IO_L12P_T1_MRCC_34)
ENABLE: U38.AB4 (IO_L16N_T2_13)
ENAGC: U38.AB2 (IO_L15P_T2_DQS_13)
FB_CLK: U38.R21 (IO_L17N_T2_34)
GND1: C268.2, C269.2, C270.2, R185.1, R186.1, Y3.3 (GROUND)
unnamed: C267.1, R187.2
unnamed: C267.2, R186.2, Y3.4 (OUTPUT)
unnamed: C268.1, C269.1, L26.2, Y3.6 (SUPPLY_VOLTAGE)
unnamed: R164.1, U38.AA17 (IO_L17P_T2_33)
unnamed: R165.1, U38.W18 (IO_L13N_T2_MRCC_33)
unnamed: R166.1, U38.W17 (IO_L13P_T2_MRCC_33)
unnamed: R167.1, U38.Y16 (IO_L14N_T2_SRCC_33)
unnamed: R168.1, U38.W16 (IO_L14P_T2_SRCC_33)
unnamed: R169.1, U38.U16 (IO_L15N_T2_DQS_33)
unnamed: R170.1, U38.U15 (IO_L15P_T2_DQS_33)
unnamed: R171.1, U38.V17 (IO_L16N_T2_33)
unnamed: R172.1, U38.U17 (IO_L16P_T2_33)
unnamed: R173.1, U38.AB17 (IO_L17N_T2_33)
unnamed: R174.1, U38.AB16 (IO_L18N_T2_33)
unnamed: R175.1, U38.AA16 (IO_L18P_T2_33)
unnamed: R176.1, U38.V14 (IO_L19P_T3_33)
unnamed: R177.1, U38.AB15 (IO_L24N_T3_33)
unnamed: R178.1, U38.AA14 (IO_L22N_T3_33)
unnamed: R179.1, U38.Y14 (IO_L22P_T3_33)
unnamed: R180.1, U38.AA13 (IO_L23N_T3_33)
unnamed: R181.1, U38.Y13 (IO_L23P_T3_33)
unnamed: R182.1, U38.AB14 (IO_L24P_T3_33)
P0_D8: U38.N20 (IO_L14N_T2_SRCC_34)
P1_D0: U38.N19 (IO_L14P_T2_SRCC_34)
P1_D1: U38.M21 (IO_L15P_T2_DQS_34)
P1_D2: U38.P20 (IO_L18P_T2_34)
P1_D4: U38.P17 (IO_L20P_T3_34)
P1_D5: U38.P18 (IO_L20N_T3_34)
P1_D6: U38.R20 (IO_L17P_T2_34)
P1_D7: U38.P21 (IO_L18N_T2_34)
P1_D8: U38.M22 (IO_L15N_T2_DQS_34)
P1_D9: U38.T17 (IO_L21N_T3_DQS_34)
P1_D10: U38.N22 (IO_L16P_T2_34)
P1_D11: U38.N15 (IO_L19P_T3_34)
PL_CK+: R184.1, U38.W15 (IO_L21P_T3_DQS_33)
PL_CK-: R183.1, U38.Y15 (IO_L21N_T3_DQS_33)
PL_DDR3_ADR1: R176.2
PL_DDR3_ADR2: R174.2
PL_DDR3_ADR3: R175.2
PL_DDR3_ADR4: R173.2
PL_DDR3_ADR5: R164.2
PL_DDR3_ADR6: R171.2
PL_DDR3_ADR7: R172.2
PL_DDR3_ADR8: R169.2
PL_DDR3_ADR9: R170.2
PL_DDR3_ADR10: R167.2
PL_DDR3_ADR11: R168.2
PL_DDR3_ADR12: R165.2
PL_DDR3_ADR13: R166.2
PL_DDR3_ADR14: R177.2
PL_DDR3_BA0: R179.2
PL_DDR3_BA1: U38.W13 (IO_L20N_T3_33)
PL_DDR3_BA2: U38.V13 (IO_L20P_T3_33)
PL_DDR3_CAS-: R181.2
PL_DDR3_CK+: C266.2, R184.2
PL_DDR3_CK-: C266.1, R183.2
PL_DDR3_CKE: R182.2, R185.2
PL_DDR3_DM1: U38.AA18 (IO_L12N_T1_MRCC_33)
PL_DDR3_RAS-: R178.2
PL_DDR3_SYSCK: R187.1, U38.Y18 (IO_L12P_T1_MRCC_33)
PL_DDR3_WE-: R180.2
SPI_CLK: U38.W5 (IO_L24N_T3_13)
SPI_DI: U38.V7 (IO_L23P_T3_13)
SPI_DO: U38.W7 (IO_L23N_T3_13)
SPI_ENB: U38.W6 (IO_L24P_T3_13)
SYNC_IN: U38.T16 (IO_L21P_T3_DQS_34)
TXNRX: U38.AB1 (IO_L15N_T2_DQS_13)
TX_FRAME: U38.P22 (IO_L16N_T2_34)

Notes on the sheet:
Internal pull-up resistor active output if pin 2 is left open
VCTCXO Not Used
SDR-B 7020 PL Mem Ctl., Clock
diff pair
M1SO
ETXO-H33CL-100.000 100 MHz TCXO
SCLK
M0SI
PL Memory Control/Clock and AD9361 Control Bus
PL_DDR3_ADR
Rcvr_bus
CTRL_OUT_bus
CTRL_IN_bus
