WA1CYB/SDR_Gen2/power-control-page4.kicad_sch

## KiCad design power-control-page4.kicad_sch (2026-04-03)

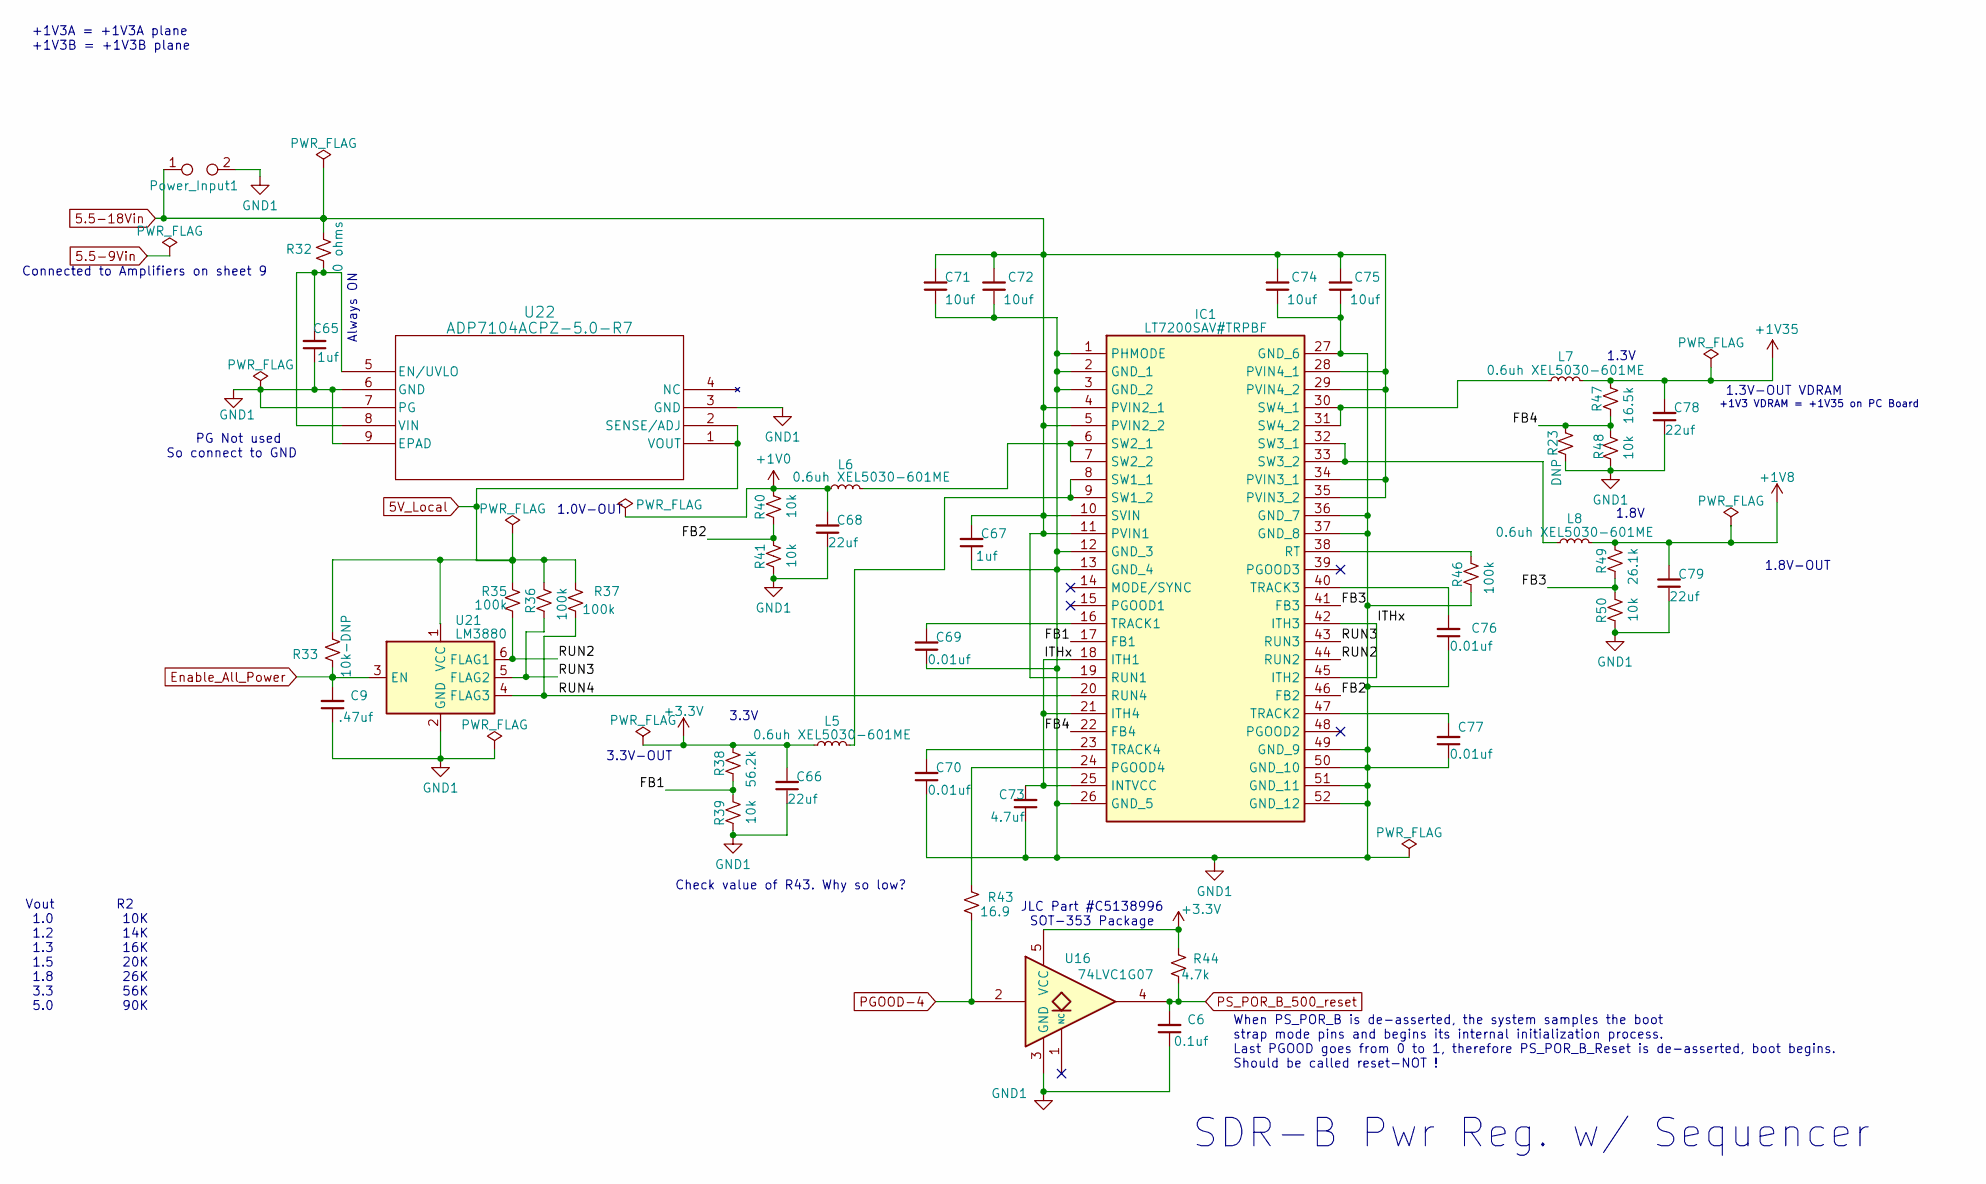
[picture p24: schematic power-control-page4.kicad_sch]

Parts:
C6: 0.1uf; C_0603_1608Metric
C9: .47uf; C_0805_2012Metric
C65: 1uf; C_0805_2012Metric
C66, C68, C78, C79: 22uf; C_0805_2012Metric
C67: 1uf; C_0402_1005Metric
C69, C70, C76, C77: 0.01uf; C_0201_0603Metric
C71, C72, C74, C75: 10uf; C_0805_2012Metric
C73: 4.7uf; C_0402_1005Metric
IC1: LT7200SAV#TRPBF; LT7200SAVTRPBF; Manufacturer_Part_Number LT7200SAV#TRPBF; Mouser Part Number 584-LT7200SAV#TRPBF
L5, L6, L7, L8: 0.6uh XEL5030-601ME; IND_XEL5030_3.2_COC
Power_Input1: TestPoint_2Pads_Pitch2.54mm_Drill0.8mm
R23: DNP; R_0201_0603Metric
R32: 0 ohms; R_0805_2012Metric
R33: 10k-DNP; R_0201_0603Metric
R35, R36, R37, R46: 100k; R_0201_0603Metric
R38: 56.2k; R_0201_0603Metric
R39, R40, R41, R48, R50: 10k; R_0201_0603Metric
R43: 16.9; R_0201_0603Metric
R44: 4.7k; R_0201_0603Metric
R47: 16.5k; R_0201_0603Metric
R49: 26.1k; R_0201_0603Metric
U16: 74LVC1G07; SOT-353_SC-70-5
U21: LM3880; SOT-23-6
U22: ADP7104ACPZ-5.0-R7; CP_8_5_ADI

Connections:
5.5-18Vin: C67.2, C71.2, C72.2, C74.2, C75.2, IC1.4 (PVIN2_1), IC1.5 (PVIN2_2), IC1.10 (SVIN), IC1.11 (PVIN1), IC1.19 (RUN1), IC1.28 (PVIN4_1), IC1.29 (PVIN4_2), IC1.34 (PVIN3_1), IC1.35 (PVIN3_2), Power_Input1.1, R32.2
5V_Local: R33.2, R35.2, R36.2, R37.2, U21.1 (VCC), U22.1 (VOUT), U22.2 (SENSE/ADJ)
+1V0: C68.2, L6.1, R40.2
+1V8: C79.2, L8.2, R49.2
+1V35: C78.2, L7.2, R47.2
+3.3V: C66.2, L5.1, R38.2, R44.1, U16.5 (VCC)
Enable_All_Power: C9.2, R33.1, U21.3 (EN)
FB1: IC1.17 (FB1), R38.1, R39.2
FB2: IC1.46 (FB2), R40.1, R41.2
FB3: IC1.41 (FB3), R49.1, R50.2
FB4: IC1.22 (FB4), R23.2, R47.1, R48.2
GND1: C6.1, C9.1, C65.1, C66.1, C67.1, C68.1, C69.1, C70.1, C71.1, C72.1, C73.1, C74.1, C75.1, C76.1, C77.1, C78.1, C79.1, IC1.1 (PHMODE), IC1.2 (GND_1), IC1.3 (GND_2), IC1.12 (GND_3), IC1.13 (GND_4), IC1.26 (GND_5), IC1.27 (GND_6), IC1.36 (GND_7), IC1.37 (GND_8), IC1.49 (GND_9), IC1.50 (GND_10), IC1.51 (GND_11), IC1.52 (GND_12), Power_Input1.2, R23.1, R39.1, R41.1, R46.1, R48.1, R50.1, U16.3 (GND), U21.2 (GND), U22.3 (GND), U22.6 (GND), U22.7 (PG), U22.9 (EPAD)
ITHx: C73.2, IC1.18 (ITH1), IC1.21 (ITH4), IC1.25 (INTVCC), IC1.42 (ITH3), IC1.45 (ITH2)
unnamed: C65.2, R32.1, U22.5 (EN/UVLO), U22.8 (VIN)
unnamed: C69.2, IC1.16 (TRACK1)
unnamed: C70.2, IC1.23 (TRACK4)
unnamed: C76.2, IC1.40 (TRACK3)
unnamed: C77.2, IC1.47 (TRACK2)
unnamed: IC1.6 (SW2_1), IC1.7 (SW2_2), L6.2
unnamed: IC1.8 (SW1_1), IC1.9 (SW1_2), L5.2
unnamed: IC1.24 (PGOOD4), R43.1
unnamed: IC1.30 (SW4_1), IC1.31 (SW4_2), L7.1
unnamed: IC1.32 (SW3_1), IC1.33 (SW3_2), L8.1
unnamed: IC1.38 (RT), R46.2
PGOOD-4: R43.2, U16.2
PS_POR_B_500_reset: C6.2, R44.2, U16.4
RUN2: IC1.44 (RUN2), R35.1, U21.6 (FLAG1)
RUN3: IC1.43 (RUN3), R36.1, U21.5 (FLAG2)
RUN4: IC1.20 (RUN4), R37.1, U21.4 (FLAG3)

Notes on the sheet:
+1V3A = +1V3A plane +1V3B = +1V3B plane
When PS_POR_B is de-asserted, the system samples the boot strap mode pins and begins its internal initialization process. Last PGOOD goes from 0 to 1, therefore PS_POR_B_Reset is de-asserted, boot begins. Should be called reset-NOT !
Check value of R43. Why so low?
1.3V
PG Not used So connect to GND
1.3V-OUT VDRAM
Connected to Amplifiers on sheet 9
1.8V
Vout R2 1.0 10K 1.2 14K 1.3 16K 1.5 20K 1.8 26K 3.3 56K 5.0 90K
3.3V-OUT
JLC Part #C5138996 SOT-353 Package
3.3V
Always ON
SDR-B Pwr Reg. w/ Sequencer
1.0V-OUT
1.8V-OUT
+1V3 VDRAM = +1V35 on PC Board
