WA1CYB/SDR_Gen2/power-page 5.kicad_sch

## KiCad design power-page 5.kicad_sch (2026-04-03)

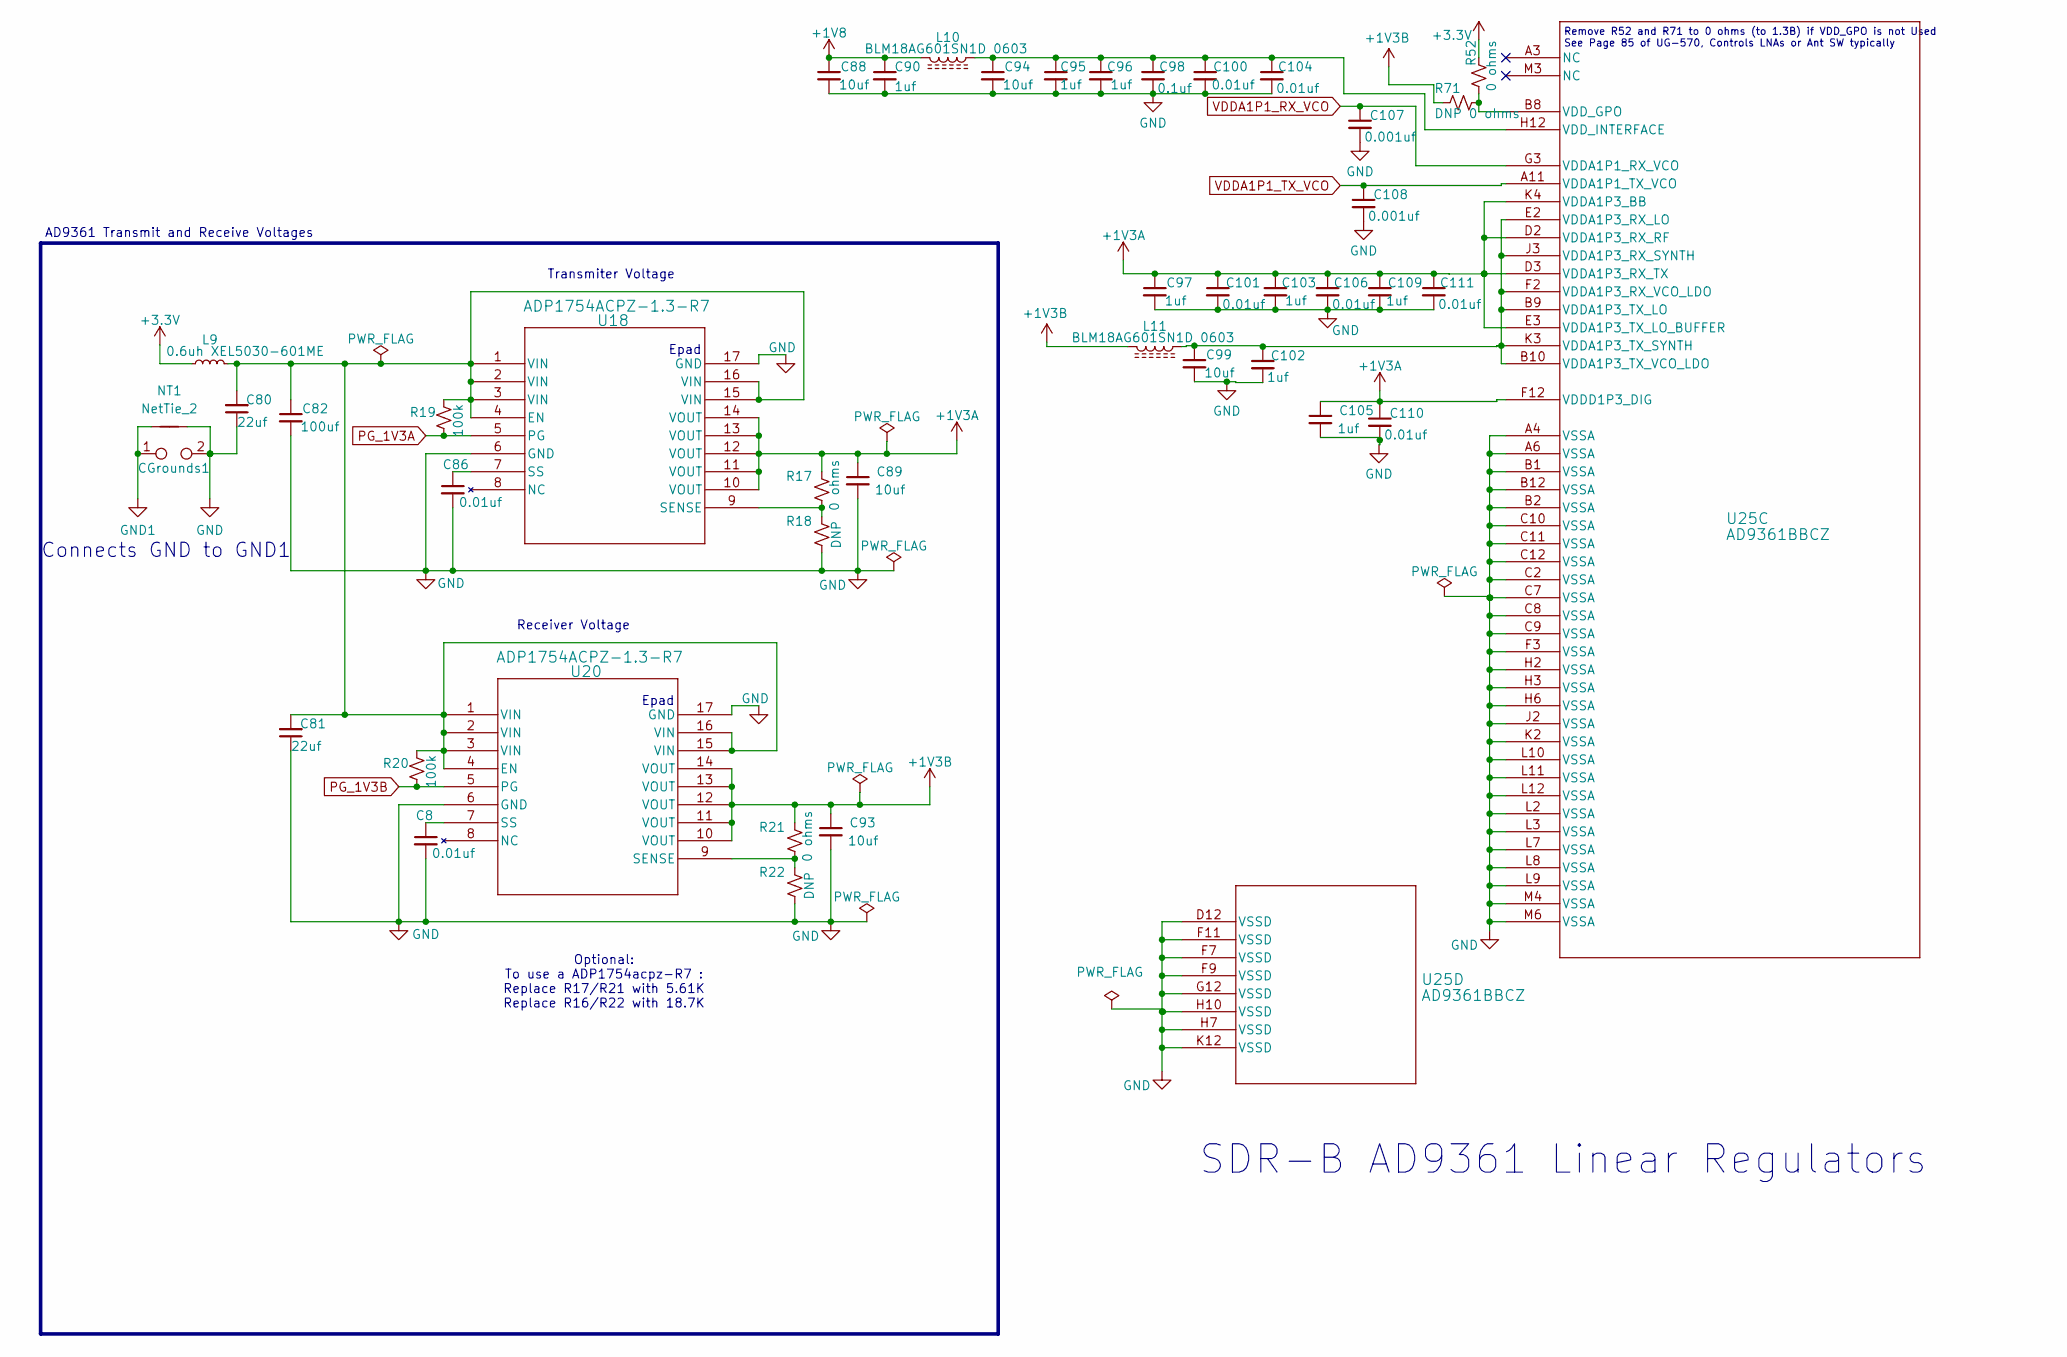
[picture p25: schematic power-page 5.kicad_sch]

Parts:
C8, C86: 0.01uf; C_0402_1005Metric
C80, C81: 22uf; C_0805_2012Metric
C82: 100uf; C_1206_3216Metric
C88, C89, C93, C94, C99: 10uf; C_0805_2012Metric
C90, C95, C96, C97, C102, C103, C105, C109: 1uf; C_0402_1005Metric
C98: 0.1uf; C_0201_0603Metric
C100, C101, C104, C106, C110, C111: 0.01uf; C_0201_0603Metric
C107, C108: 0.001uf; C_0201_0603Metric
CGrounds1: TestPoint_2Pads_Pitch2.54mm_Drill0.8mm
L9: 0.6uh XEL5030-601ME; IND_XEL5030_3.2_COC
L10, L11: BLM18AG601SN1D 0603; IND_BLM18_0603_MUR
NT1: NetTie_2; NetTie-2_THT_Pad0.3mm
R17, R21: 0 ohms; R_0402_1005Metric
R18, R22: DNP; R_0402_1005Metric
R19, R20: 100k; R_0201_0603Metric
R52: 0 ohms; R_0201_0603Metric
R71: DNP 0 ohms; R_0603_1608Metric
U18, U20: ADP1754ACPZ-1.3-R7; CP-16-23_ADI-L
U25: AD9361BBCZ; BC_144_7_ADI

Connections:
+1V3A: C89.1, C97.1, C101.1, C103.1, C105.1, C106.1, C109.1, C110.1, C111.1, R17.2, U18.10 (VOUT), U18.11 (VOUT), U18.12 (VOUT), U18.13 (VOUT), U18.14 (VOUT), U25.D2 (VDDA1P3_RX_RF), U25.D3 (VDDA1P3_RX_TX), U25.E3 (VDDA1P3_TX_LO_BUFFER), U25.F12 (VDDD1P3_DIG), U25.K4 (VDDA1P3_BB)
+1V3B: C93.1, L11.2, R21.2, R71.2, U20.10 (VOUT), U20.11 (VOUT), U20.12 (VOUT), U20.13 (VOUT), U20.14 (VOUT)
+1V8: C88.1, C90.1, L10.2
+3.3V: L9.1, R52.2
GND: C8.2, C80.1, C81.1, C82.2, C86.2, C88.2, C89.2, C90.2, C93.2, C94.2, C95.2, C96.2, C97.2, C98.2, C99.2, C100.2, C101.2, C102.2, C103.2, C104.2, C105.2, C106.2, C107.2, C108.2, C109.2, C110.2, C111.2, CGrounds1.2, NT1.2, R18.1, R22.1, U18.6 (GND), U18.17 (GND), U20.6 (GND), U20.17 (GND), U25.A4 (VSSA), U25.A6 (VSSA), U25.B1 (VSSA), U25.B2 (VSSA), U25.B12 (VSSA), U25.C2 (VSSA), U25.C7 (VSSA), U25.C8 (VSSA), U25.C9 (VSSA), U25.C10 (VSSA), U25.C11 (VSSA), U25.C12 (VSSA), U25.D12 (VSSD), U25.F3 (VSSA), U25.F7 (VSSD), U25.F9 (VSSD), U25.F11 (VSSD), U25.G12 (VSSD), U25.H2 (VSSA), U25.H3 (VSSA), U25.H6 (VSSA), U25.H7 (VSSD), U25.H10 (VSSD), U25.J2 (VSSA), U25.K2 (VSSA), U25.K12 (VSSD), U25.L2 (VSSA), U25.L3 (VSSA), U25.L7 (VSSA), U25.L8 (VSSA), U25.L9 (VSSA), U25.L10 (VSSA), U25.L11 (VSSA), U25.L12 (VSSA), U25.M4 (VSSA), U25.M6 (VSSA)
GND1: CGrounds1.1, NT1.1
unnamed: C8.1, U20.7 (SS)
unnamed: C80.2, C81.2, C82.1, L9.2, R19.2, R20.2, U18.1 (VIN), U18.2 (VIN), U18.3 (VIN), U18.4 (EN), U18.15 (VIN), U18.16 (VIN), U20.1 (VIN), U20.2 (VIN), U20.3 (VIN), U20.4 (EN), U20.15 (VIN), U20.16 (VIN)
unnamed: C86.1, U18.7 (SS)
unnamed: C94.1, C95.1, C96.1, C98.1, C100.1, C104.1, L10.1, U25.H12 (VDD_INTERFACE)
unnamed: C99.1, C102.1, L11.1, U25.B9 (VDDA1P3_TX_LO), U25.B10 (VDDA1P3_TX_VCO_LDO), U25.E2 (VDDA1P3_RX_LO), U25.F2 (VDDA1P3_RX_VCO_LDO), U25.J3 (VDDA1P3_RX_SYNTH), U25.K3 (VDDA1P3_TX_SYNTH)
unnamed: R17.1, R18.2, U18.9 (SENSE)
unnamed: R21.1, R22.2, U20.9 (SENSE)
unnamed: R52.1, R71.1, U25.B8 (VDD_GPO)
PG_1V3A: R19.1, U18.5 (PG)
PG_1V3B: R20.1, U20.5 (PG)
VDDA1P1_RX_VCO: C107.1, U25.G3 (VDDA1P1_RX_VCO)
VDDA1P1_TX_VCO: C108.1, U25.A11 (VDDA1P1_TX_VCO)

Notes on the sheet:
SDR-B AD9361 Linear Regulators
Epad
Optional: To use a ADP1754acpz-R7 : Replace R17/R21 with 5.61K Replace R16/R22 with 18.7K
Receiver Voltage
Connects GND to GND1
Remove R52 and R71 to 0 ohms (to 1.3B) if VDD_GPO is not Used See Page 85 of UG-570, Controls LNAs or Ant SW typically
Transmiter Voltage
AD9361 Transmit and Receive Voltages
